hc625ma/simchair_models/Mods/Peripherals/AB412 collective head/VR MAX radio+ panel mod/PNG/nav_side_panel_connections.png

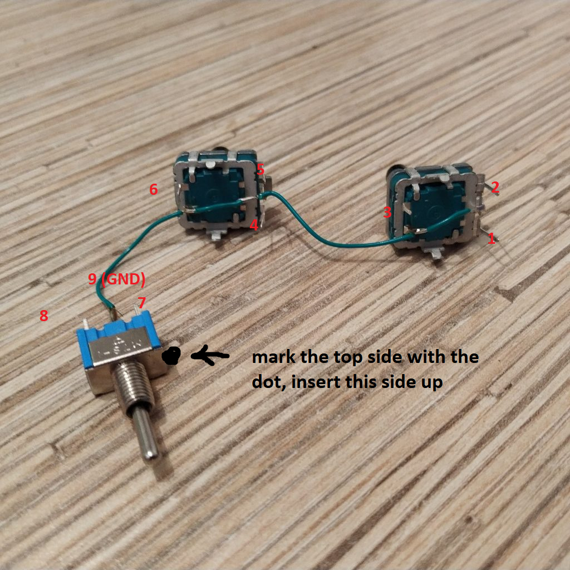
Mods/Peripherals/AB412 collective head/VR MAX radio+ panel mod/PNG/nav_side_panel_connections.png
