hc625ma/simchair_models/Mods/Peripherals/AB412 collective head/VR MAX radio+ panel mod/PNG/vrmax1.png

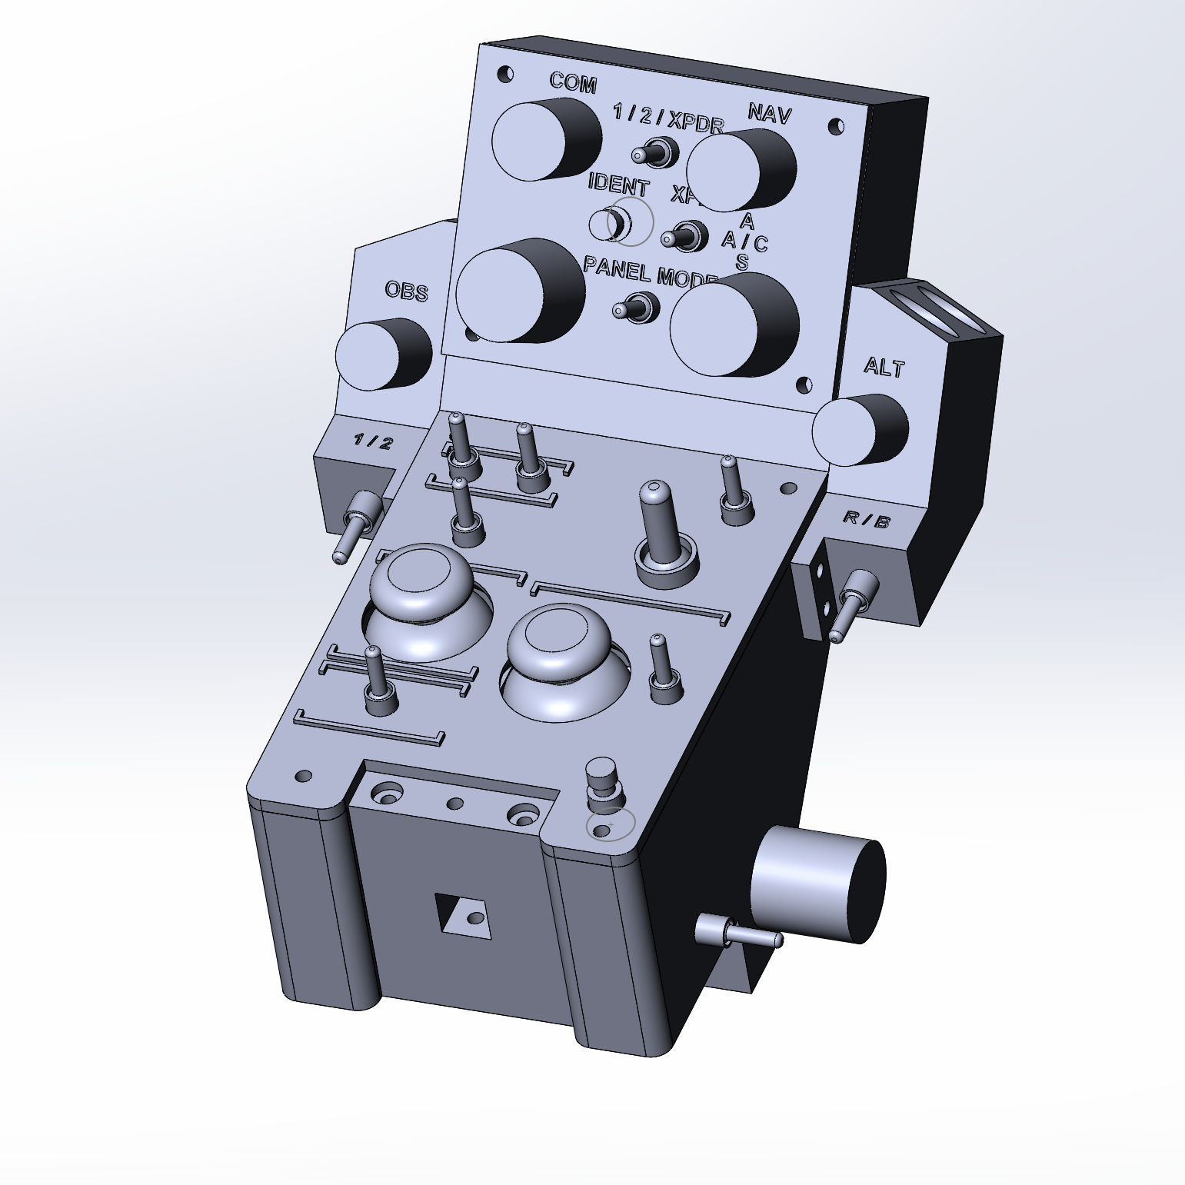
Mods/Peripherals/AB412 collective head/VR MAX radio+ panel mod/PNG/vrmax1.png
