hc625ma/simchair_models/Mods/Peripherals/Collective levers/All levers/Housing with a revision hatch mod/Rubber band version/PNG/housing_with_revision_hatch_rubber_bands_version_01.png

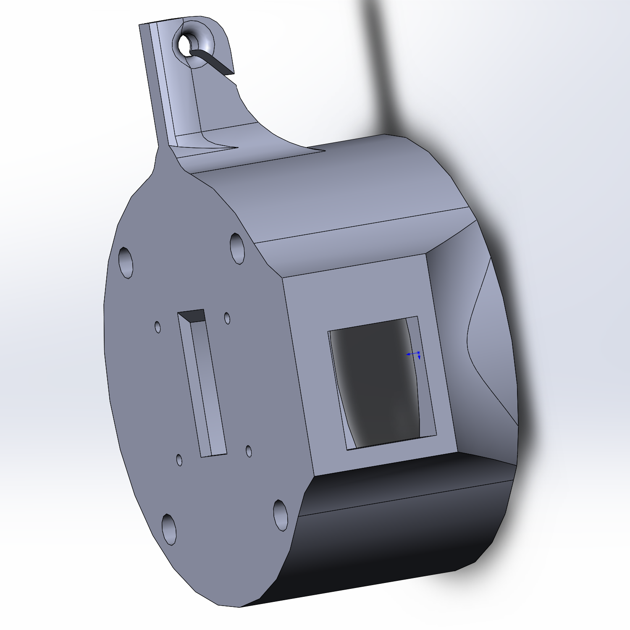
Mods/Peripherals/Collective levers/All levers/Housing with a revision hatch mod/Rubber band version/PNG/housing_with_revision_hatch_rubber_bands_version_01.png
