hc625ma/simchair_models/Mods/Peripherals/Collective levers/All levers/Pneumatic actuator mod/PNG/pneumatic_mod01.png

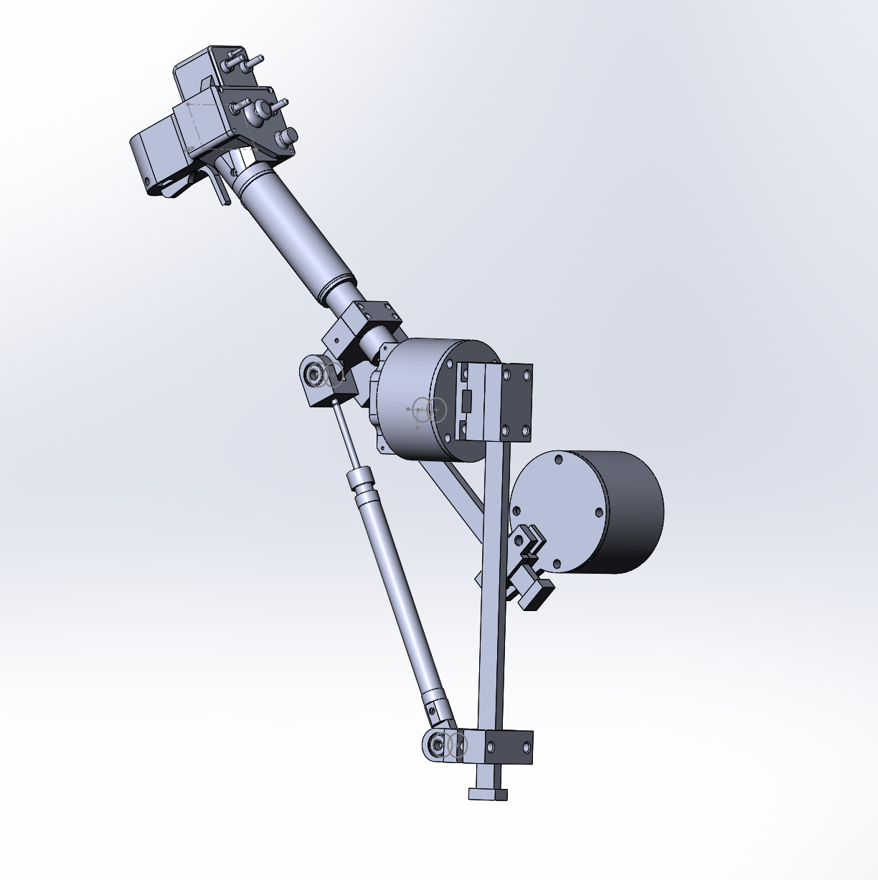
Mods/Peripherals/Collective levers/All levers/Pneumatic actuator mod/PNG/pneumatic_mod01.png
