hc625ma/simchair_models/Mods/Peripherals/Collective levers/Single engine collective/Physical throttle latch mod/PNG/physical_throttle_latch_mod_02.png

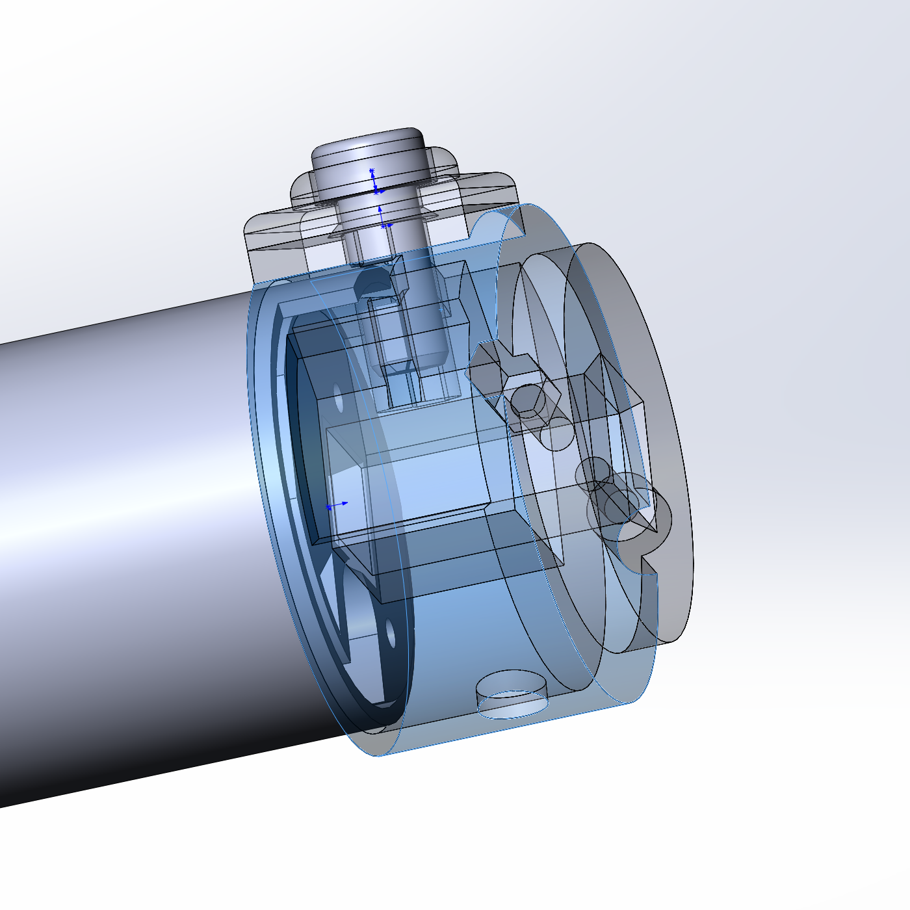
Mods/Peripherals/Collective levers/Single engine collective/Physical throttle latch mod/PNG/physical_throttle_latch_mod_02.png
