hc625ma/simchair_models/Components/Controllers/Simchair MKIII I2C controller/PNG/controller.png

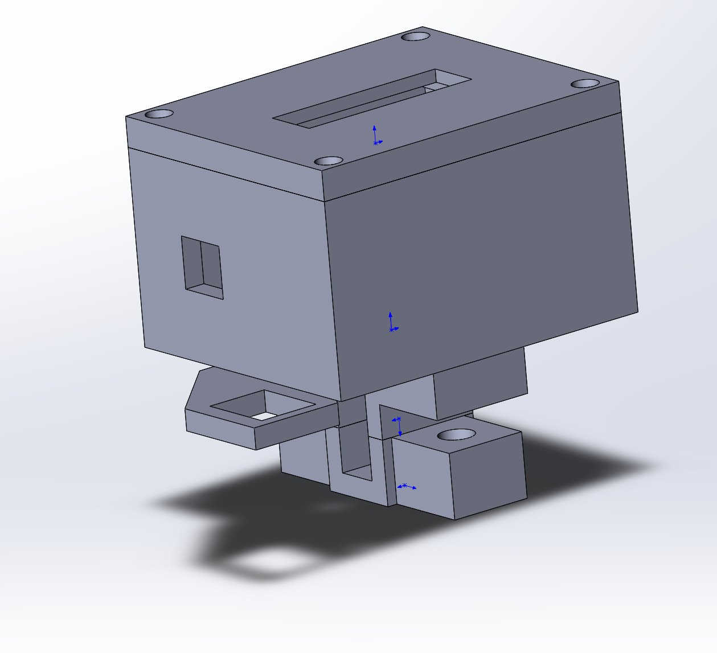
Components/Controllers/Simchair MKIII I2C controller/PNG/controller.png
