hc625ma/simchair_models/Components/Peripherals/Flight stick gimbal 608zz light/PNG/gimbal.png

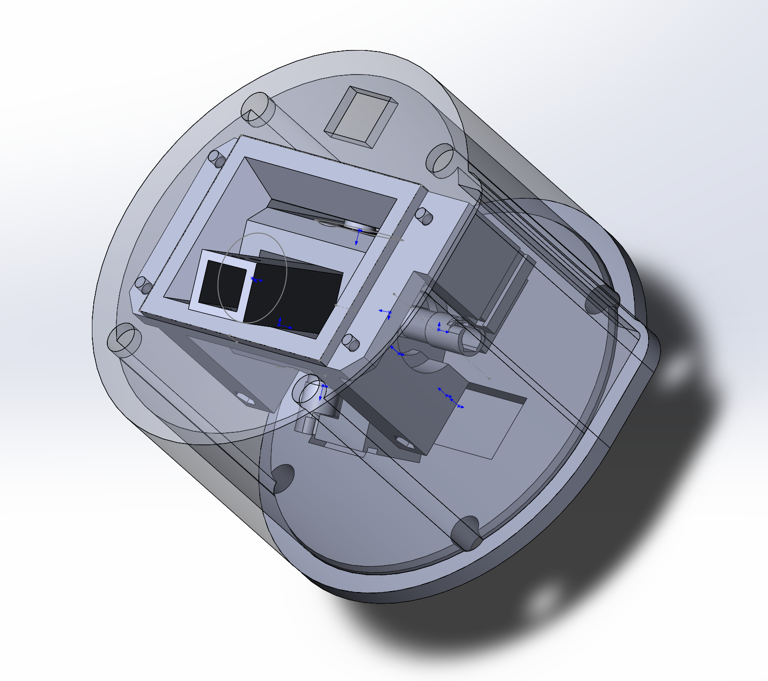
Components/Peripherals/Flight stick gimbal 608zz light/PNG/gimbal.png
