hc625ma/simchair_models/Components/Peripherals/Flight stick gimbal 608zz light/PNG/gimbal_mount_v2.png

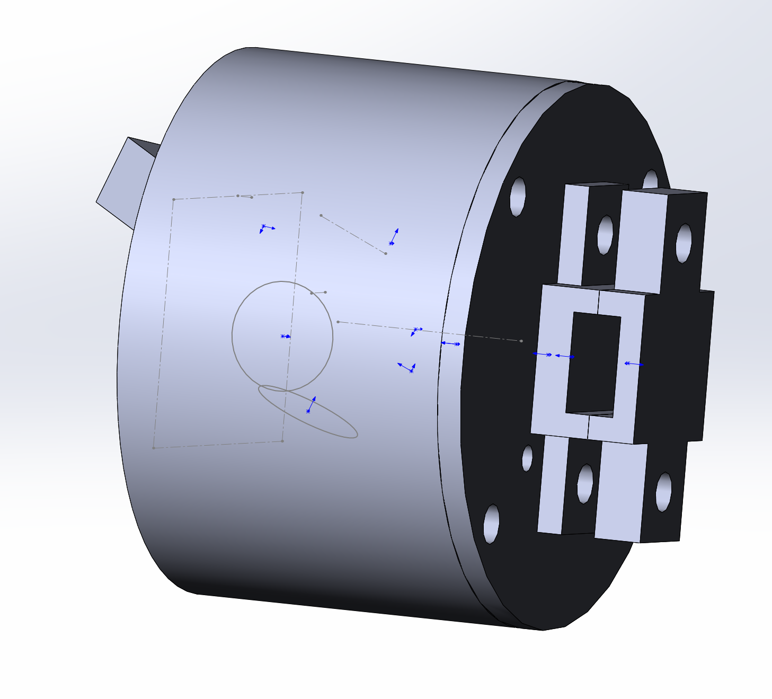
Components/Peripherals/Flight stick gimbal 608zz light/PNG/gimbal_mount_v2.png
