hc625ma/simchair_models/Components/Peripherals/Flight stick gimbal 608zz light/PNG/P_20180517_164954.jpg

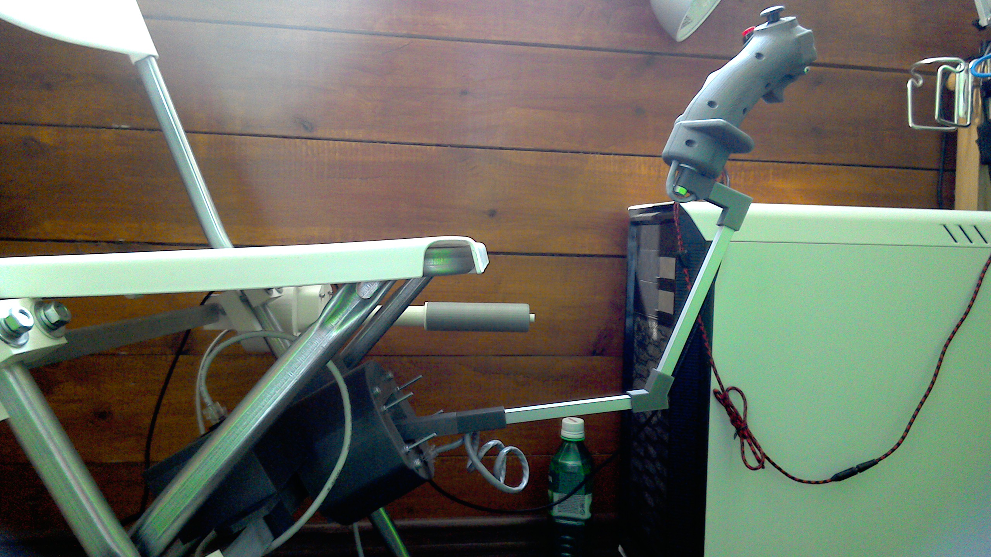
Components/Peripherals/Flight stick gimbal 608zz light/PNG/P_20180517_164954.jpg
