hc625ma/simchair_models/Components/Peripherals/Flight stick gimbal 608zz reinforced/PNG/exploded_view_2.png

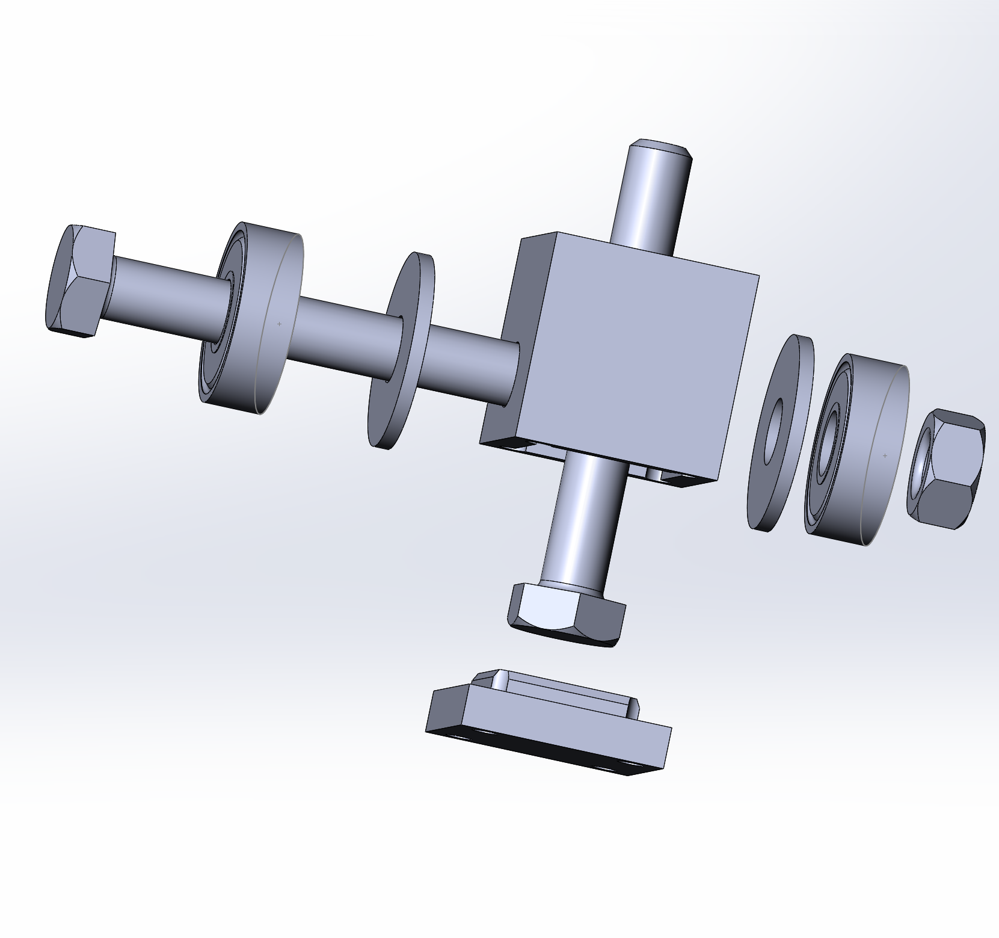
Components/Peripherals/Flight stick gimbal 608zz reinforced/PNG/exploded_view_2.png
