hc625ma/simchair_models/Components/Peripherals/Flight stick gimbal 608zz reinforced/PNG/gimbal01.jpg

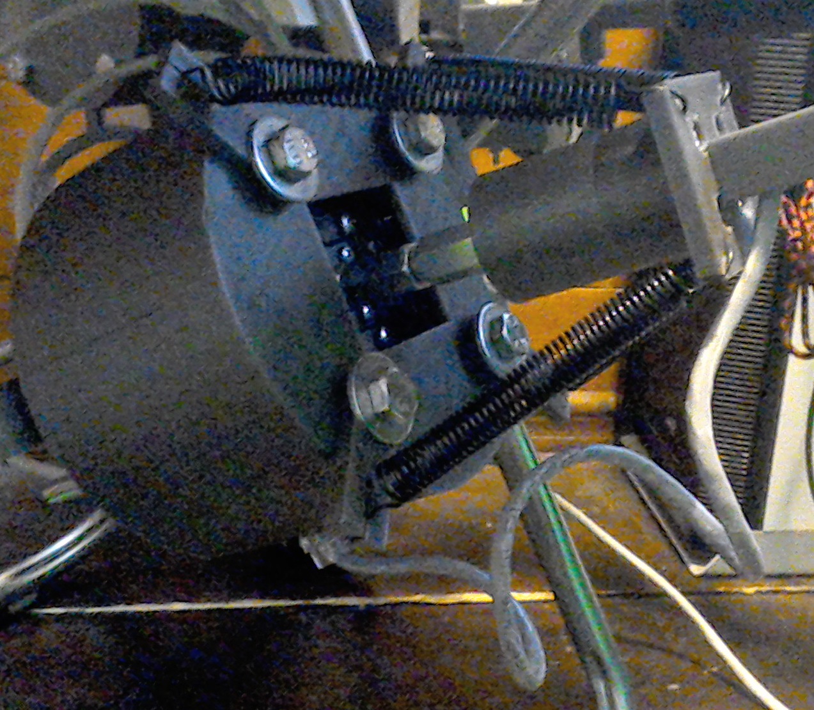
Components/Peripherals/Flight stick gimbal 608zz reinforced/PNG/gimbal01.jpg
