hc625ma/simchair_models/Components/Peripherals/Flight stick gimbal 608zz reinforced/PNG/gimbal08.png

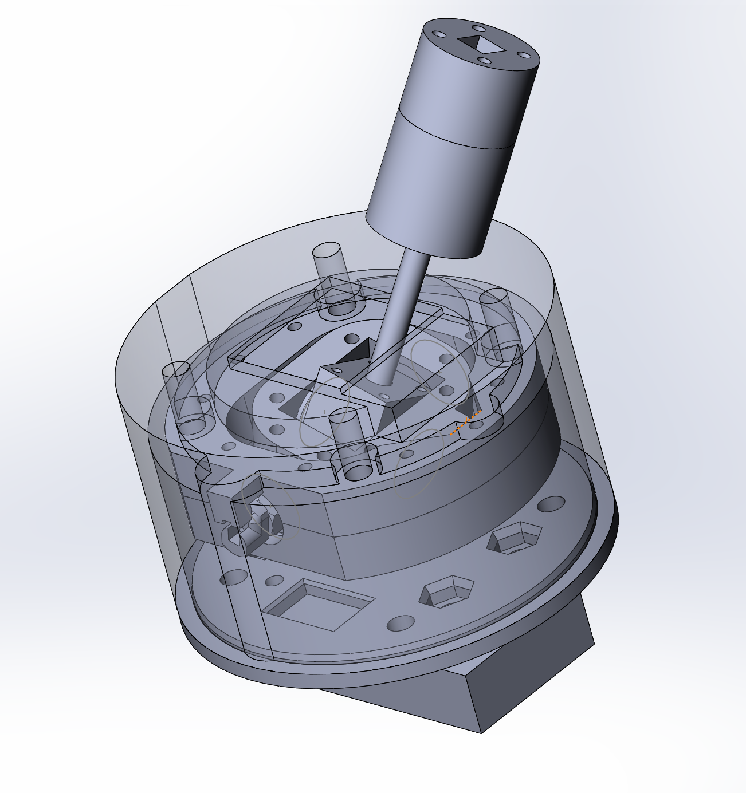
Components/Peripherals/Flight stick gimbal 608zz reinforced/PNG/gimbal08.png
