hc625ma/simchair_models/Components/Peripherals/Helicopter pedals/PNG/magnet and ss495a mounts.JPG

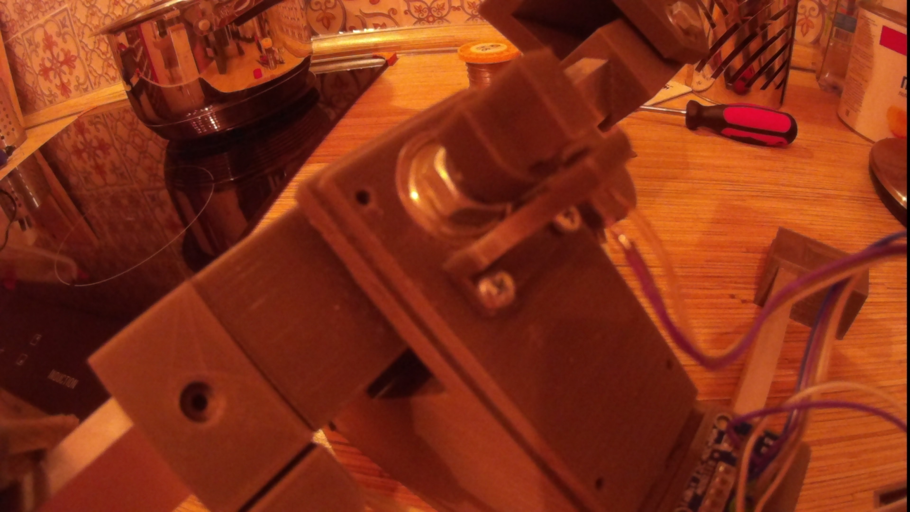
Components/Peripherals/Helicopter pedals/PNG/magnet and ss495a mounts.JPG
