hc625ma/simchair_models/Components/Peripherals/dev/Flight stick gimbal GE25 ES-2RS/SLDPRT/gimbal GE25 ES-2RS.SLDASM

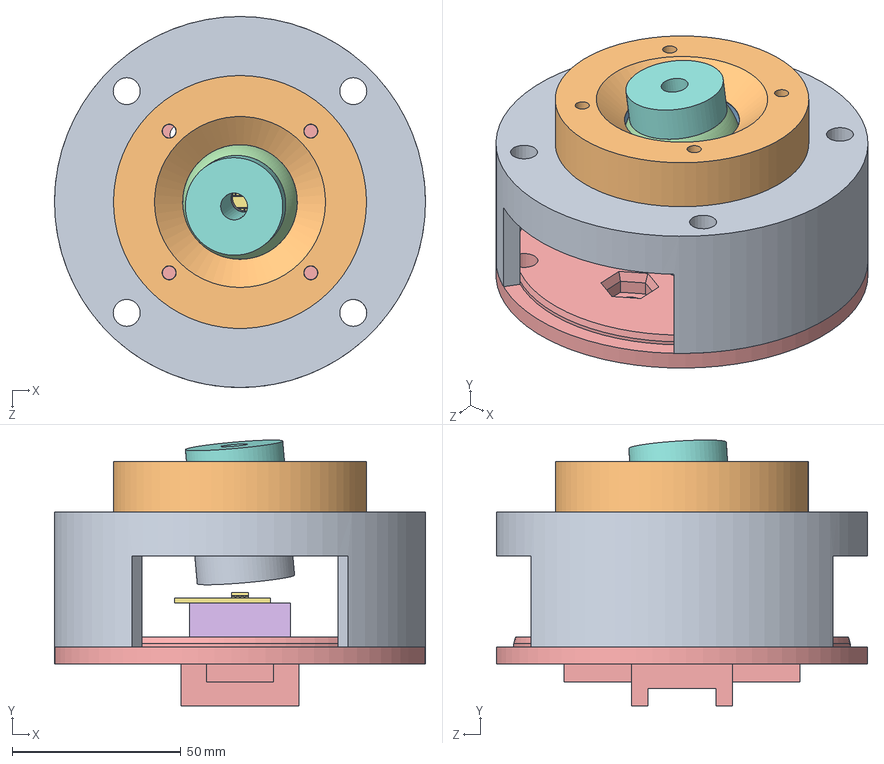
[picture p40: CAD file, 2018-10-22]
Components/Peripherals/dev/Flight stick gimbal GE25 ES-2RS/SLDPRT/gimbal GE25 ES-2RS.SLDASM
110.0 x 78.9 x 110.0 mm
gimbal_housing_testbed_gimbal01a
gimbal_housing_p2_gimbal02
outer_ring
inner_ring
gimbal_housing_bottom_p1_gimbal03
gimbal_cjmcu_frame_gimbal05
CJMCU-93
gimbal_stick_connector_p1_gimbal06
gimbal_stick_connector_p2_gimbal06
