hc625ma/simchair_models/Components/Peripherals/dev/Helicopter throttle quadrant/SLDPRT/throttle_quadrant_module_v3.SLDASM

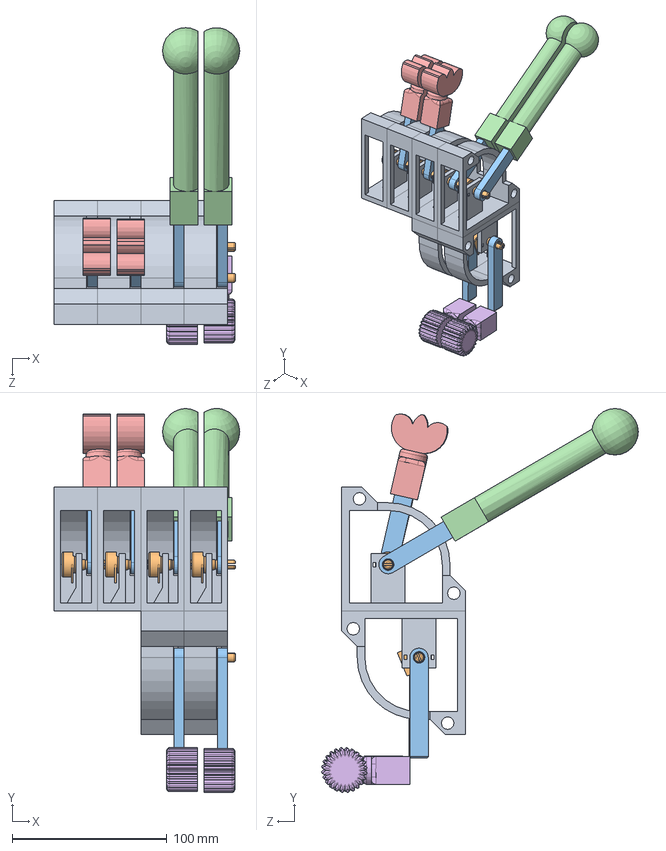
[picture p41: CAD file, 2019-05-10]
Components/Peripherals/dev/Helicopter throttle quadrant/SLDPRT/throttle_quadrant_module_v3.SLDASM
120.0 x 248.2 x 204.7 mm
throttle_quadrant_axis_module_throttle_quadrant01a x 6
16K1-B10K x 6
throttle_quadrant_axis_module_slider_throttle_quadrant02a x 6
mi8_throttle x 2
prop_knob x 2
mix_knob x 2
