hc625ma/simchair_models/Components/Peripherals/Helicopter pedals/SLDPRT/pedals_main_frame_pedals01.SLDPRT

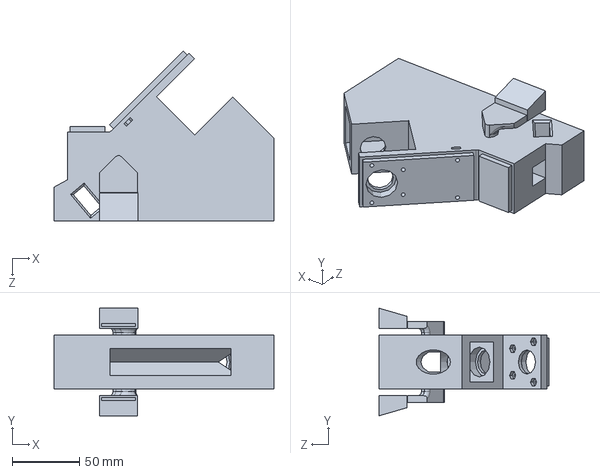
[picture p42: CAD file, 2018-12-12]
Components/Peripherals/Helicopter pedals/SLDPRT/pedals_main_frame_pedals01.SLDPRT
163.6 x 80.0 x 126.1 mm
