hc625ma/simchair_models/Components/Peripherals/Helicopter pedals/SLDPRT/pedals_main_frame_pedals01_backup.SLDPRT

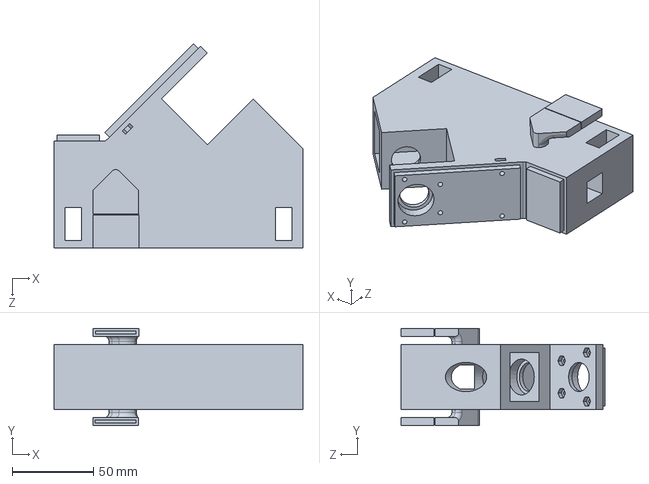
[picture p43: CAD file, 2018-08-10]
Components/Peripherals/Helicopter pedals/SLDPRT/pedals_main_frame_pedals01_backup.SLDPRT
153.6 x 60.0 x 126.1 mm
