hc625ma/simchair_models/Components/Peripherals/dev/Helicopter throttle quadrant/SLDPRT/throttle_quadrant_module.SLDASM

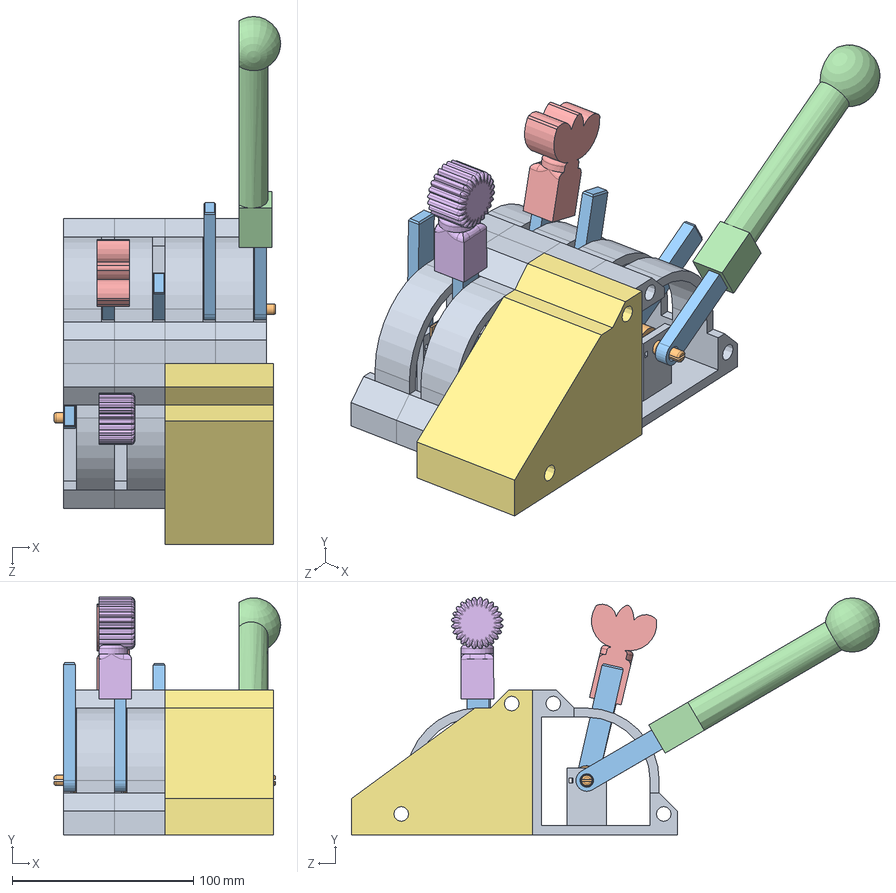
[picture p44: CAD file, 2019-05-10]
Components/Peripherals/dev/Helicopter throttle quadrant/SLDPRT/throttle_quadrant_module.SLDASM
125.2 x 131.2 x 291.7 mm
throttle_quadrant_axis_module_throttle_quadrant01a x 6
16K1-B10K x 6
throttle_quadrant_axis_module_slider_throttle_quadrant02a x 6
mi8_throttle
prop_knob
mix_knob
switch_panel2
