hc625ma/simchair_models/Components/Peripherals/dev/Helicopter throttle quadrant/SLDPRT/quadrant_axis.SLDASM

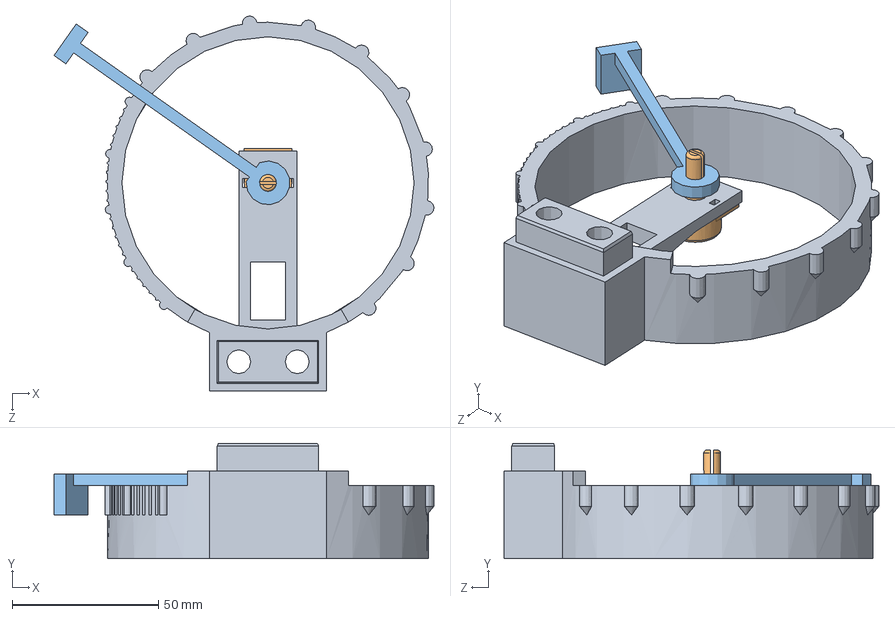
[picture p45: CAD file, 2018-10-25]
Components/Peripherals/dev/Helicopter throttle quadrant/SLDPRT/quadrant_axis.SLDASM
130.1 x 39.5 x 128.4 mm
throttle_quadrant_axis_module_throttle_quadrant01
16K1-B10K
throttle_quadrant_axis_module_slider_throttle_quadrant02
