hc625ma/simchair_models/Components/Peripherals/dev/Helicopter throttle quadrant/SLDPRT/throttle_quadrant_6_axis.SLDASM

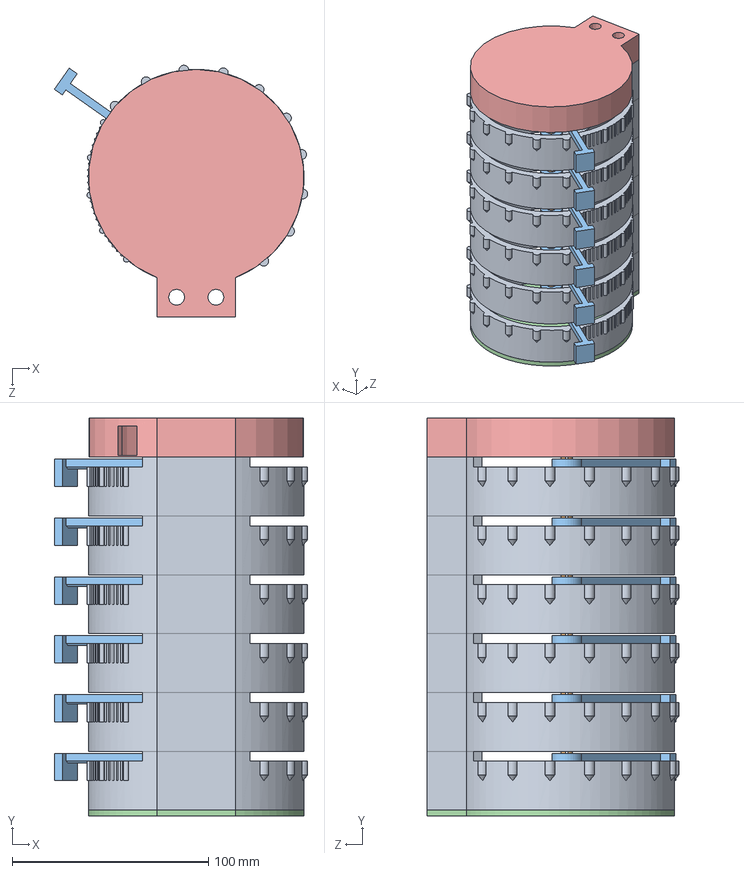
[picture p46: CAD file, 2018-10-25]
Components/Peripherals/dev/Helicopter throttle quadrant/SLDPRT/throttle_quadrant_6_axis.SLDASM
129.2 x 203.0 x 128.4 mm
throttle_quadrant_axis_module_throttle_quadrant01 x 6
16K1-B10K x 6
throttle_quadrant_axis_module_slider_throttle_quadrant02 x 6
throttle_quadrant_left_lid_throttle_quadrant03
throttle_quadrant_right_lid_throttle_quadrant04
