hc625ma/simchair_models/Components/Controllers/Simchair MKIII I2C controller/SLDPRT/controller_enclosure_p1_controller01.SLDPRT

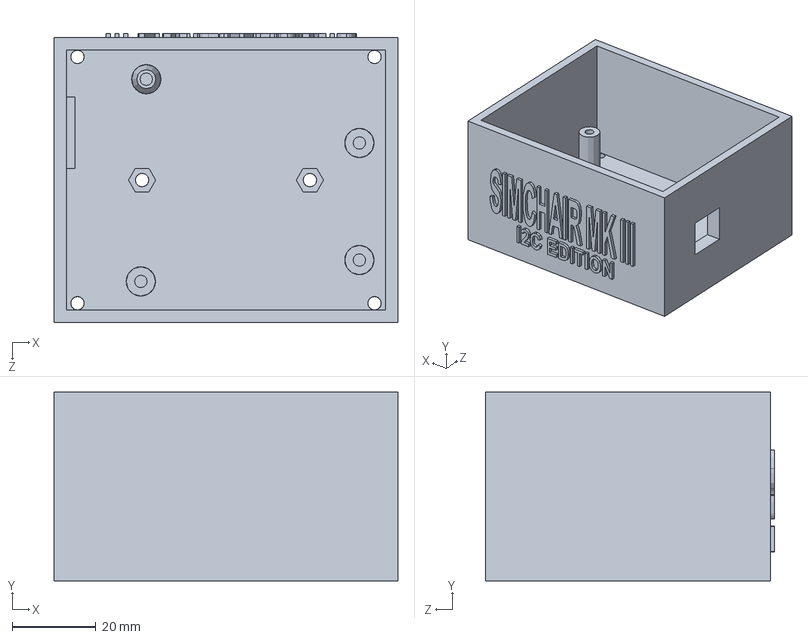
[picture p47: CAD file, 2018-08-29]
Components/Controllers/Simchair MKIII I2C controller/SLDPRT/controller_enclosure_p1_controller01.SLDPRT
82.0 x 45.0 x 69.0 mm
