hc625ma/simchair_models/Components/Frames/40mm construction profile frame/Collective mount/40mm_profile_bracket_p1.SLDPRT

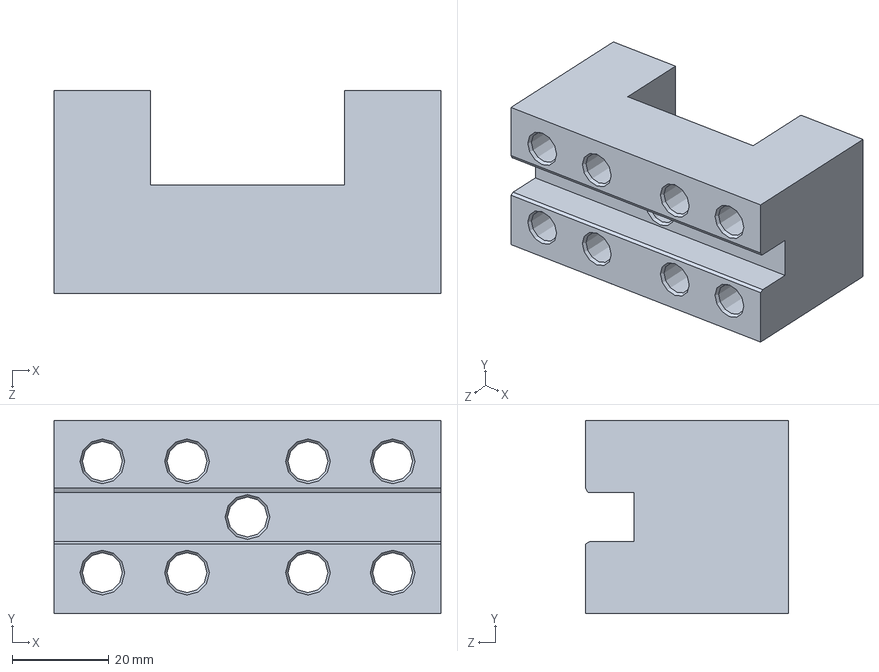
[picture p48: CAD file, 2019-05-31]
Components/Frames/40mm construction profile frame/Collective mount/40mm_profile_bracket_p1.SLDPRT
80.0 x 40.0 x 42.0 mm
