hc625ma/simchair_models/Components/Frames/Generic Chair with vertical round legs/SLDPRT/generic_chair_frame_collective_mount_back_generic_chair03.SLDPRT

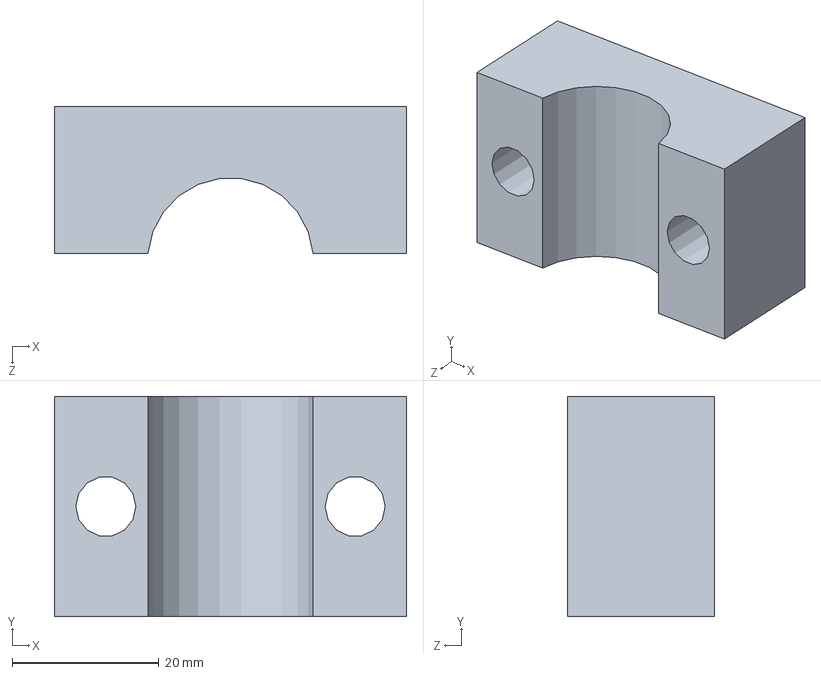
[picture p49: CAD file, 2018-10-19]
Components/Frames/Generic Chair with vertical round legs/SLDPRT/generic_chair_frame_collective_mount_back_generic_chair03.SLDPRT
48.0 x 30.0 x 20.0 mm
