hc625ma/simchair_models/Components/Frames/IKEA GUNDE frame/Chair mounts/SLDPRT/ikea_gunde_frame_throttle_quadrant_frame_mount_p1_ikea_gunde_frame07.SLDPRT

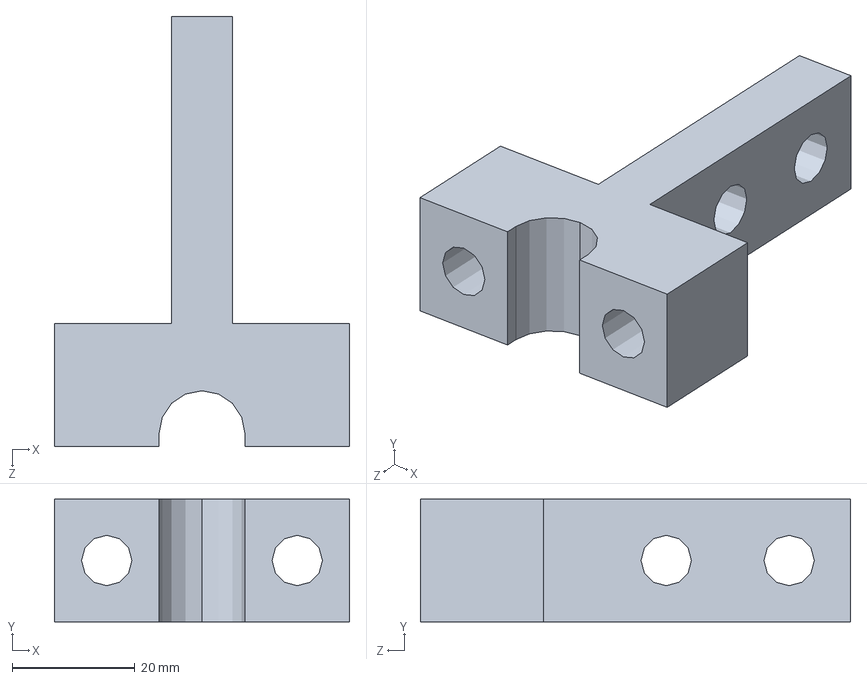
[picture p50: CAD file, 2018-10-25]
Components/Frames/IKEA GUNDE frame/Chair mounts/SLDPRT/ikea_gunde_frame_throttle_quadrant_frame_mount_p1_ikea_gunde_frame07.SLDPRT
48.0 x 20.0 x 70.0 mm
