hc625ma/simchair_models/Components/Frames/IKEA GUNDE frame/Chair mounts/STL/ikea_gunde_chair_back_mount_malinda_plate.stl

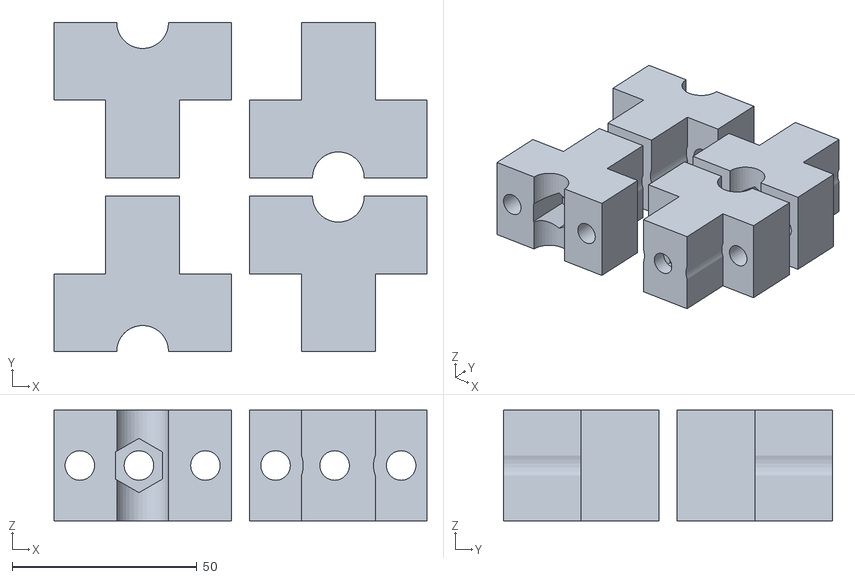
[picture p51: CAD file, 2018-08-11]
Components/Frames/IKEA GUNDE frame/Chair mounts/STL/ikea_gunde_chair_back_mount_malinda_plate.stl
101.0 x 89.0 x 30.0
