hc625ma/simchair_models/Components/Frames/IKEA GUNDE frame/Cyclic stick frame parts/Non-spring-loaded stick/SLDPRT/gunde_cyclic_frame_stick_grip_connector_pvc_3_4_inch_incr_clearance_vertical_gunde_cyclic_frame04c.SLDPRT

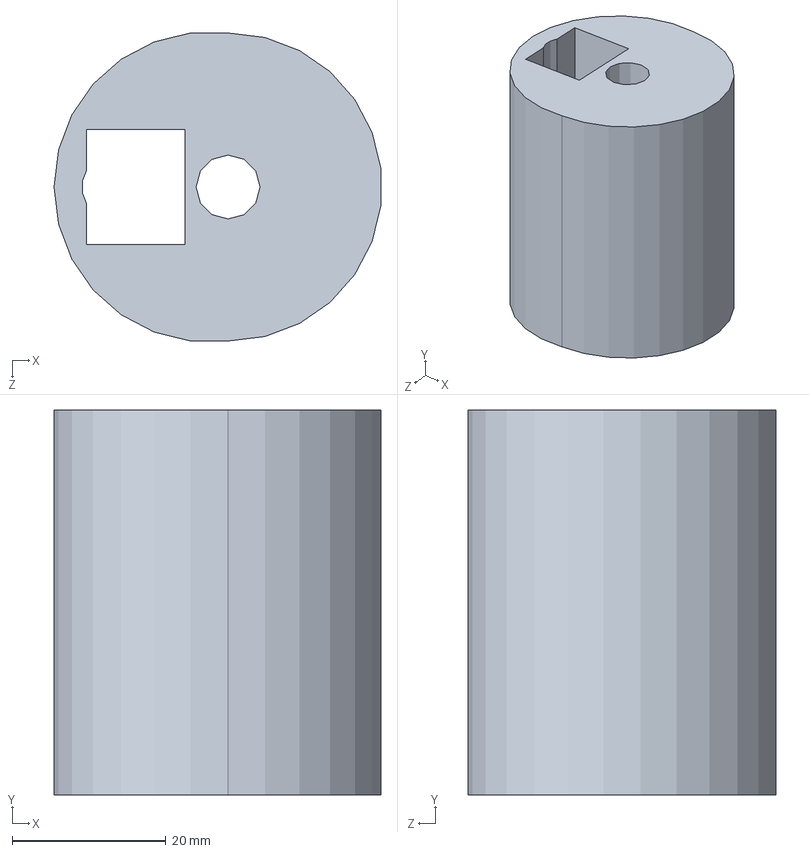
[picture p52: CAD file, 2019-02-21]
Components/Frames/IKEA GUNDE frame/Cyclic stick frame parts/Non-spring-loaded stick/SLDPRT/gunde_cyclic_frame_stick_grip_connector_pvc_3_4_inch_incr_clearance_vertical_gunde_cyclic_frame04c.SLDPRT
42.5 x 50.0 x 40.0 mm
