hc625ma/simchair_models/Components/Frames/IKEA GUNDE frame/Cyclic stick frame parts/Spring-loaded stick/SLDPRT/spring_loaded_cyclic_frame_stick_connector_150_deg_spring_loaded_cyclic_frame01.SLDPRT

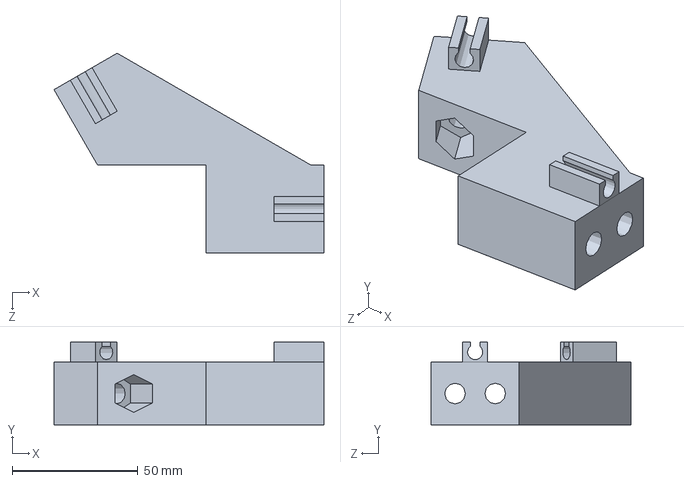
[picture p53: CAD file, 2018-12-24]
Components/Frames/IKEA GUNDE frame/Cyclic stick frame parts/Spring-loaded stick/SLDPRT/spring_loaded_cyclic_frame_stick_connector_150_deg_spring_loaded_cyclic_frame01.SLDPRT
107.5 x 33.0 x 79.5 mm
