hc625ma/simchair_models/Components/Peripherals/AB412 collective head/SLDPRT/ab412_head_enclosure_p1_ab412_head01.SLDPRT

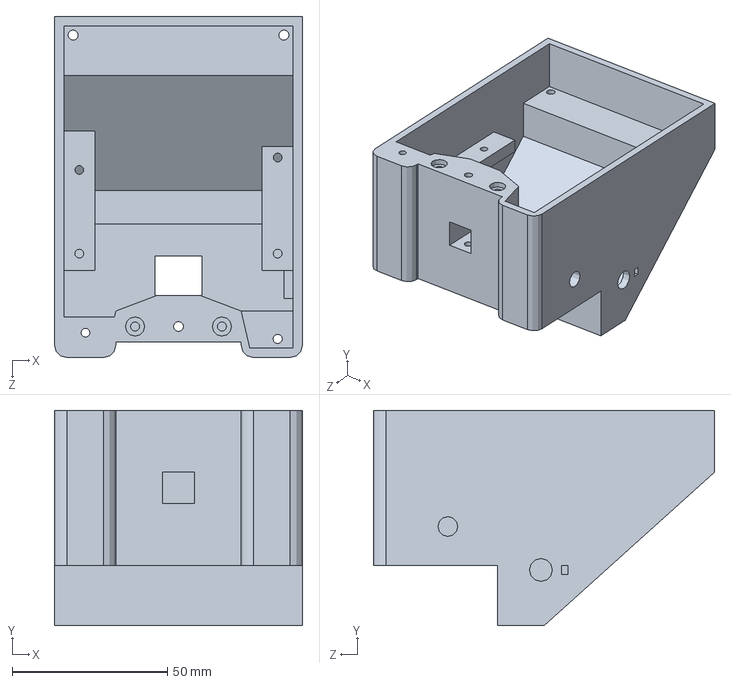
[picture p54: CAD file, 2018-09-01]
Components/Peripherals/AB412 collective head/SLDPRT/ab412_head_enclosure_p1_ab412_head01.SLDPRT
80.0 x 69.5 x 110.0 mm
