hc625ma/simchair_models/Components/Peripherals/AB412 collective head/STL/ab412_head_pot_knob_ab412_head04.STL

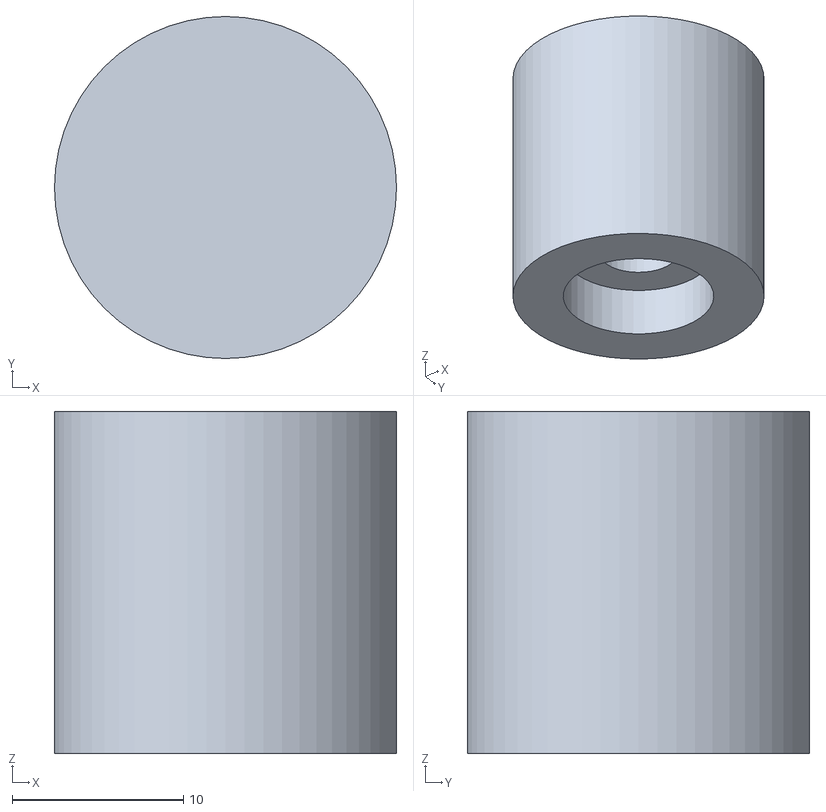
[picture p55: CAD file, 2018-09-01]
Components/Peripherals/AB412 collective head/STL/ab412_head_pot_knob_ab412_head04.STL
20.0 x 20.0 x 20.0
