hc625ma/simchair_models/Components/Peripherals/B8 flight stick/STL/b8stick_left_half_b8stick02.STL

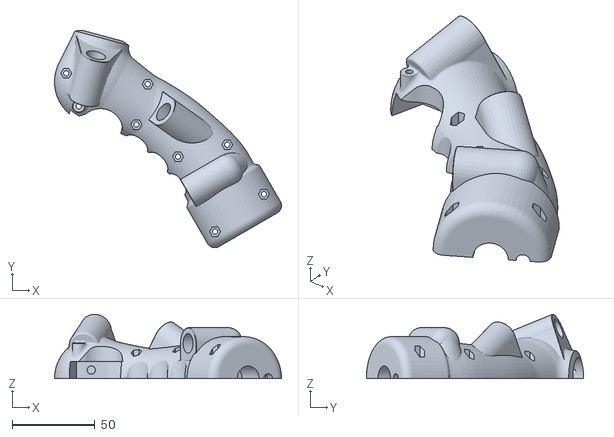
[picture p56: CAD file, 2018-09-20]
Components/Peripherals/B8 flight stick/STL/b8stick_left_half_b8stick02.STL
137.1 x 131.3 x 38.8
