hc625ma/simchair_models/Components/Peripherals/dev/B206 collective head/SLDPRT/b206_head_enclosure_p1_b206_head01.SLDPRT

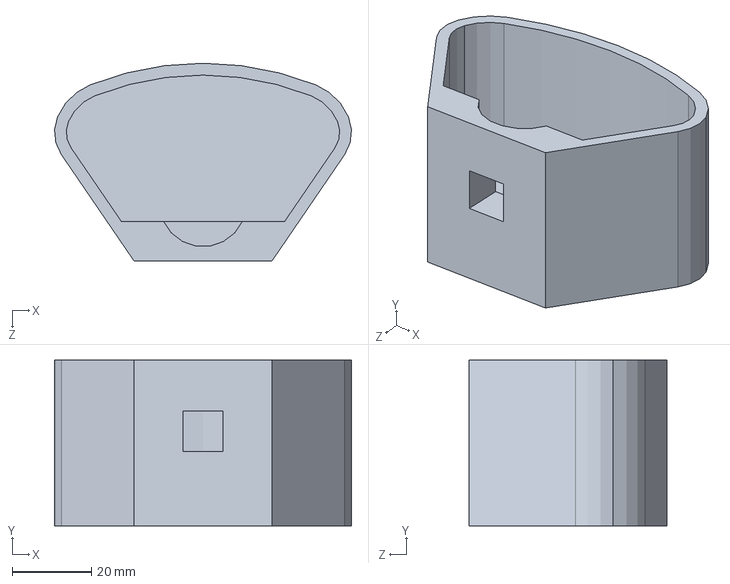
[picture p57: CAD file, 2019-03-17]
Components/Peripherals/dev/B206 collective head/SLDPRT/b206_head_enclosure_p1_b206_head01.SLDPRT
75.2 x 42.0 x 50.0 mm
