hc625ma/simchair_models/Components/Peripherals/dev/Flight stick gimbal 608zz CJMCU-93/Assembly1/gimbal_housing.SLDPRT

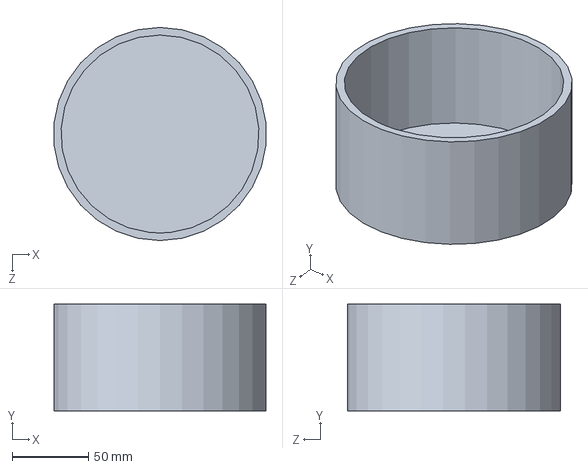
[picture p58: CAD file, 2018-10-22]
Components/Peripherals/dev/Flight stick gimbal 608zz CJMCU-93/Assembly1/gimbal_housing.SLDPRT
139.2 x 70.0 x 140.0 mm
