hc625ma/simchair_models/Components/Peripherals/dev/Flight stick gimbal 608zz reinforced v2/SLDPRT/gimbal_outer_ring_top_gimbal04.SLDPRT

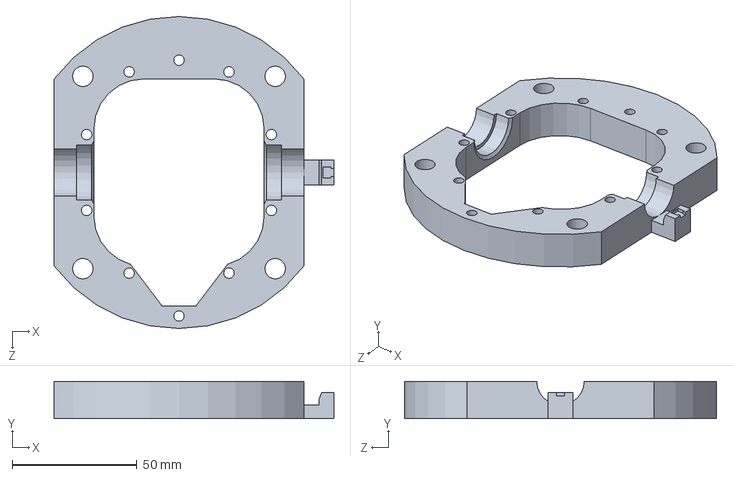
[picture p59: CAD file, 2019-05-10]
Components/Peripherals/dev/Flight stick gimbal 608zz reinforced v2/SLDPRT/gimbal_outer_ring_top_gimbal04.SLDPRT
112.0 x 15.0 x 125.0 mm
