hc625ma/simchair_models/Components/Peripherals/dev/Flight stick gimbal GE25 ES-2RS/SLDPRT/gimbal_cjmcu_frame_gimbal05.SLDPRT

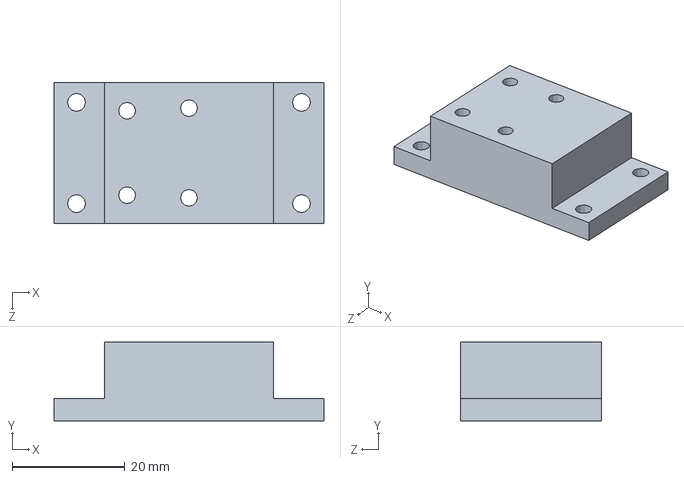
[picture p60: CAD file, 2018-10-22]
Components/Peripherals/dev/Flight stick gimbal GE25 ES-2RS/SLDPRT/gimbal_cjmcu_frame_gimbal05.SLDPRT
48.0 x 14.0 x 25.0 mm
