hc625ma/simchair_models/Components/Peripherals/dev/Helicopter throttle quadrant/SLDPRT/switch_panel2.SLDPRT

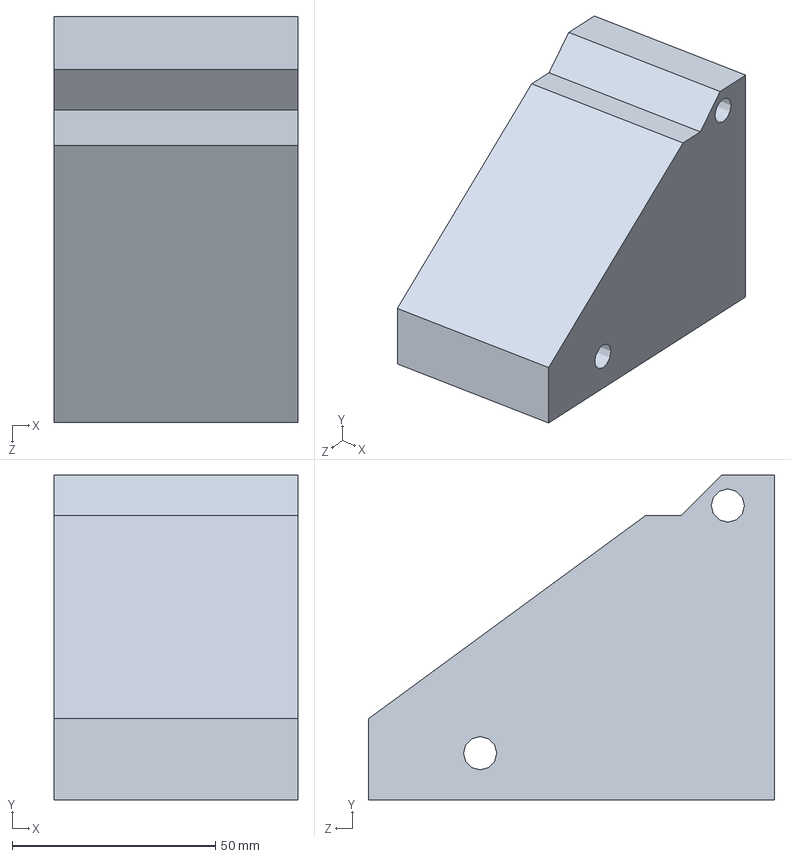
[picture p61: CAD file, 2019-05-10]
Components/Peripherals/dev/Helicopter throttle quadrant/SLDPRT/switch_panel2.SLDPRT
60.0 x 80.0 x 100.0 mm
