hc625ma/simchair_models/Components/Peripherals/dev/Simple collective/STL/throttle_200deg.STL

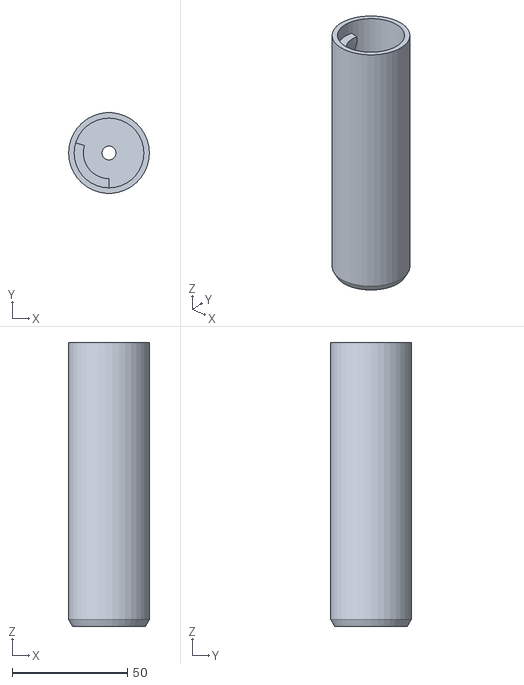
[picture p62: CAD file, 2019-02-21]
Components/Peripherals/dev/Simple collective/STL/throttle_200deg.STL
35.0 x 34.9 x 123.0
