hc625ma/simchair_models/Components/Peripherals/Flight stick gimbal 608zz reinforced/STL/gimbal_housing_lid_p1_gimbal02.STL

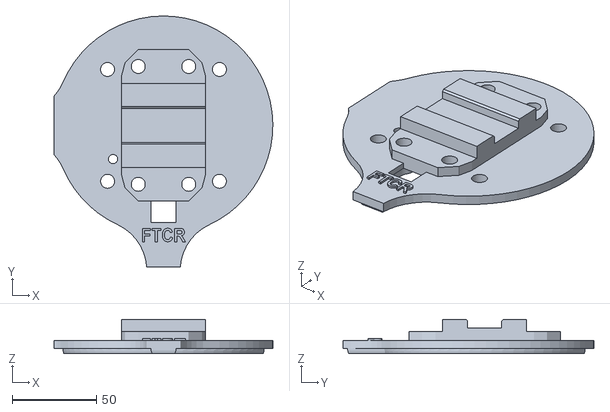
[picture p63: CAD file, 2019-03-17]
Components/Peripherals/Flight stick gimbal 608zz reinforced/STL/gimbal_housing_lid_p1_gimbal02.STL
130.0 x 149.2 x 20.5
