hc625ma/simchair_models/Components/Peripherals/Huey collective head/STL/huey_head_enclosure_p1_huey_head01.STL

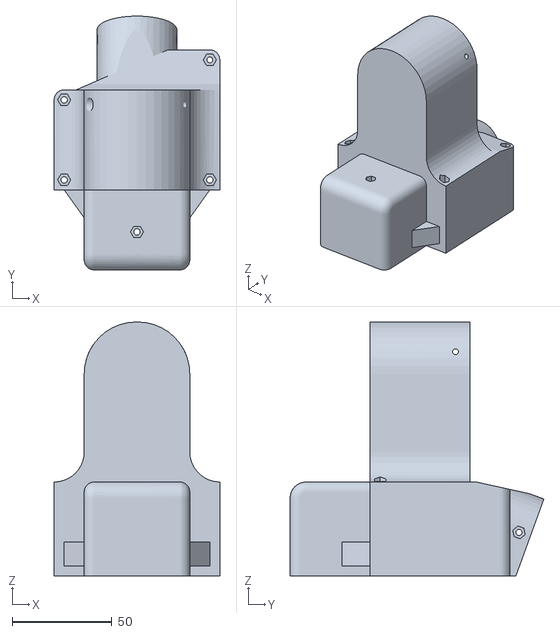
[picture p64: CAD file, 2018-08-29]
Components/Peripherals/Huey collective head/STL/huey_head_enclosure_p1_huey_head01.STL
82.8 x 126.9 x 127.0
