hc625ma/simchair_models/Components/Peripherals/Single collective/SLDPRT/single_collective_throttle_frame_p2_single_collective10.SLDPRT

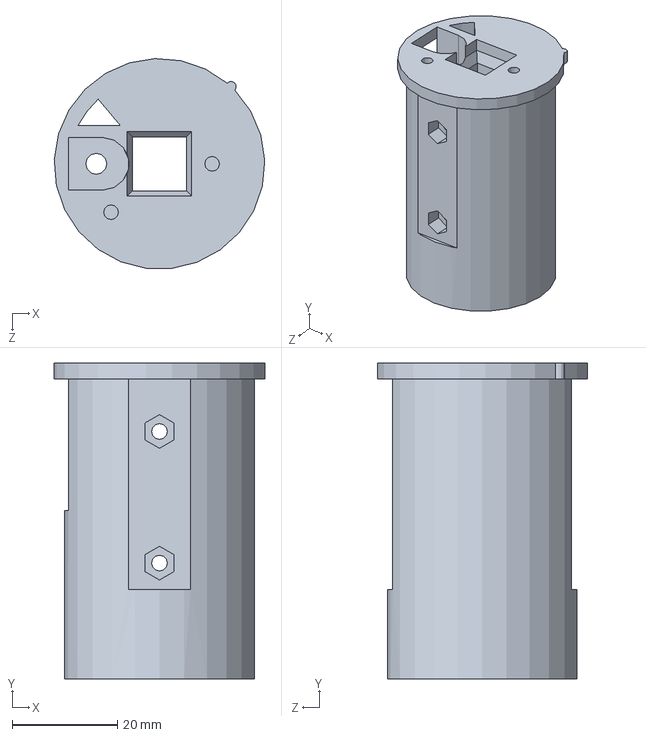
[picture p65: CAD file, 2019-05-10]
Components/Peripherals/Single collective/SLDPRT/single_collective_throttle_frame_p2_single_collective10.SLDPRT
40.0 x 60.0 x 39.8 mm
