hc625ma/simchair_models/Components/Peripherals/Single collective/STL/single_collective_lever_connector_single_collective05a.STL

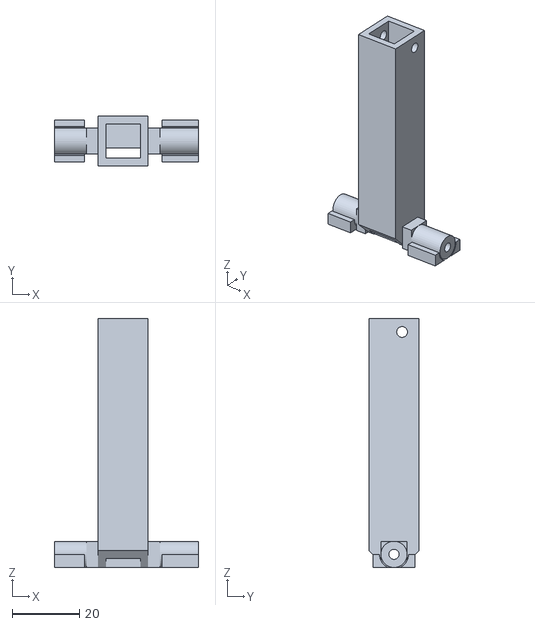
[picture p66: CAD file, 2019-05-10]
Components/Peripherals/Single collective/STL/single_collective_lever_connector_single_collective05a.STL
42.8 x 14.8 x 74.0
