hc625ma/simchair_models/Components/Peripherals/Twin collective/STL/twin_collective_enclosure_bottom_p2_twin_collective03.STL

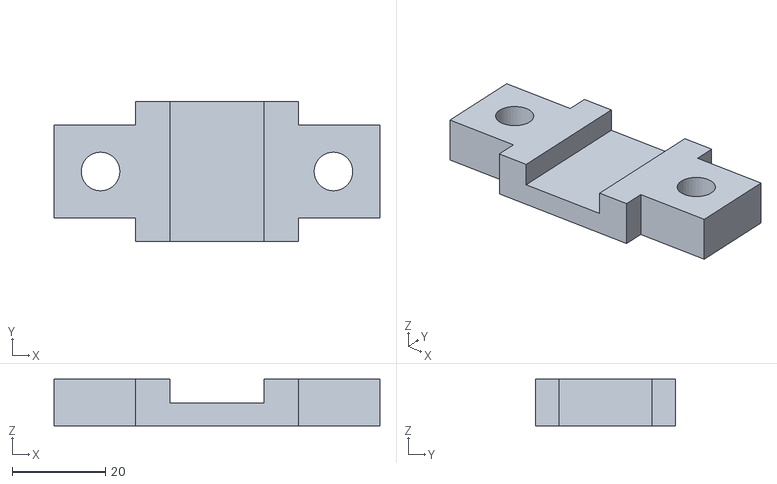
[picture p67: CAD file, 2018-08-11]
Components/Peripherals/Twin collective/STL/twin_collective_enclosure_bottom_p2_twin_collective03.STL
70.0 x 30.0 x 10.0
