hc625ma/simchair_models/Hardware Models/Buttons/PBS-11/pbs11.SLDPRT

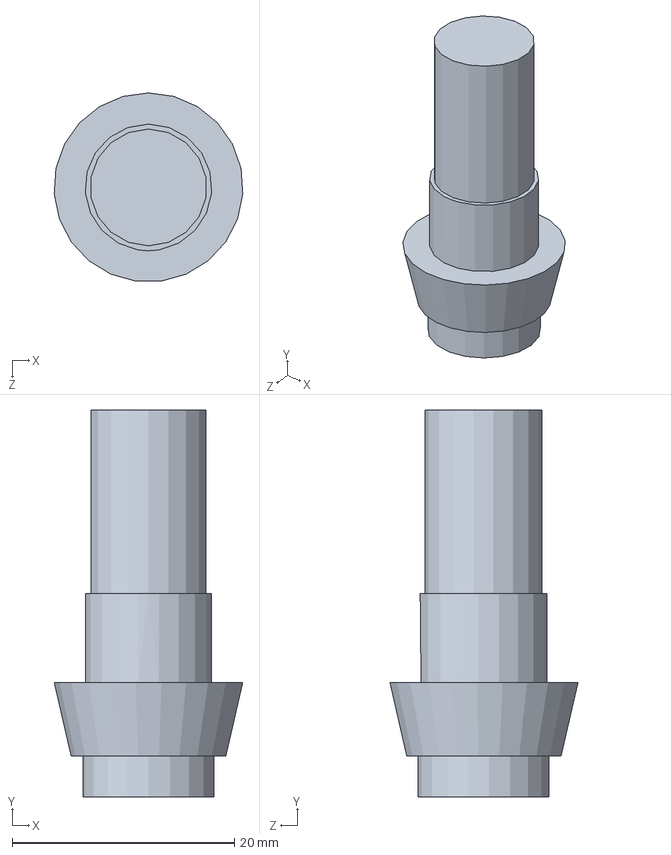
[picture p68: CAD file, 2019-03-23]
Hardware Models/Buttons/PBS-11/pbs11.SLDPRT
17.0 x 34.8 x 16.9 mm
