hc625ma/simchair_models/Hardware Models/KY-083.SLDPRT

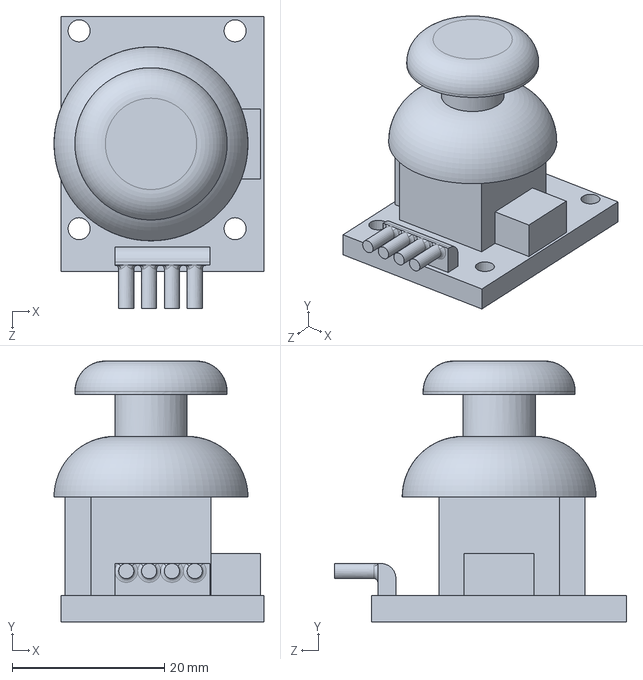
[picture p69: CAD file, 2019-03-23]
Hardware Models/KY-083.SLDPRT
27.6 x 34.3 x 38.4 mm
