hc625ma/simchair_models/Hardware Models/KY-083/KY-083_no_hat.SLDPRT

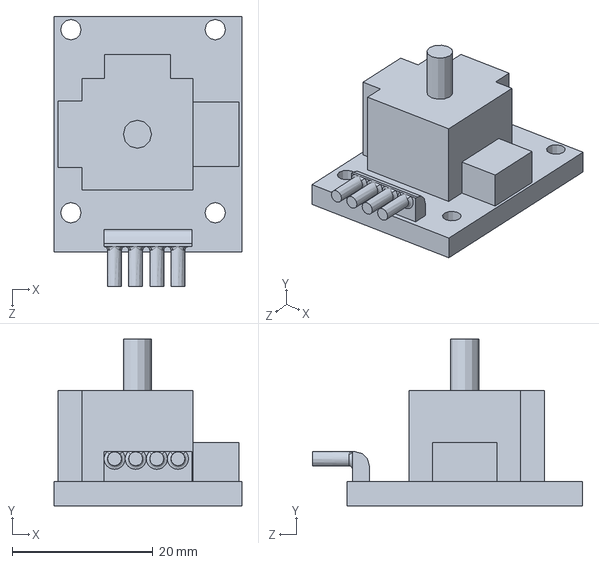
[picture p70: CAD file, 2019-03-23]
Hardware Models/KY-083/KY-083_no_hat.SLDPRT
26.7 x 23.7 x 38.4 mm
