hc625ma/simchair_models/Hardware Models/Magnets/6x6x4mm_square.SLDPRT

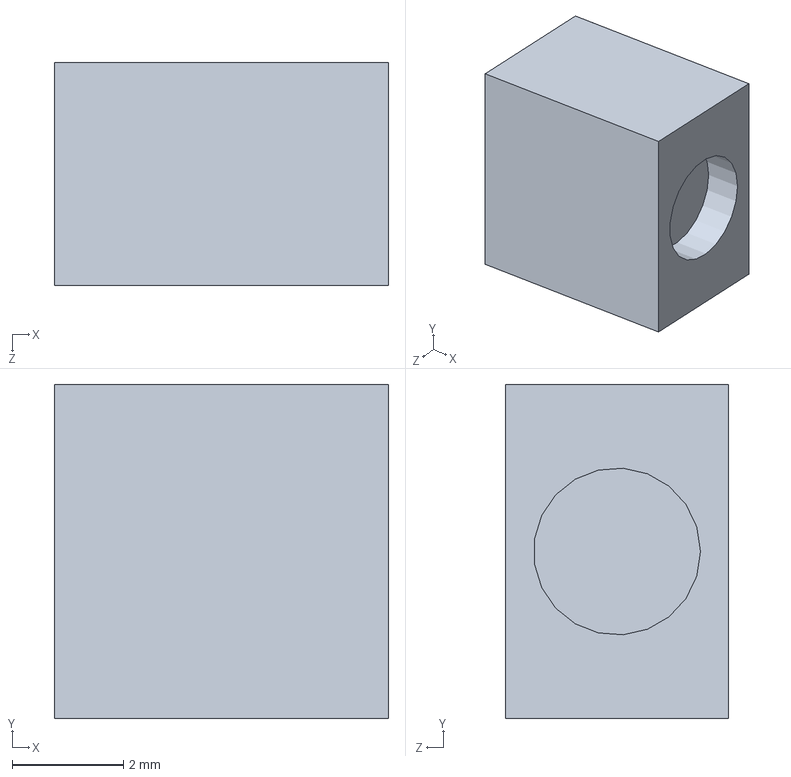
[picture p71: CAD file, 2019-05-31]
Hardware Models/Magnets/6x6x4mm_square.SLDPRT
6.00 x 6.00 x 4.00 mm
