hc625ma/simchair_models/Hardware Models/Rotary pots/16K1-B10K.SLDPRT

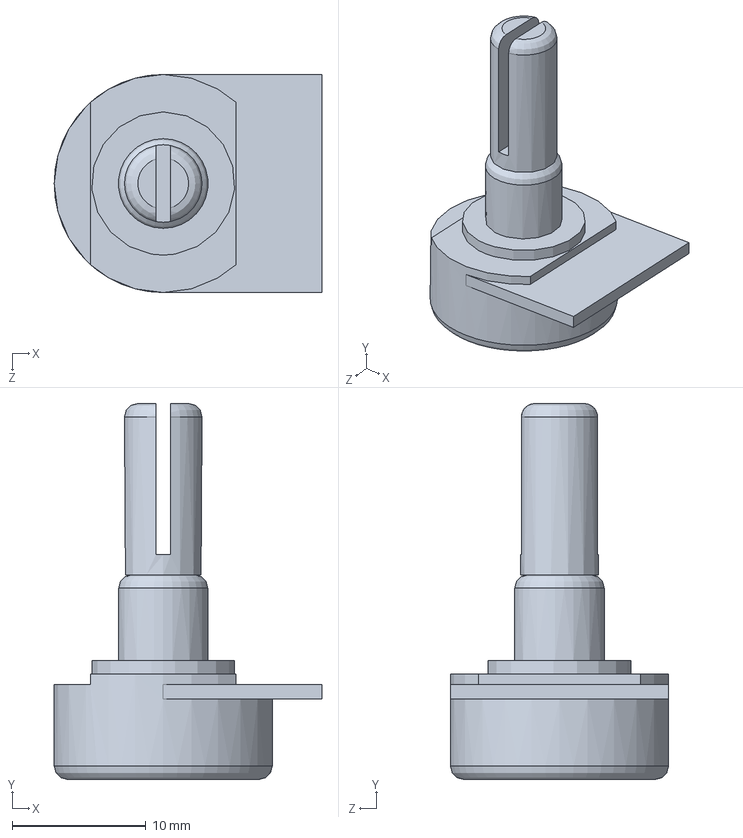
[picture p72: CAD file, 2018-10-25]
Hardware Models/Rotary pots/16K1-B10K.SLDPRT
20.0 x 28.1 x 16.3 mm
