hc625ma/simchair_models/Mods/Controllers/Simchair MKIII I2C controller/SLDPRT/controller_enclosure_p2a_6_sockets_controller02a.SLDPRT

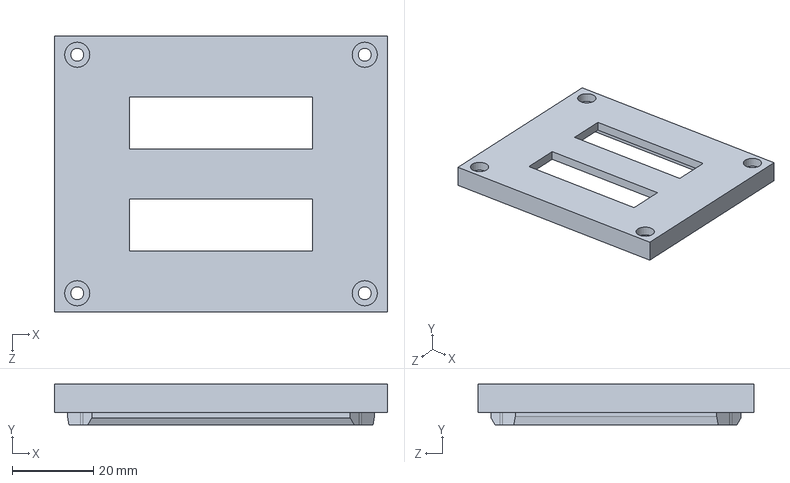
[picture p73: CAD file, 2018-08-11]
Mods/Controllers/Simchair MKIII I2C controller/SLDPRT/controller_enclosure_p2a_6_sockets_controller02a.SLDPRT
82.0 x 10.0 x 68.0 mm
