hc625ma/simchair_models/Mods/Frames/IKEA GUNDE frame/Chair mounts, increased clearance/SLDPRT/ikea_gunde_frame_0.4mm_ikea_malinda_chair_back_mount_ikea_gunde_frame_06a.SLDPRT

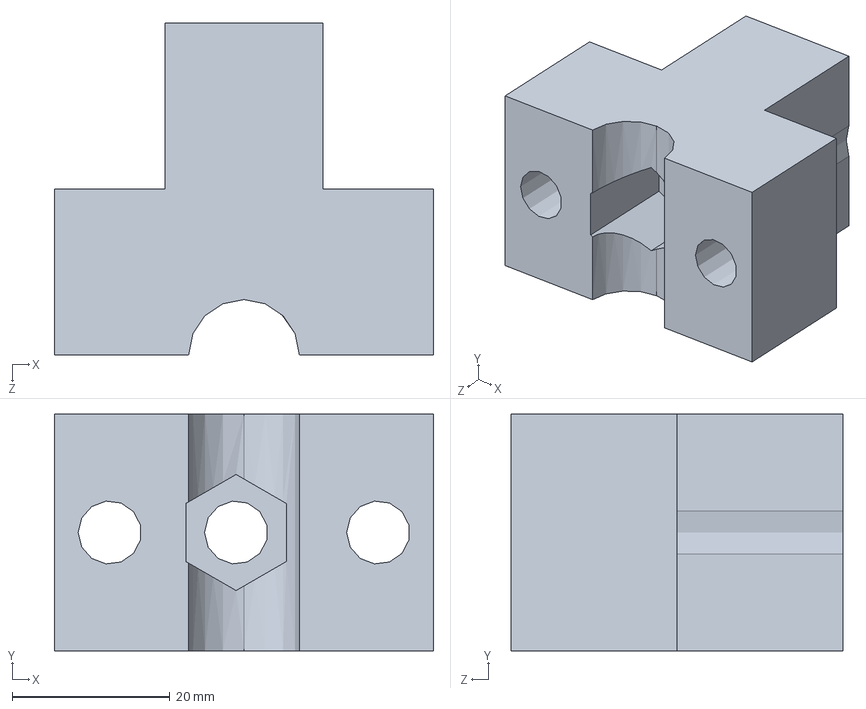
[picture p74: CAD file, 2019-02-06]
Mods/Frames/IKEA GUNDE frame/Chair mounts, increased clearance/SLDPRT/ikea_gunde_frame_0.4mm_ikea_malinda_chair_back_mount_ikea_gunde_frame_06a.SLDPRT
48.0 x 30.0 x 42.0 mm
