hc625ma/simchair_models/Mods/Frames/IKEA GUNDE frame/Chair mounts, increased clearance/STL/ikea_gunde_0,4mm_frame_cyclic_frame_mount_ikea_gunde_frame01a.STL

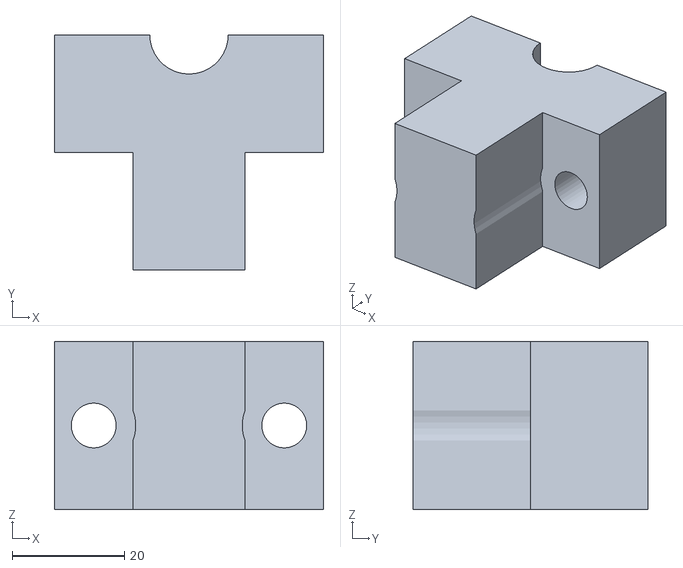
[picture p75: CAD file, 2019-02-06]
Mods/Frames/IKEA GUNDE frame/Chair mounts, increased clearance/STL/ikea_gunde_0,4mm_frame_cyclic_frame_mount_ikea_gunde_frame01a.STL
48.0 x 42.0 x 30.0
