hc625ma/simchair_models/Mods/Frames/IKEA GUNDE frame/Collective mount, 30 deg lever inclination/SLDPRT/ikea_gunde_frame_collective_frame_mount_straight_right_ikea_gunde_frame03a.SLDPRT

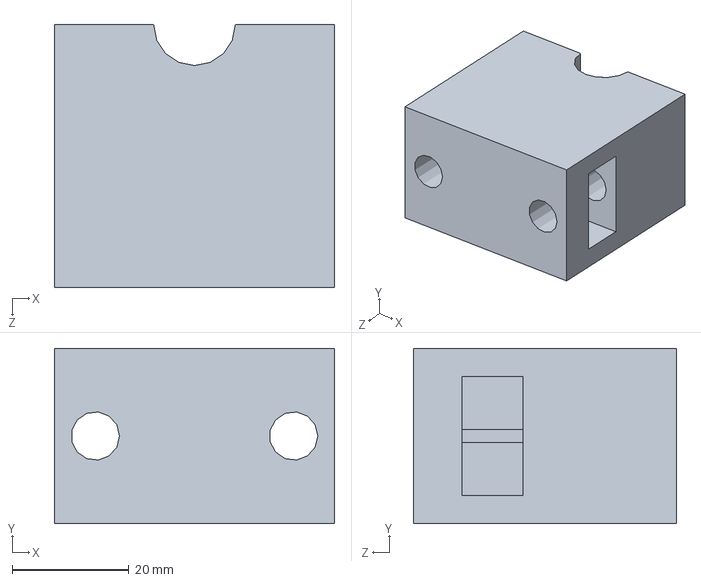
[picture p76: CAD file, 2019-05-31]
Mods/Frames/IKEA GUNDE frame/Collective mount, 30 deg lever inclination/SLDPRT/ikea_gunde_frame_collective_frame_mount_straight_right_ikea_gunde_frame03a.SLDPRT
48.0 x 30.0 x 45.0 mm
