hc625ma/simchair_models/Mods/Peripherals/AB412 collective head/Other/SLDPRT/ab412_head_enclosure_front_cover_radio_panel_ready_ab412_head05.SLDPRT

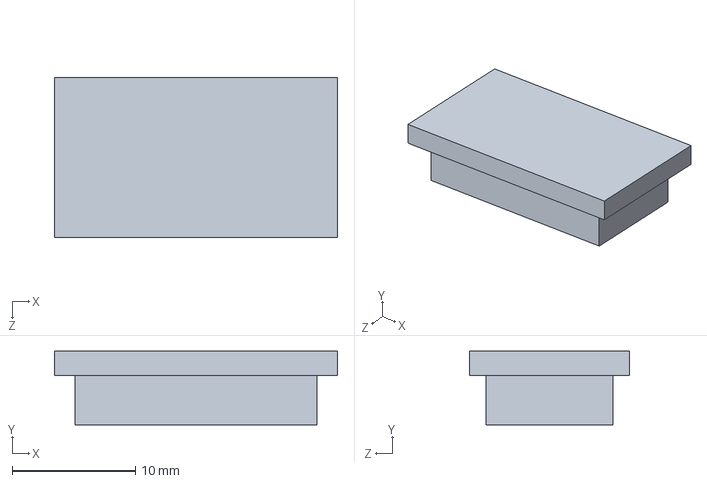
[picture p77: CAD file, 2019-04-12]
Mods/Peripherals/AB412 collective head/Other/SLDPRT/ab412_head_enclosure_front_cover_radio_panel_ready_ab412_head05.SLDPRT
23.0 x 6.00 x 13.0 mm
