hc625ma/simchair_models/Mods/Peripherals/AB412 collective head/Other/STL/ab412_head_pot_knob_ab412_head04a.STL

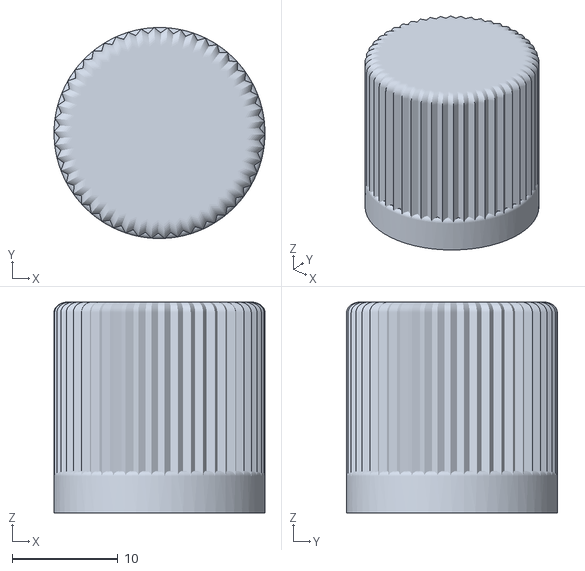
[picture p78: CAD file, 2019-03-30]
Mods/Peripherals/AB412 collective head/Other/STL/ab412_head_pot_knob_ab412_head04a.STL
20.0 x 20.0 x 20.0
