hc625ma/simchair_models/Mods/Peripherals/AB412 collective head/VR MAX radio+ panel mod/SLDPRT/ab412_head_radio_panel_housing_p4_ab412_head_radio_panel07.SLDPRT

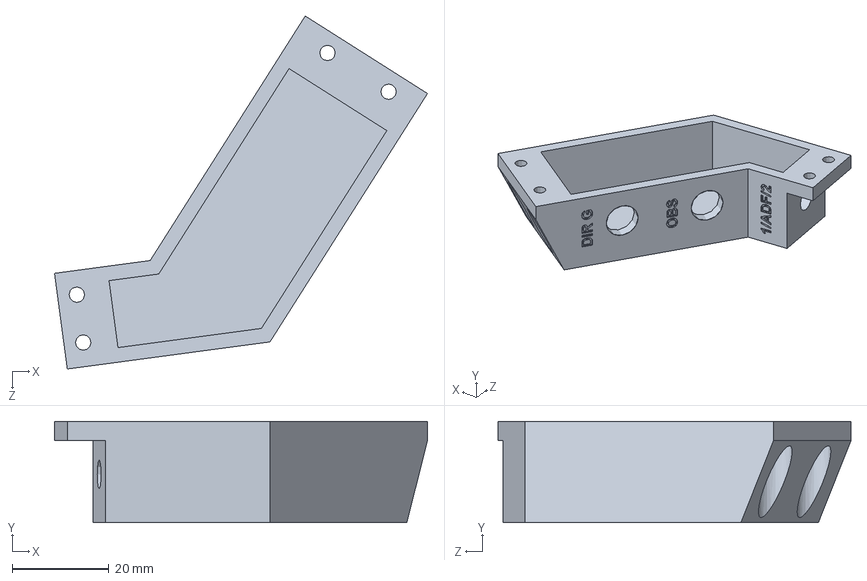
[picture p79: CAD file, 2019-03-30]
Mods/Peripherals/AB412 collective head/VR MAX radio+ panel mod/SLDPRT/ab412_head_radio_panel_housing_p4_ab412_head_radio_panel07.SLDPRT
77.3 x 21.0 x 73.1 mm
