hc625ma/simchair_models/Mods/Peripherals/B8 flight stick/b8stick_left_half_imperial_nuts_4-40_b8stick02a.STL

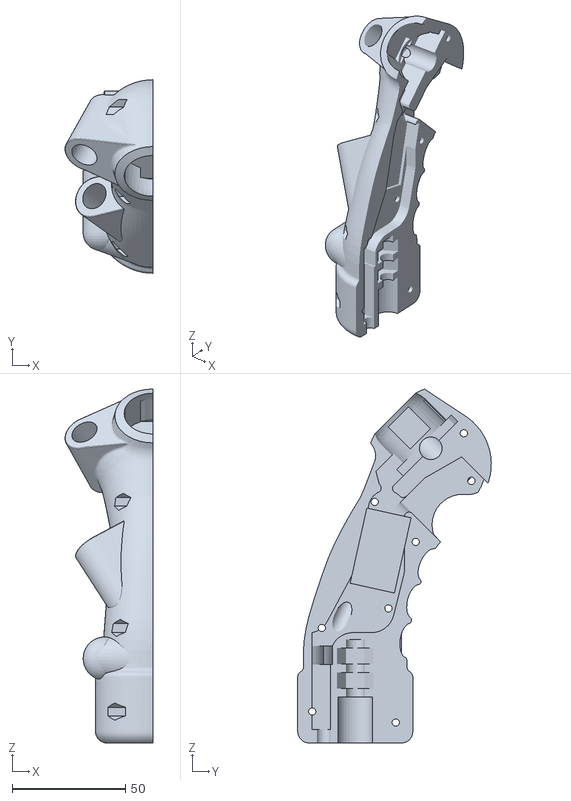
[picture p80: CAD file, 2019-03-17]
Mods/Peripherals/B8 flight stick/b8stick_left_half_imperial_nuts_4-40_b8stick02a.STL
38.8 x 85.4 x 156.2
