hc625ma/simchair_models/Mods/Peripherals/Collective levers/All levers/5x5 magnet holder mod/SLDPRT/single_collective_magnet_holder_5x5mm_socket_offset_single_collective7b.SLDPRT

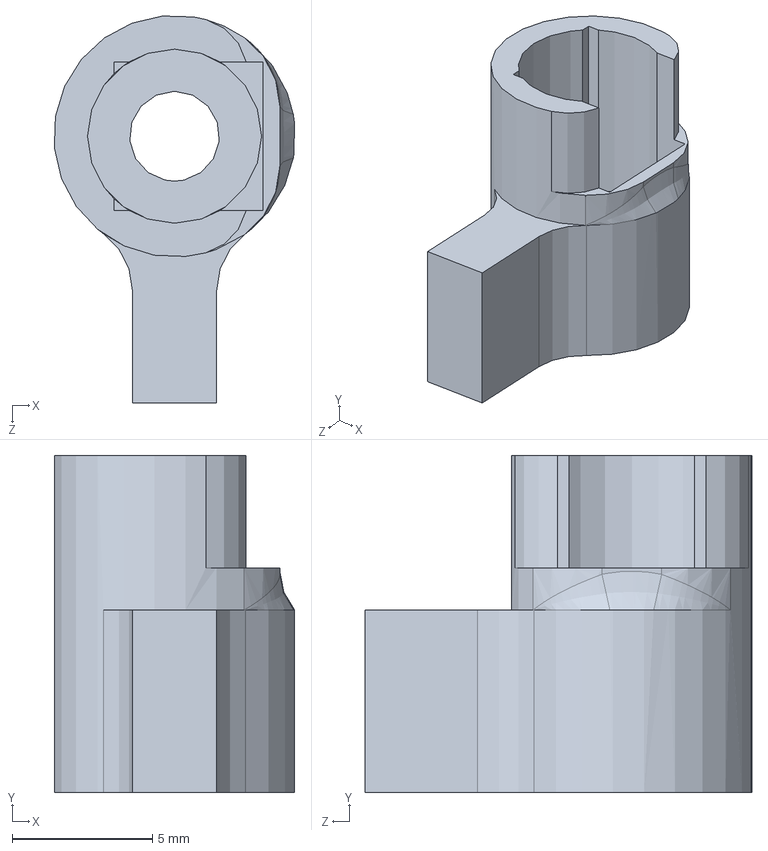
[picture p81: CAD file, 2018-08-11]
Mods/Peripherals/Collective levers/All levers/5x5 magnet holder mod/SLDPRT/single_collective_magnet_holder_5x5mm_socket_offset_single_collective7b.SLDPRT
8.56 x 12.0 x 13.8 mm
