hc625ma/simchair_models/Mods/Peripherals/Collective levers/All levers/Housing with a revision hatch mod/Pneumatic mod version/STL/pneumatic_mod_gimbal_housing_with_revision_hatch_pneumatic_mod14a.STL

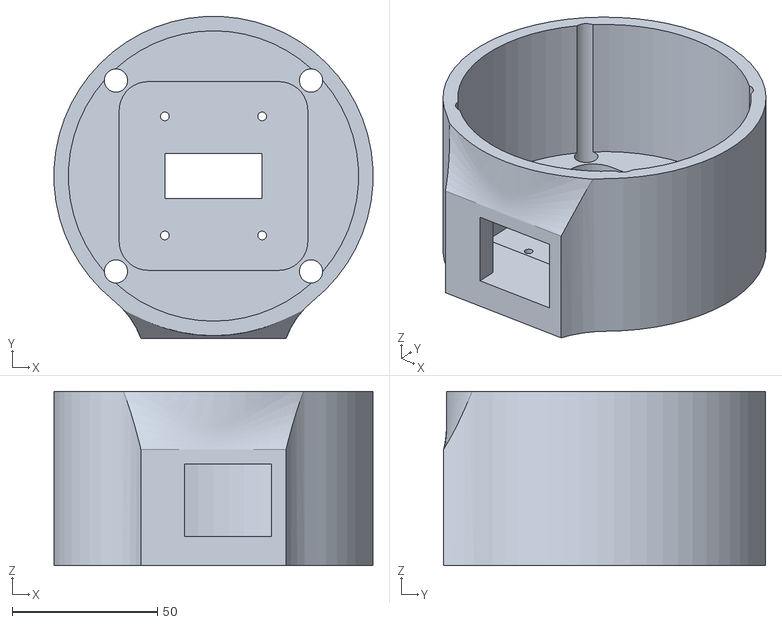
[picture p82: CAD file, 2019-02-21]
Mods/Peripherals/Collective levers/All levers/Housing with a revision hatch mod/Pneumatic mod version/STL/pneumatic_mod_gimbal_housing_with_revision_hatch_pneumatic_mod14a.STL
109.9 x 110.9 x 60.0
