hc625ma/simchair_models/Mods/Peripherals/Collective levers/All levers/Housing with a revision hatch mod/Rubber band version/SLDPRT/single_collective_enclosure_with_revision_hatch_single_collective01a.SLDPRT

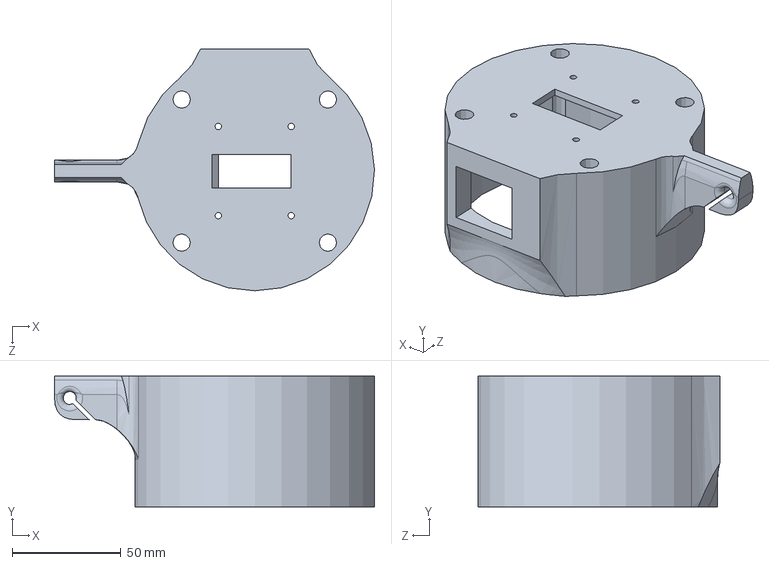
[picture p83: CAD file, 2019-02-24]
Mods/Peripherals/Collective levers/All levers/Housing with a revision hatch mod/Rubber band version/SLDPRT/single_collective_enclosure_with_revision_hatch_single_collective01a.SLDPRT
147.0 x 60.0 x 111.0 mm
