hc625ma/simchair_models/Mods/Peripherals/Collective levers/All levers/Housing with a revision hatch mod/Rubber band version/STL/single_collective_enclosure_with_revision_hatch_part_2_single_collective01b.STL

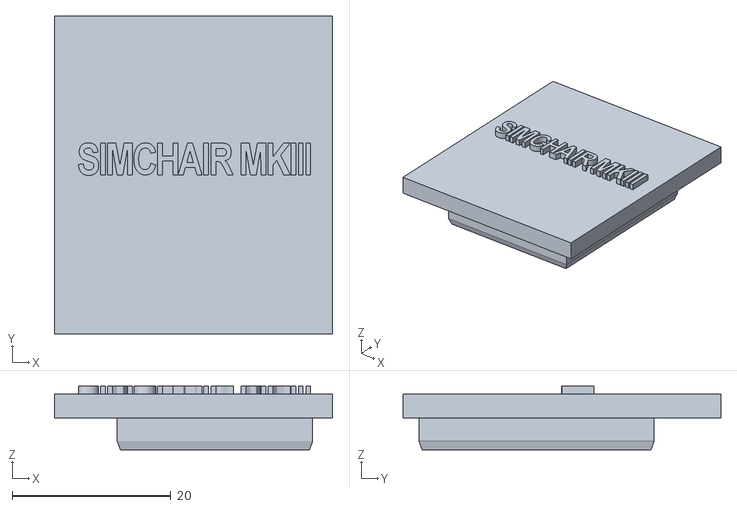
[picture p84: CAD file, 2019-02-21]
Mods/Peripherals/Collective levers/All levers/Housing with a revision hatch mod/Rubber band version/STL/single_collective_enclosure_with_revision_hatch_part_2_single_collective01b.STL
35.0 x 40.0 x 8.00
