hc625ma/simchair_models/Mods/Peripherals/Collective levers/All levers/Pneumatic actuator mod/SLDPRT/pneumatic_mod_enclosure_bottom_p1_8p8c_sockets_pneumatic_mod01a.SLDPRT

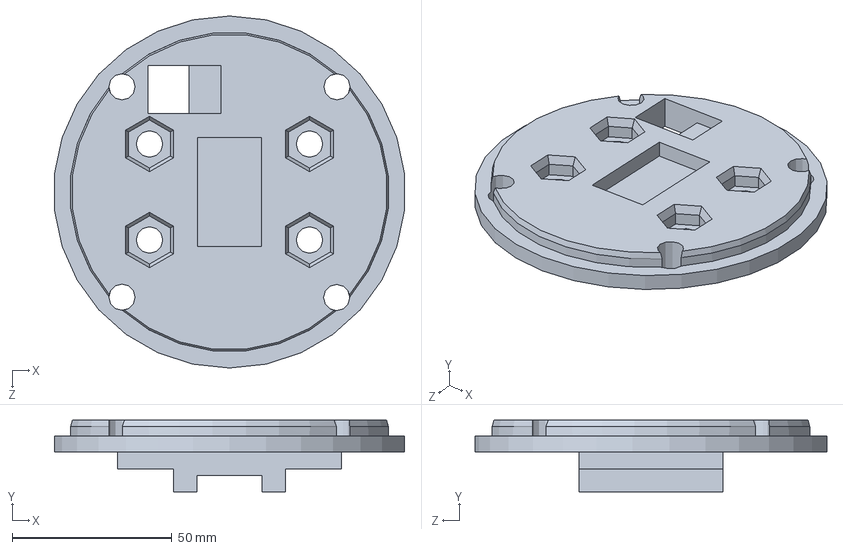
[picture p85: CAD file, 2019-06-21]
Mods/Peripherals/Collective levers/All levers/Pneumatic actuator mod/SLDPRT/pneumatic_mod_enclosure_bottom_p1_8p8c_sockets_pneumatic_mod01a.SLDPRT
109.4 x 22.5 x 110.0 mm
