hc625ma/simchair_models/Mods/Peripherals/Collective levers/Single engine collective/Mi-8 style throttle grip for physical throttle latch mod/SLDPRT/single_collective_throttle_grip_single_collective11b.SLDPRT

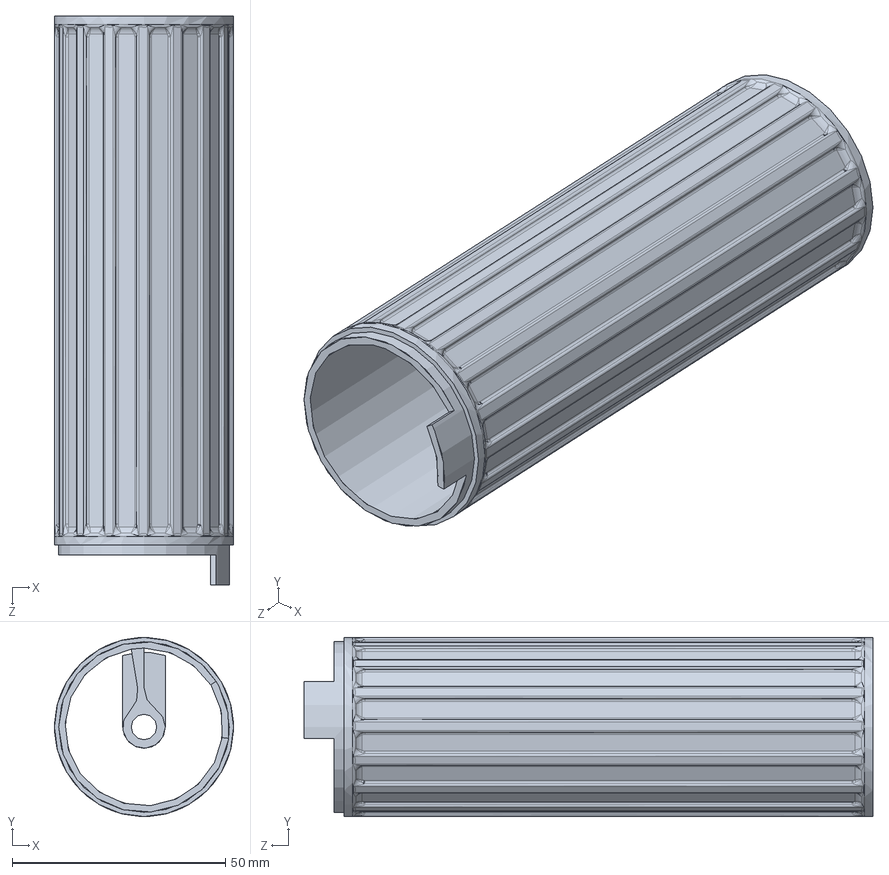
[picture p86: CAD file, 2019-05-10]
Mods/Peripherals/Collective levers/Single engine collective/Mi-8 style throttle grip for physical throttle latch mod/SLDPRT/single_collective_throttle_grip_single_collective11b.SLDPRT
42.0 x 42.0 x 133.4 mm
