hc625ma/simchair_models/Mods/Peripherals/Collective levers/Single engine collective/Physical throttle latch mod/SLDPRT/single_collective_throttle_frame_p2_single_collective10a.SLDPRT

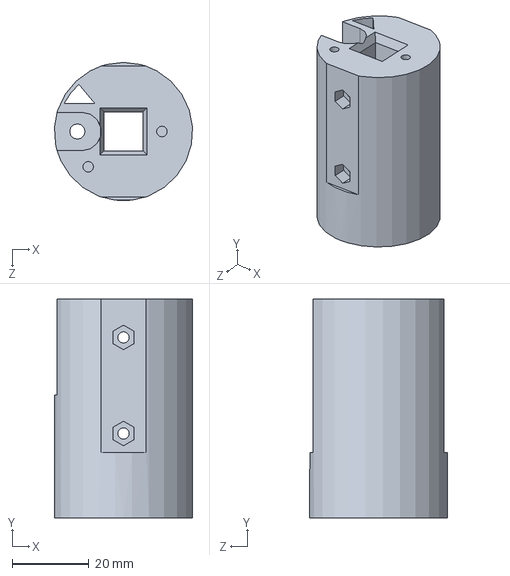
[picture p87: CAD file, 2019-05-10]
Mods/Peripherals/Collective levers/Single engine collective/Physical throttle latch mod/SLDPRT/single_collective_throttle_frame_p2_single_collective10a.SLDPRT
35.9 x 57.0 x 36.0 mm
