hc625ma/simchair_models/Mods/Peripherals/Collective levers/Single engine collective/Physical throttle latch mod/STL/single_collective_idle_stop_button_p3_single_collective16.STL

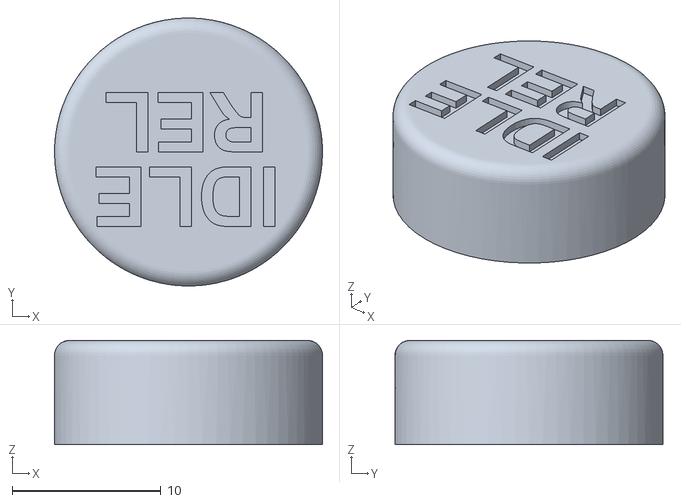
[picture p88: CAD file, 2019-02-26]
Mods/Peripherals/Collective levers/Single engine collective/Physical throttle latch mod/STL/single_collective_idle_stop_button_p3_single_collective16.STL
18.0 x 18.0 x 7.00
