hc625ma/simchair_models/Mods/Peripherals/Helicopter pedals/SLDPRT/pedals_magnet_holder_5x5x5mm_pedals12a.SLDPRT

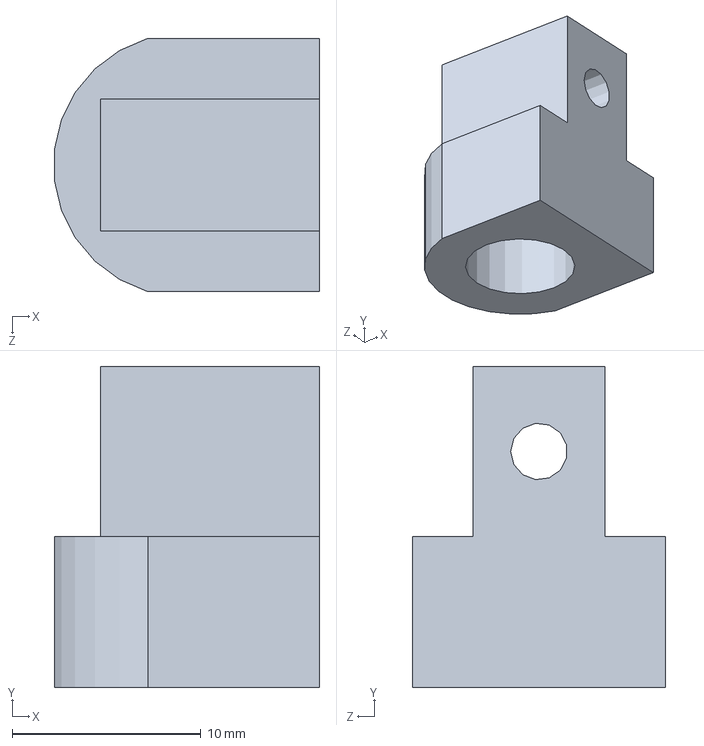
[picture p90: CAD file, 2018-12-16]
Mods/Peripherals/Helicopter pedals/SLDPRT/pedals_magnet_holder_5x5x5mm_pedals12a.SLDPRT
14.1 x 17.0 x 13.4 mm
