hc625ma/simchair_models/Components/Frames/40mm construction profile frame/Collective mount/40mm_profile_bracket_p3.SLDPRT

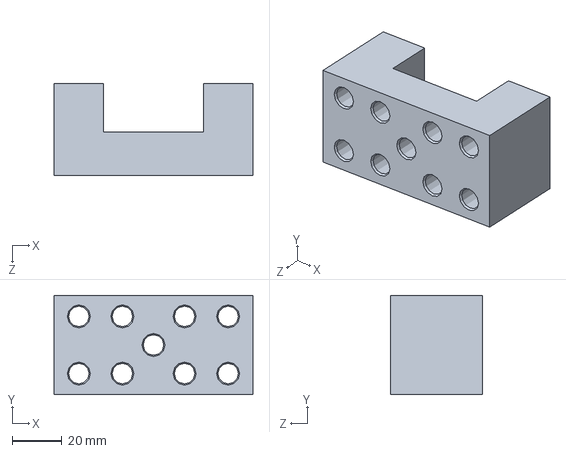
[picture p91: CAD file, 2019-05-31]
Components/Frames/40mm construction profile frame/Collective mount/40mm_profile_bracket_p3.SLDPRT
80.0 x 40.0 x 37.0 mm
