hc625ma/simchair_models/Components/Frames/Generic Chair with vertical round legs/SLDPRT/generic_chair_frame_collective_mount_horizontal_left_generic_chair02.SLDPRT

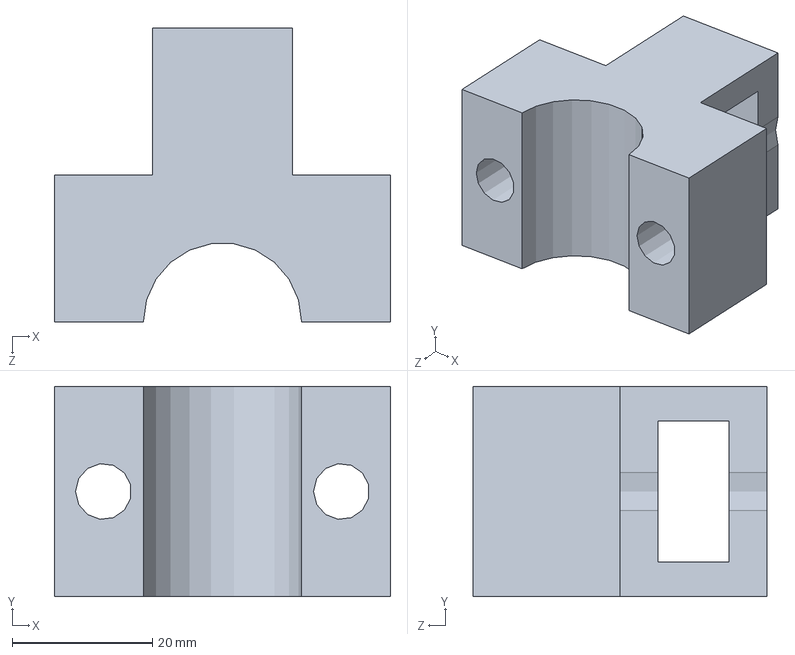
[picture p92: CAD file, 2018-10-19]
Components/Frames/Generic Chair with vertical round legs/SLDPRT/generic_chair_frame_collective_mount_horizontal_left_generic_chair02.SLDPRT
48.0 x 30.0 x 42.0 mm
