hc625ma/simchair_models/Components/Frames/IKEA GUNDE frame/Chair mounts/SLDPRT/ikea_gunde_frame_throttle_quadrant_frame_mount_p2_ikea_gunde_frame08.SLDPRT

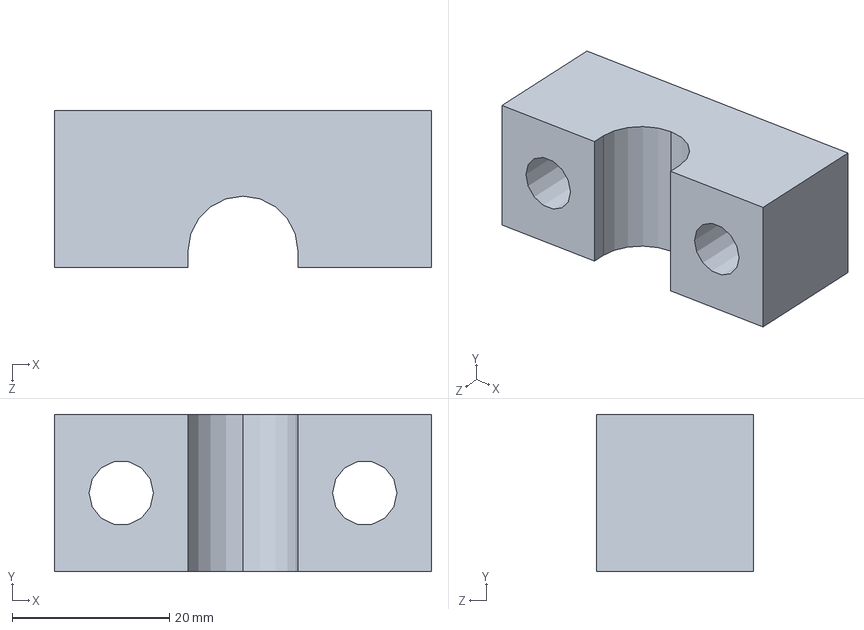
[picture p93: CAD file, 2018-10-25]
Components/Frames/IKEA GUNDE frame/Chair mounts/SLDPRT/ikea_gunde_frame_throttle_quadrant_frame_mount_p2_ikea_gunde_frame08.SLDPRT
48.0 x 20.0 x 20.0 mm
