hc625ma/simchair_models/Components/Frames/IKEA GUNDE frame/Chair mounts/STL/ikea_gunde_frame_plate.stl

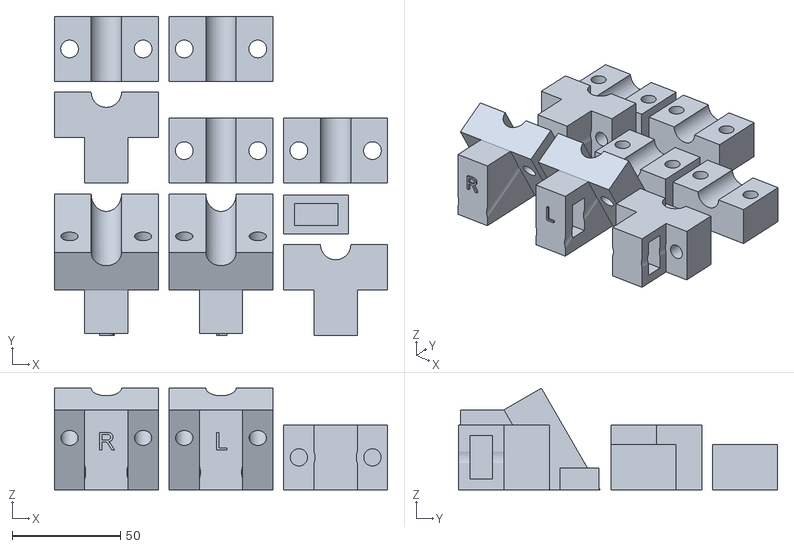
[picture p94: CAD file, 2018-08-11]
Components/Frames/IKEA GUNDE frame/Chair mounts/STL/ikea_gunde_frame_plate.stl
154.0 x 147.4 x 47.0
