hc625ma/simchair_models/Components/Frames/IKEA GUNDE frame/Cyclic stick frame parts/Non-spring-loaded stick/SLDPRT/gunde_cyclic_frame_gimbal_connector_pvc_3_4_inch_gunde_cyclic_frame01b.SLDPRT

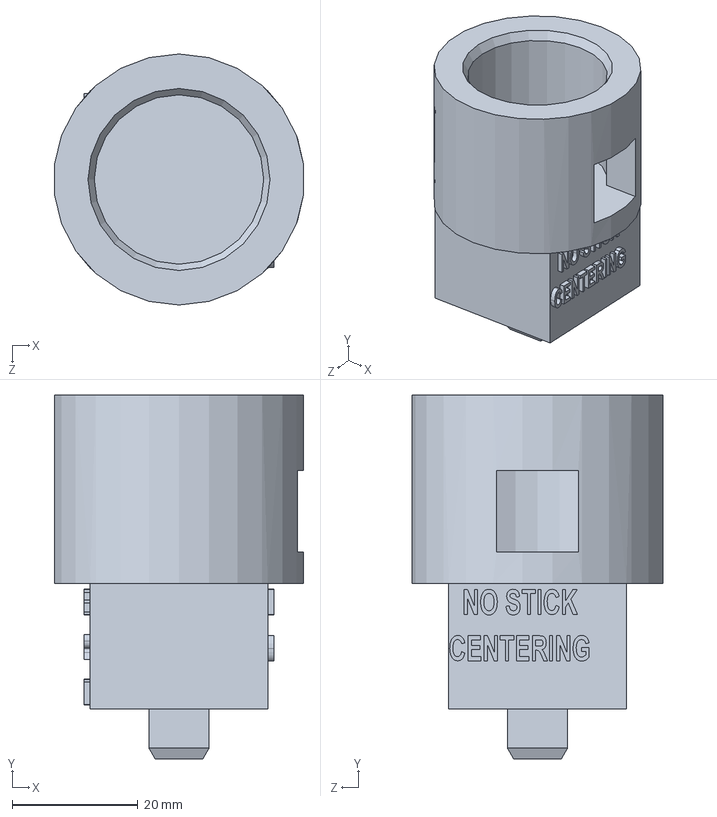
[picture p95: CAD file, 2019-02-21]
Components/Frames/IKEA GUNDE frame/Cyclic stick frame parts/Non-spring-loaded stick/SLDPRT/gunde_cyclic_frame_gimbal_connector_pvc_3_4_inch_gunde_cyclic_frame01b.SLDPRT
39.7 x 58.0 x 40.0 mm
