hc625ma/simchair_models/Components/Frames/IKEA GUNDE frame/Cyclic stick frame parts/Spring-loaded stick/SLDPRT/spring_loaded_cyclic_frame_stick_grip_connector_spring_loaded_cyclic_frame03.SLDPRT

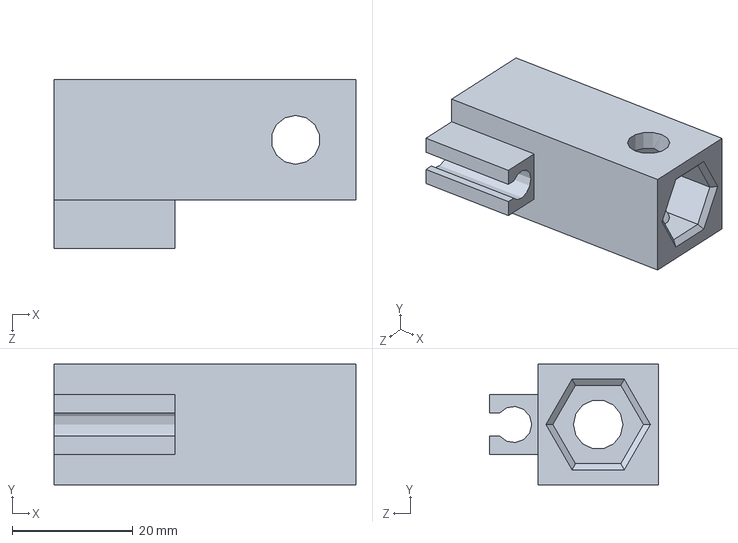
[picture p96: CAD file, 2018-12-24]
Components/Frames/IKEA GUNDE frame/Cyclic stick frame parts/Spring-loaded stick/SLDPRT/spring_loaded_cyclic_frame_stick_grip_connector_spring_loaded_cyclic_frame03.SLDPRT
50.0 x 20.0 x 28.0 mm
