hc625ma/simchair_models/Components/Peripherals/AB412 collective head/STL/ab412_head_enclosure_p2_ab412_head02.STL

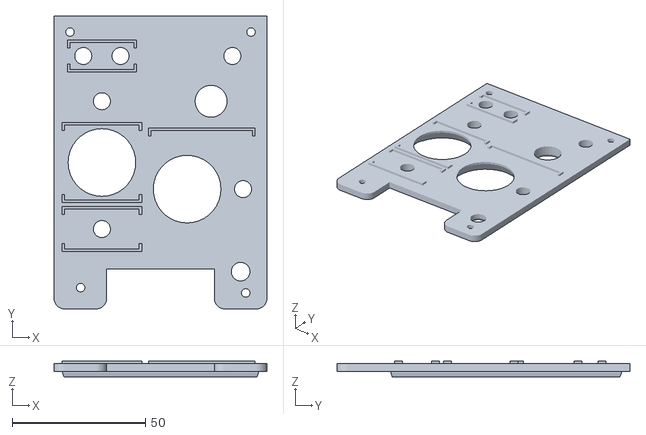
[picture p97: CAD file, 2018-08-11]
Components/Peripherals/AB412 collective head/STL/ab412_head_enclosure_p2_ab412_head02.STL
80.0 x 110.0 x 6.00
