hc625ma/simchair_models/Components/Peripherals/B8 flight stick/STL/b8stick_right_half_b8stick01.STL

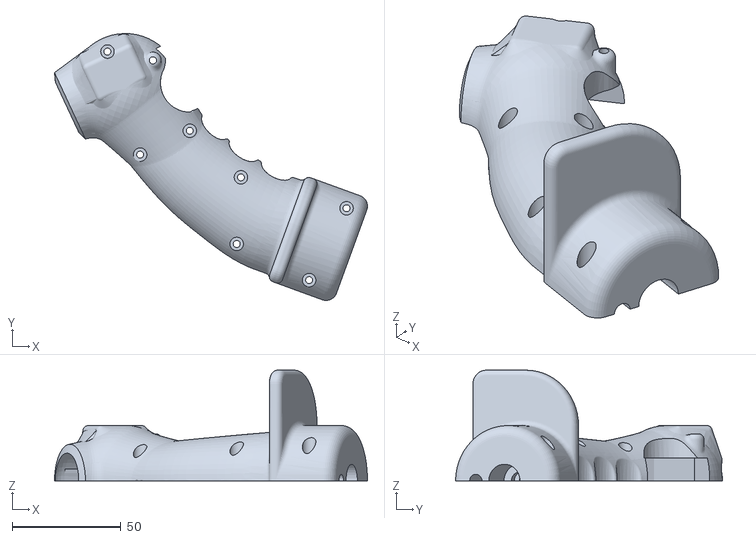
[picture p98: CAD file, 2018-08-11]
Components/Peripherals/B8 flight stick/STL/b8stick_right_half_b8stick01.STL
143.6 x 122.5 x 50.8
