hc625ma/simchair_models/Components/Peripherals/dev/Flight stick gimbal 608zz CJMCU-93/Assembly1/gimbal_cjmcu_frame_gimbal05c_10mm.SLDPRT

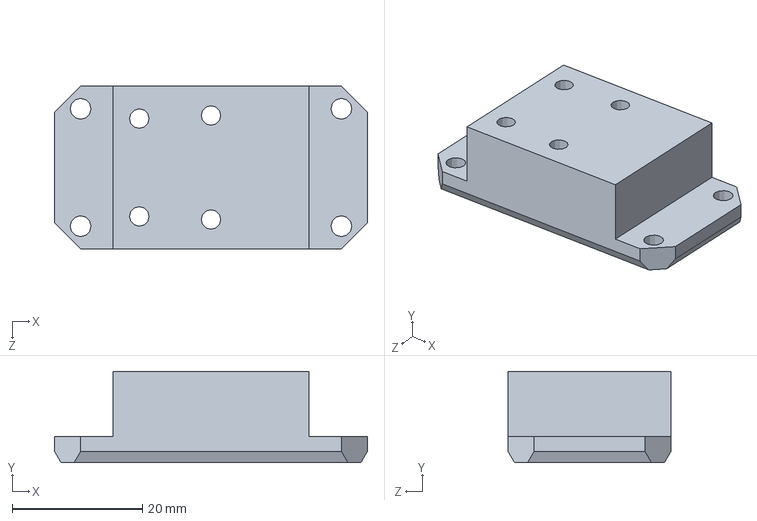
[picture p99: CAD file, 2018-10-22]
Components/Peripherals/dev/Flight stick gimbal 608zz CJMCU-93/Assembly1/gimbal_cjmcu_frame_gimbal05c_10mm.SLDPRT
48.0 x 14.0 x 25.0 mm
