hc625ma/simchair_models/Components/Peripherals/dev/Flight stick gimbal 608zz CJMCU-93/New folder1/gimbal_outer_bracket_half.SLDPRT

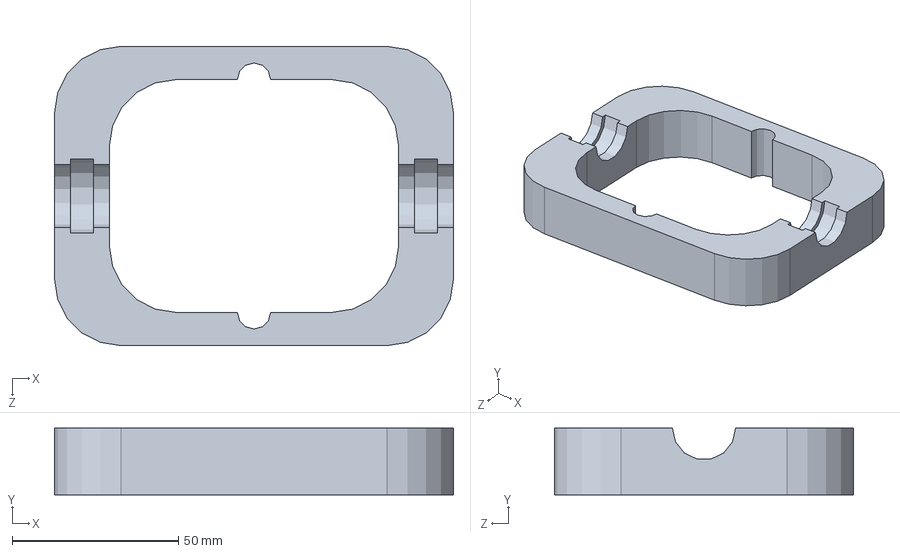
[picture p100: CAD file, 2018-10-22]
Components/Peripherals/dev/Flight stick gimbal 608zz CJMCU-93/New folder1/gimbal_outer_bracket_half.SLDPRT
120.0 x 20.0 x 90.0 mm
