hc625ma/simchair_models/Components/Peripherals/dev/Flight stick gimbal 608zz reinforced v2/SLDPRT/gimbal_inner_ring_top_gimbal06.SLDPRT

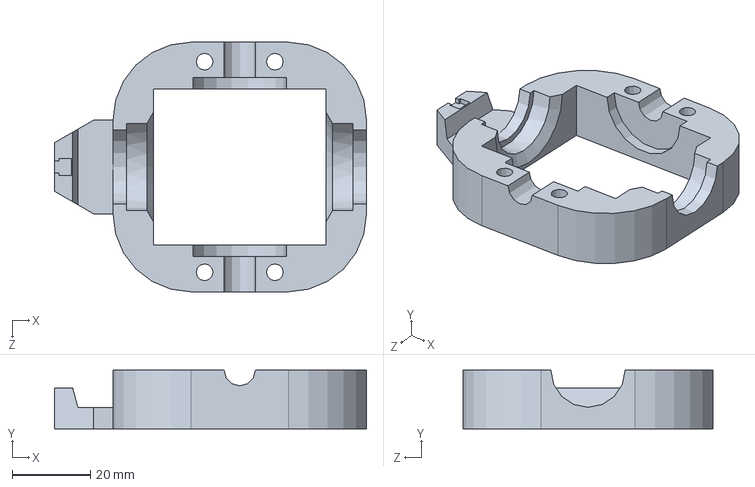
[picture p101: CAD file, 2019-05-10]
Components/Peripherals/dev/Flight stick gimbal 608zz reinforced v2/SLDPRT/gimbal_inner_ring_top_gimbal06.SLDPRT
80.0 x 15.0 x 64.0 mm
