hc625ma/simchair_models/Components/Peripherals/dev/Flight stick gimbal GE25 ES-2RS/SLDPRT/gimbal_housing_gimbal01.SLDPRT

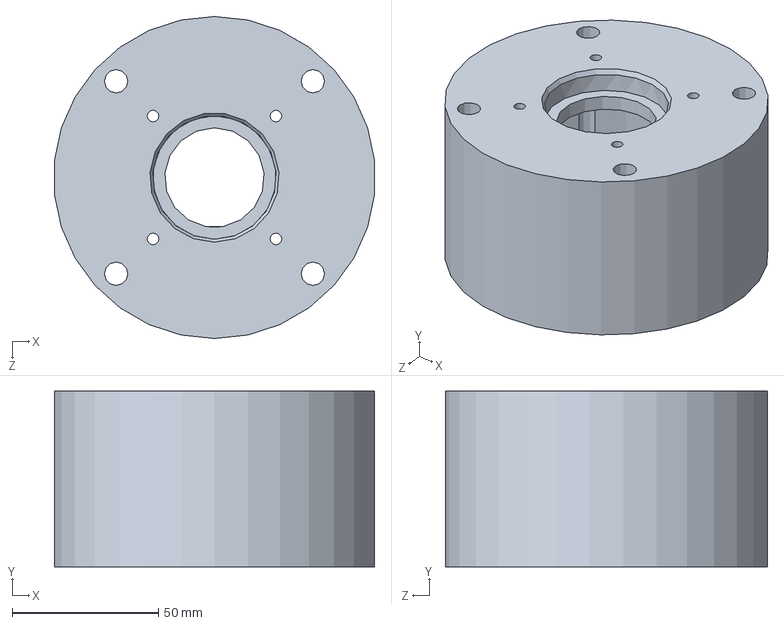
[picture p102: CAD file, 2018-10-22]
Components/Peripherals/dev/Flight stick gimbal GE25 ES-2RS/SLDPRT/gimbal_housing_gimbal01.SLDPRT
109.4 x 60.0 x 110.0 mm
