hc625ma/simchair_models/Components/Peripherals/dev/Helicopter throttle quadrant/SLDPRT/throttle_quadrant_axis_module_slider_throttle_quadrant02b.SLDPRT

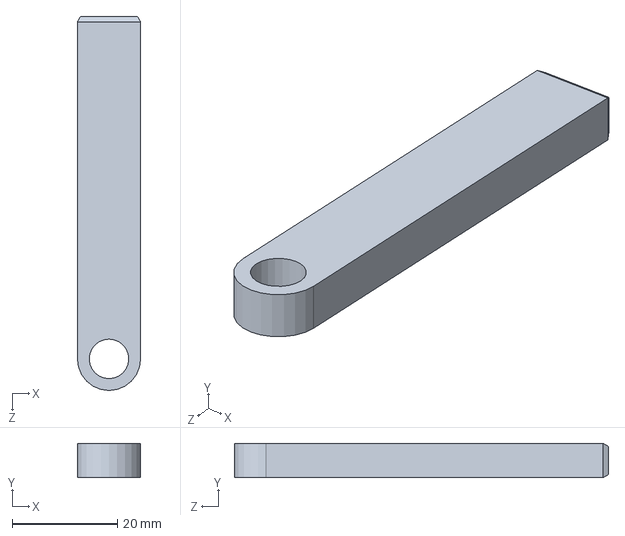
[picture p103: CAD file, 2019-05-10]
Components/Peripherals/dev/Helicopter throttle quadrant/SLDPRT/throttle_quadrant_axis_module_slider_throttle_quadrant02b.SLDPRT
12.0 x 6.50 x 71.0 mm
