hc625ma/simchair_models/Components/Peripherals/dev/Simple collective/SLDPRT/collective_frame_4,5x42mm.SLDPRT

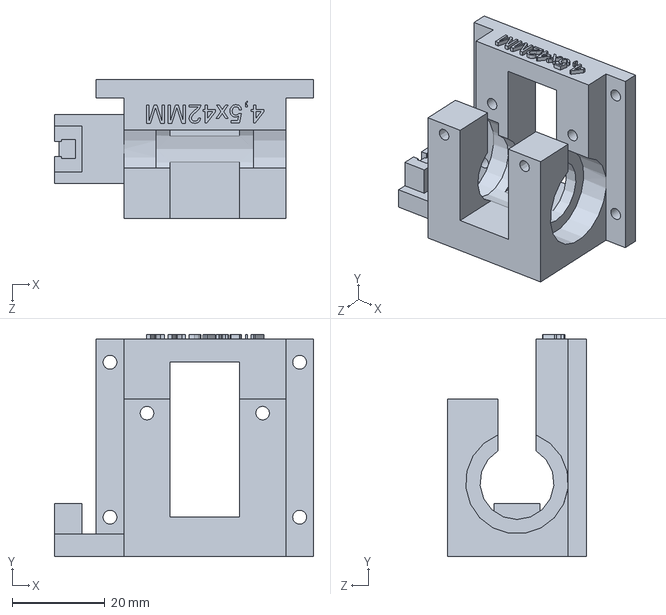
[picture p104: CAD file, 2019-02-21]
Components/Peripherals/dev/Simple collective/SLDPRT/collective_frame_4,5x42mm.SLDPRT
56.0 x 48.0 x 30.0 mm
