hc625ma/simchair_models/Components/Peripherals/dev/Simple collective/STL/chair_mount_150_degrees_collective_frame_pla.stl

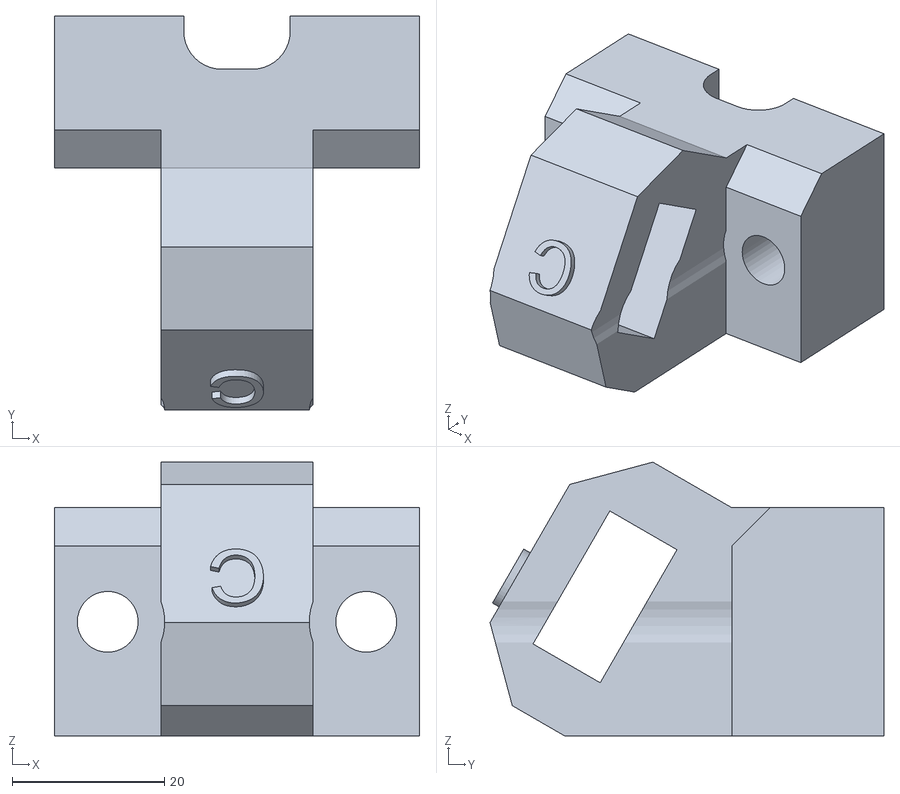
[picture p105: CAD file, 2019-02-21]
Components/Peripherals/dev/Simple collective/STL/chair_mount_150_degrees_collective_frame_pla.stl
48.0 x 51.8 x 36.0
