hc625ma/simchair_models/Components/Peripherals/Flight stick gimbal 608zz light/SLDPRT/gimbal_enclosure_gimbal01.SLDPRT

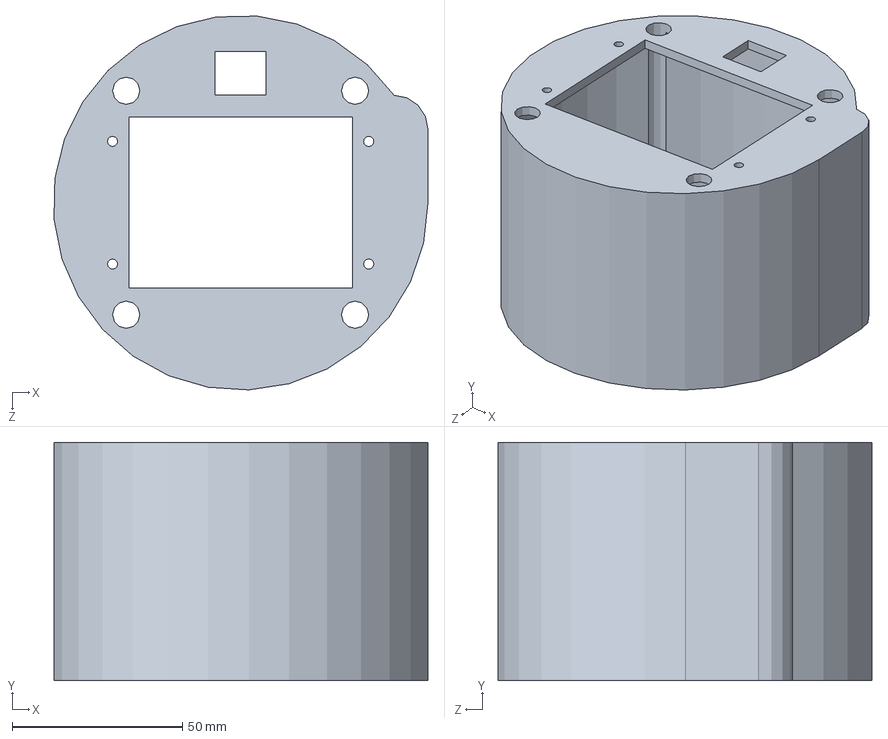
[picture p106: CAD file, 2018-10-19]
Components/Peripherals/Flight stick gimbal 608zz light/SLDPRT/gimbal_enclosure_gimbal01.SLDPRT
109.8 x 70.0 x 109.7 mm
