hc625ma/simchair_models/Components/Peripherals/Flight stick gimbal 608zz reinforced/STL/gimbal_housing_gimbal01.STL

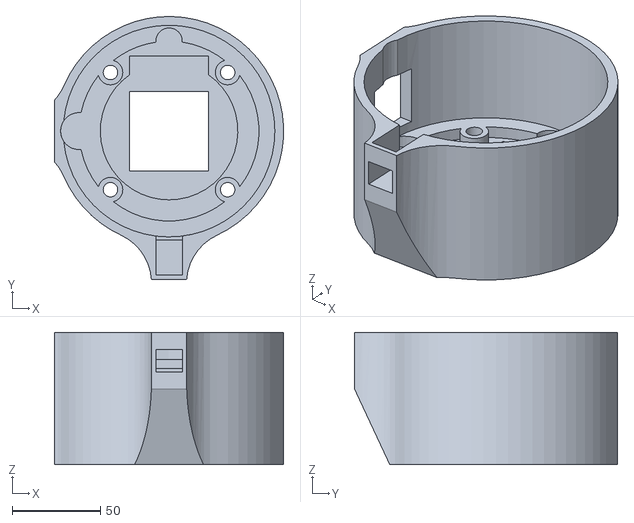
[picture p107: CAD file, 2019-03-17]
Components/Peripherals/Flight stick gimbal 608zz reinforced/STL/gimbal_housing_gimbal01.STL
129.9 x 149.1 x 75.0
