hc625ma/simchair_models/Components/Peripherals/Helicopter pedals/SLDPRT/pedals_pedal_mount_left_pedals04.SLDPRT

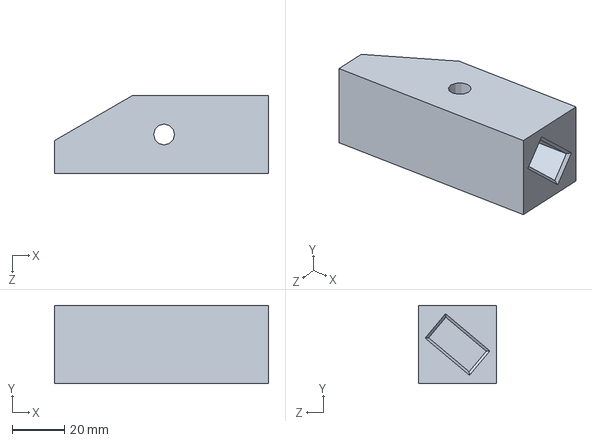
[picture p108: CAD file, 2019-04-12]
Components/Peripherals/Helicopter pedals/SLDPRT/pedals_pedal_mount_left_pedals04.SLDPRT
82.0 x 30.0 x 30.0 mm
