hc625ma/simchair_models/Components/Peripherals/Huey collective head/STL/huey_head_enclosure_p2_huey_head02.STL

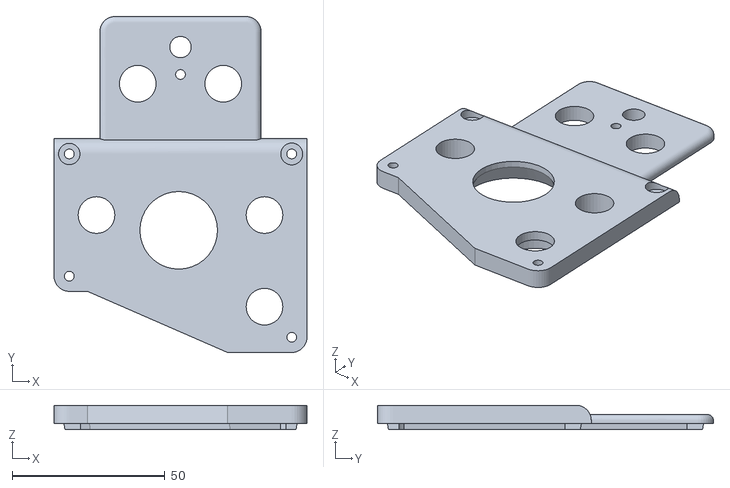
[picture p109: CAD file, 2018-08-11]
Components/Peripherals/Huey collective head/STL/huey_head_enclosure_p2_huey_head02.STL
82.8 x 110.0 x 8.00
