hc625ma/simchair_models/Components/Peripherals/Single engine GA controls/SLDPRT/single_eng_ga_controls_prop_single_eng_ga_controls04.SLDPRT

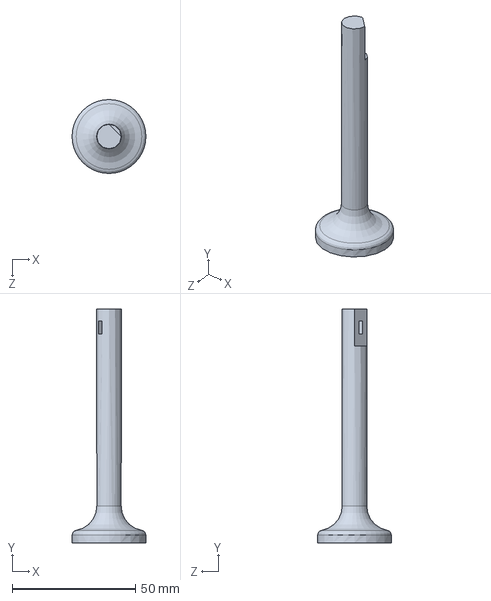
[picture p110: CAD file, 2018-08-11]
Components/Peripherals/Single engine GA controls/SLDPRT/single_eng_ga_controls_prop_single_eng_ga_controls04.SLDPRT
30.0 x 95.0 x 30.0 mm
