hc625ma/simchair_models/Components/Peripherals/Twin collective/SLDPRT/twin_collective_head_i2c_connector_housing_twin_collective15.SLDPRT

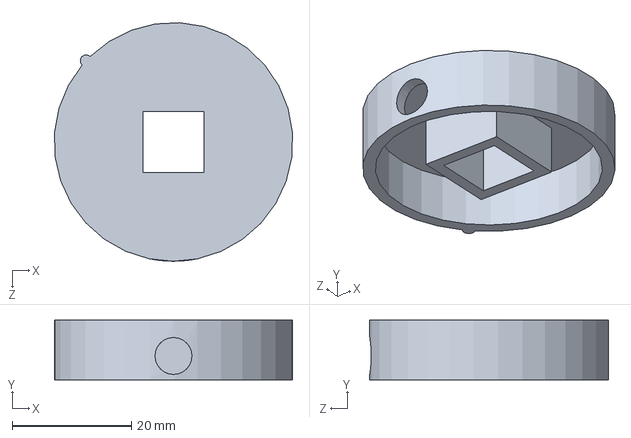
[picture p111: CAD file, 2018-08-24]
Components/Peripherals/Twin collective/SLDPRT/twin_collective_head_i2c_connector_housing_twin_collective15.SLDPRT
39.9 x 10.0 x 40.0 mm
