hc625ma/simchair_models/Components/Peripherals/Twin collective/STL/twin_collective_enclosure_bottom_p1_twin_collective02.STL

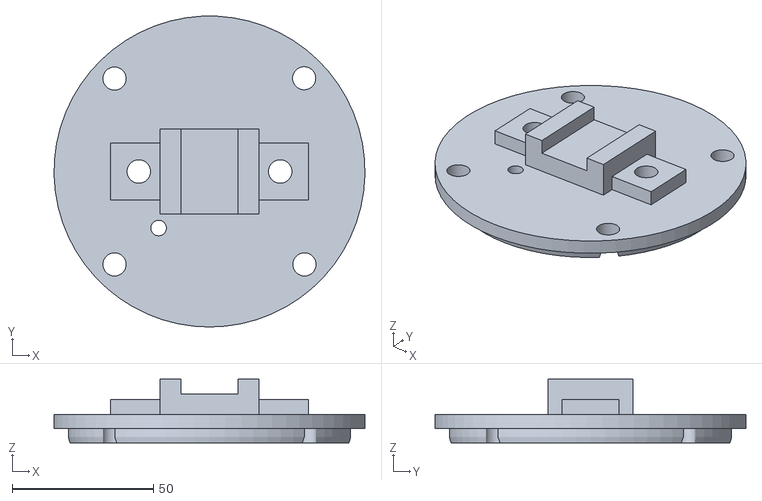
[picture p112: CAD file, 2018-08-11]
Components/Peripherals/Twin collective/STL/twin_collective_enclosure_bottom_p1_twin_collective02.STL
110.0 x 110.0 x 22.5
