hc625ma/simchair_models/Hardware Models/GE25 ES-2RS/inner_ring.SLDPRT

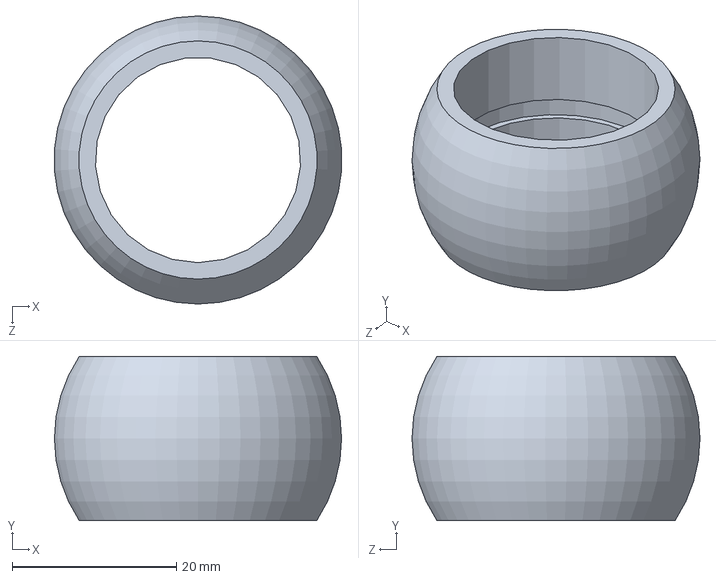
[picture p113: CAD file, 2018-10-19]
Hardware Models/GE25 ES-2RS/inner_ring.SLDPRT
35.0 x 20.0 x 35.1 mm
