hc625ma/simchair_models/Hardware Models/Magnets/6x4.8mm cylindrical magnet.SLDPRT

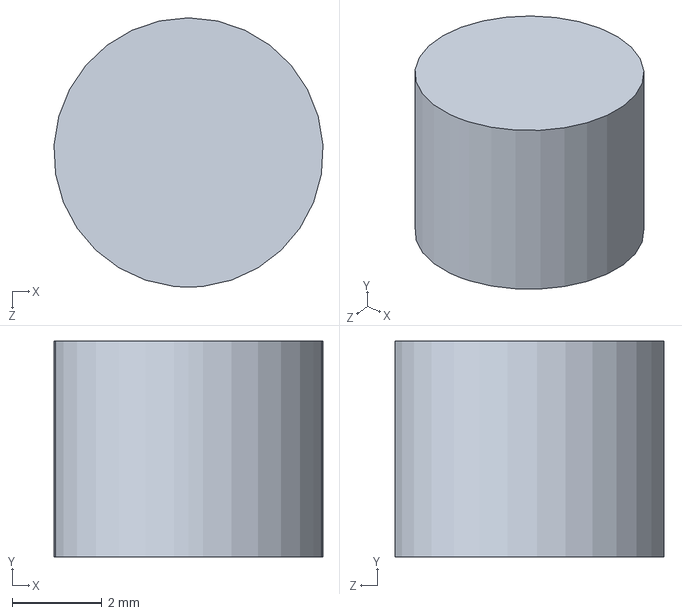
[picture p114: CAD file, 2018-10-19]
Hardware Models/Magnets/6x4.8mm cylindrical magnet.SLDPRT
5.99 x 4.80 x 6.00 mm
