hc625ma/simchair_models/Mods/Frames/IKEA GUNDE frame/Chair mounts, increased clearance/SLDPRT/ikea_gunde_frame_0.4mm_collective_frame_mount_right_150_deg_ikea_gunde_frame03a.SLDPRT

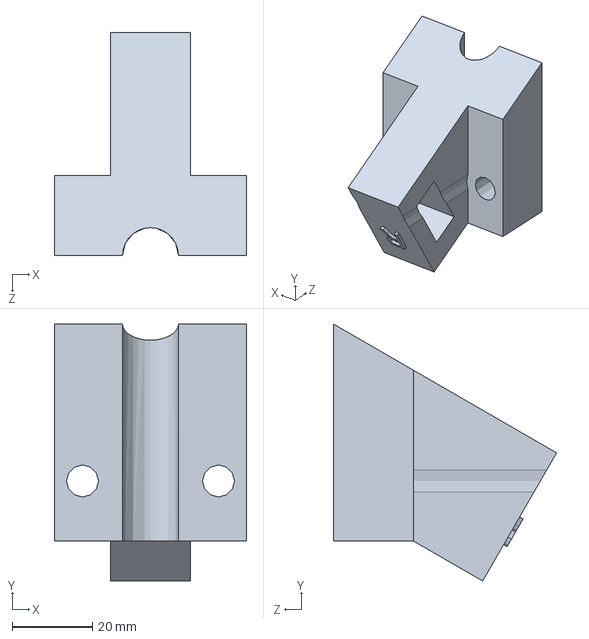
[picture p115: CAD file, 2019-02-06]
Mods/Frames/IKEA GUNDE frame/Chair mounts, increased clearance/SLDPRT/ikea_gunde_frame_0.4mm_collective_frame_mount_right_150_deg_ikea_gunde_frame03a.SLDPRT
48.0 x 64.2 x 55.8 mm
