hc625ma/simchair_models/Mods/Peripherals/AB412 collective head/Other/SLDPRT/ab412_head_enclosure_front_cover_p2_radio_panel_ready_ab412_head06.SLDPRT

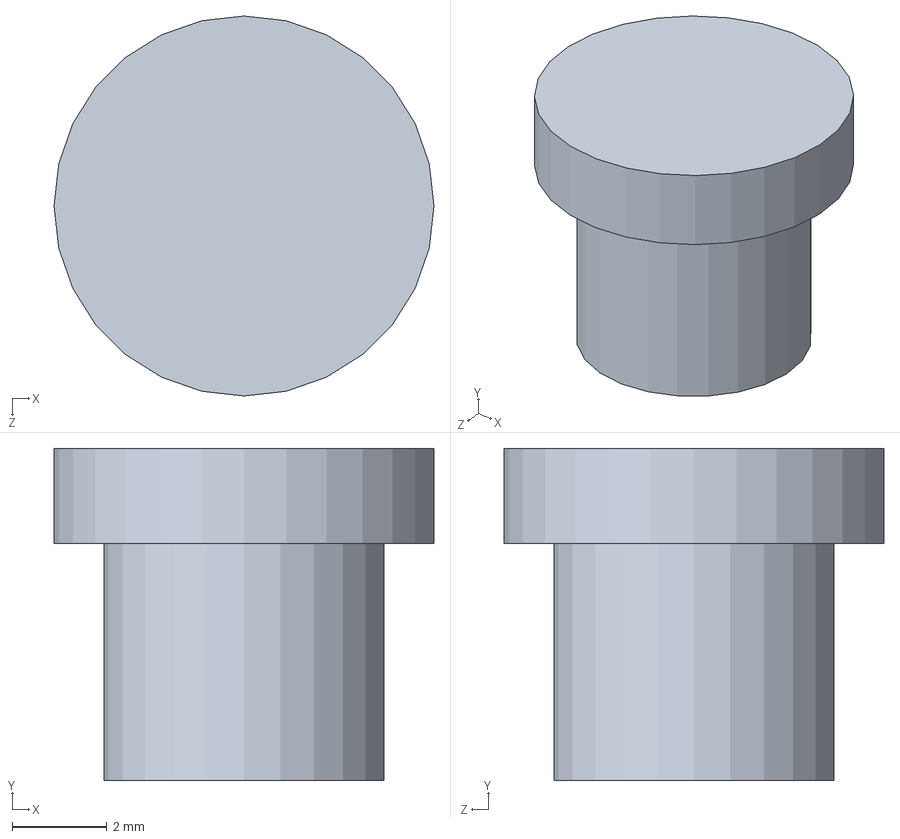
[picture p116: CAD file, 2019-04-12]
Mods/Peripherals/AB412 collective head/Other/SLDPRT/ab412_head_enclosure_front_cover_p2_radio_panel_ready_ab412_head06.SLDPRT
8.00 x 7.00 x 8.00 mm
