hc625ma/simchair_models/Mods/Peripherals/AB412 collective head/VR MAX radio+ panel mod/STL/ab412_head_radio_panel_housing_p2_ab412_head_radio_panel02.STL

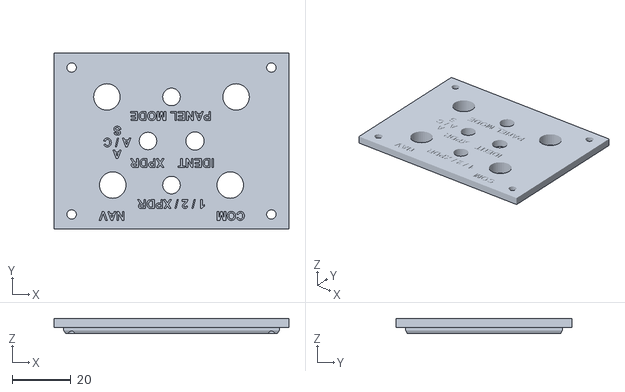
[picture p117: CAD file, 2019-03-19]
Mods/Peripherals/AB412 collective head/VR MAX radio+ panel mod/STL/ab412_head_radio_panel_housing_p2_ab412_head_radio_panel02.STL
80.0 x 60.0 x 5.00
