hc625ma/simchair_models/Mods/Peripherals/Collective levers/All levers/Pneumatic actuator mod/SLDPRT/Assembly/pneumatic_mod_counterweight_housing_p2_pneumatic_mod12.SLDPRT

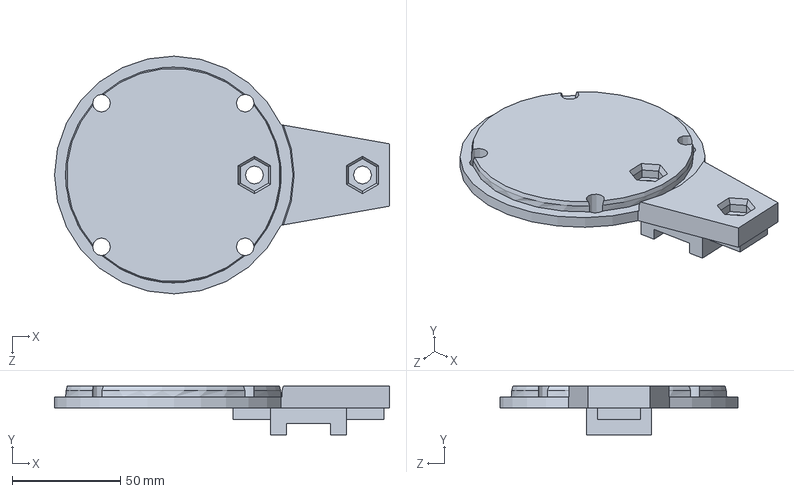
[picture p118: CAD file, 2018-10-23]
Mods/Peripherals/Collective levers/All levers/Pneumatic actuator mod/SLDPRT/Assembly/pneumatic_mod_counterweight_housing_p2_pneumatic_mod12.SLDPRT
155.0 x 22.5 x 110.0 mm
