hc625ma/simchair_models/Mods/Peripherals/Collective levers/All levers/Pneumatic actuator mod/SLDPRT/pneumatic_mod_MAL-16-150_lever_detent_ring_pneumatic_mod07.SLDPRT

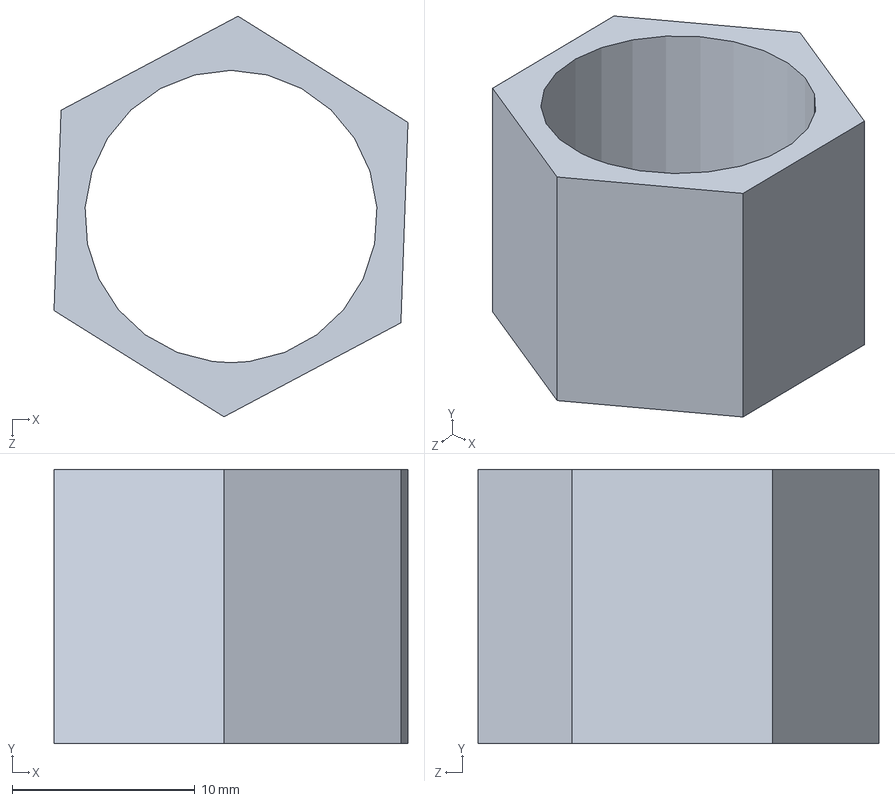
[picture p119: CAD file, 2019-04-12]
Mods/Peripherals/Collective levers/All levers/Pneumatic actuator mod/SLDPRT/pneumatic_mod_MAL-16-150_lever_detent_ring_pneumatic_mod07.SLDPRT
19.4 x 15.0 x 21.9 mm
