hc625ma/simchair_models/Mods/Peripherals/Collective levers/Single engine collective/Physical throttle latch mod/SLDPRT/single_collective_idle_stop_button_p1_single_collective14.SLDPRT

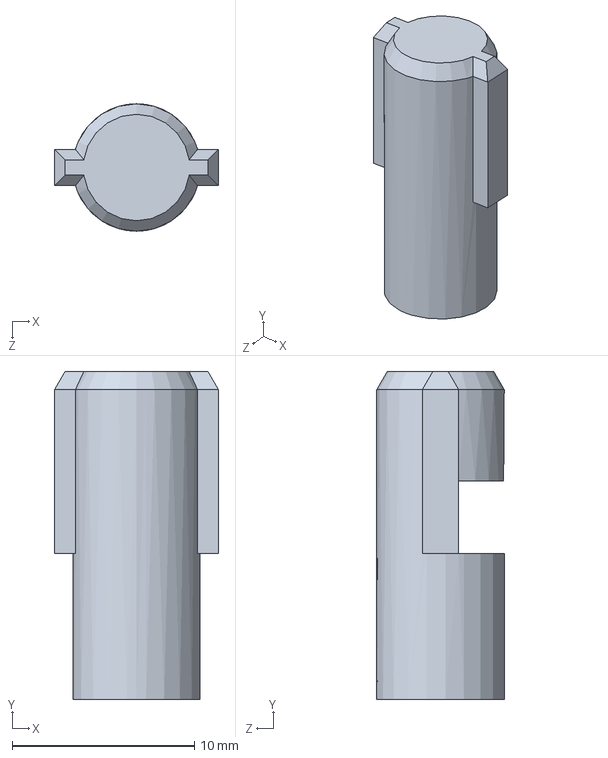
[picture p120: CAD file, 2019-04-12]
Mods/Peripherals/Collective levers/Single engine collective/Physical throttle latch mod/SLDPRT/single_collective_idle_stop_button_p1_single_collective14.SLDPRT
9.00 x 18.0 x 7.00 mm
