hc625ma/simchair_models/Mods/Peripherals/Flight stick gimbal 608zz reinforced/SLDPRT/gimbal_5x5x3mm_x2pcs_magnet_holder_incr_clearance_gimbal12c.SLDPRT

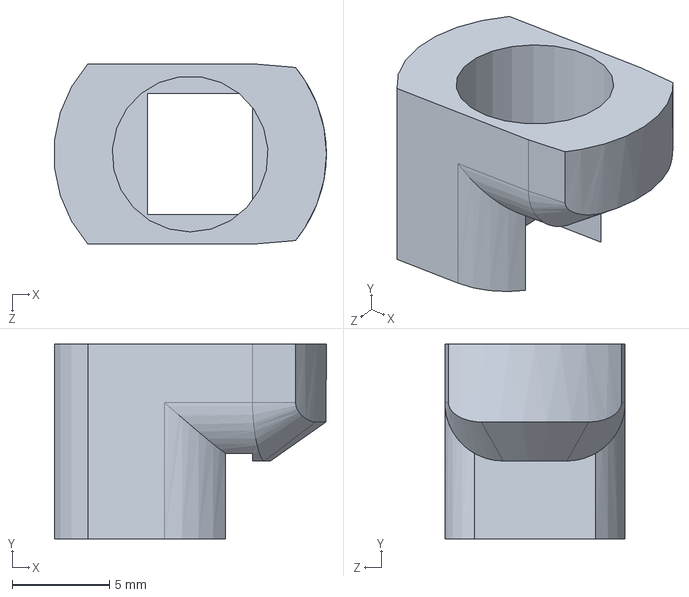
[picture p121: CAD file, 2019-03-17]
Mods/Peripherals/Flight stick gimbal 608zz reinforced/SLDPRT/gimbal_5x5x3mm_x2pcs_magnet_holder_incr_clearance_gimbal12c.SLDPRT
14.0 x 10.0 x 9.26 mm
