hc625ma/simchair_models/Components/Controllers/Simchair MKIII I2C controller/SLDPRT/controller_frame_mount_p1_controller03.SLDPRT

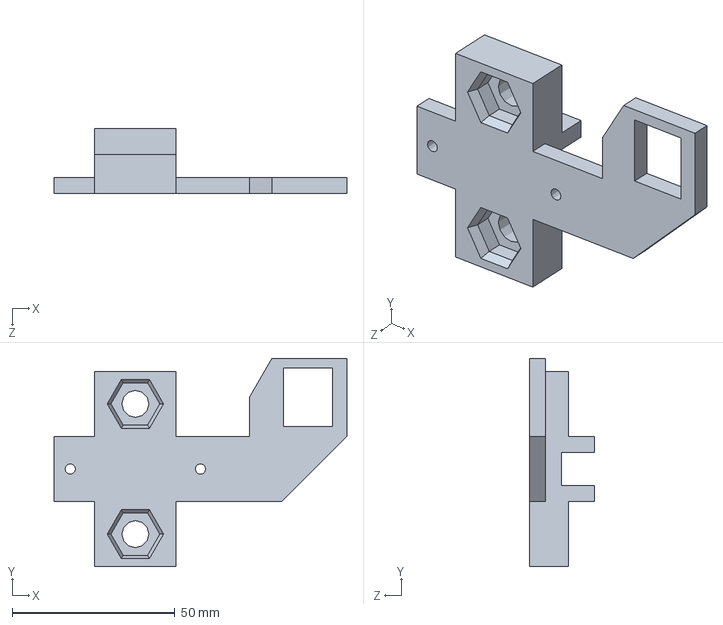
[picture p122: CAD file, 2018-08-11]
Components/Controllers/Simchair MKIII I2C controller/SLDPRT/controller_frame_mount_p1_controller03.SLDPRT
90.0 x 64.0 x 20.0 mm
