hc625ma/simchair_models/Components/Frames/IKEA GUNDE frame/Cyclic stick frame parts/Non-spring-loaded stick/SLDPRT/gunde_cyclic_frame_stick_grip_connector_pvc_1_inch_incr_clearance_gunde_cyclic_frame04b.SLDPRT

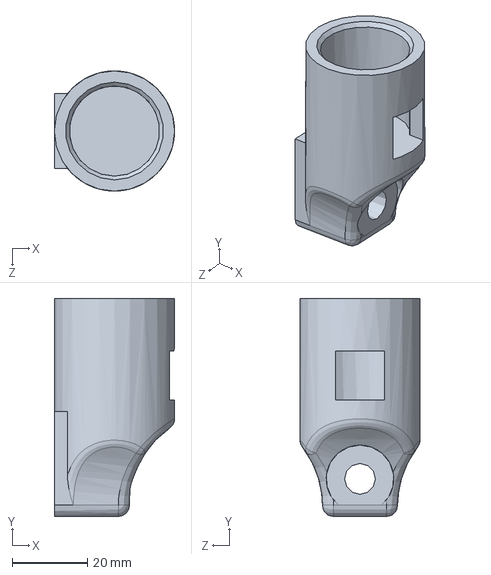
[picture p123: CAD file, 2019-02-06]
Components/Frames/IKEA GUNDE frame/Cyclic stick frame parts/Non-spring-loaded stick/SLDPRT/gunde_cyclic_frame_stick_grip_connector_pvc_1_inch_incr_clearance_gunde_cyclic_frame04b.SLDPRT
32.0 x 58.0 x 32.0 mm
