hc625ma/simchair_models/Components/Frames/IKEA GUNDE frame/Cyclic stick frame parts/Spring-loaded stick/SLDPRT/spring_loaded_cyclic_frame_stick_connector_90_deg_spring_loaded_cyclic_frame02.SLDPRT

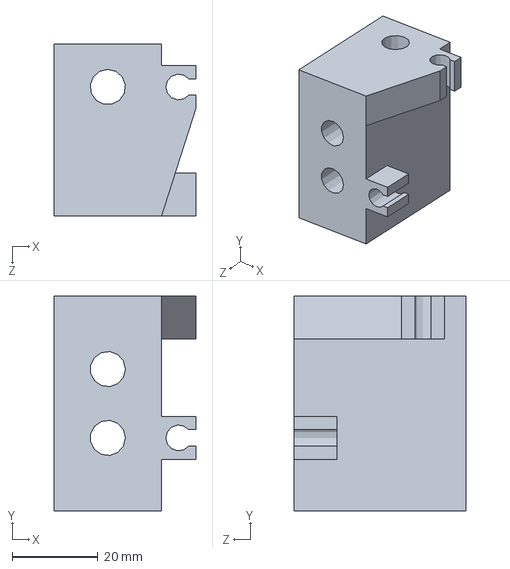
[picture p124: CAD file, 2018-12-24]
Components/Frames/IKEA GUNDE frame/Cyclic stick frame parts/Spring-loaded stick/SLDPRT/spring_loaded_cyclic_frame_stick_connector_90_deg_spring_loaded_cyclic_frame02.SLDPRT
33.0 x 50.0 x 40.0 mm
