hc625ma/simchair_models/Components/Peripherals/AB412 collective head/STL/ab412_head_pot_frame_ab412_head03.STL

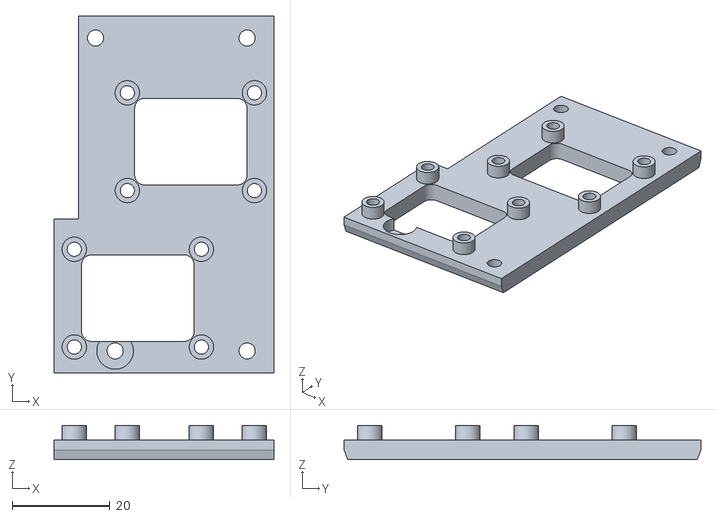
[picture p125: CAD file, 2018-08-11]
Components/Peripherals/AB412 collective head/STL/ab412_head_pot_frame_ab412_head03.STL
45.0 x 73.0 x 7.00
