hc625ma/simchair_models/Components/Peripherals/B8 flight stick/SLDPRT/b8stick_right_half_no_holes_b8stick01.SLDPRT

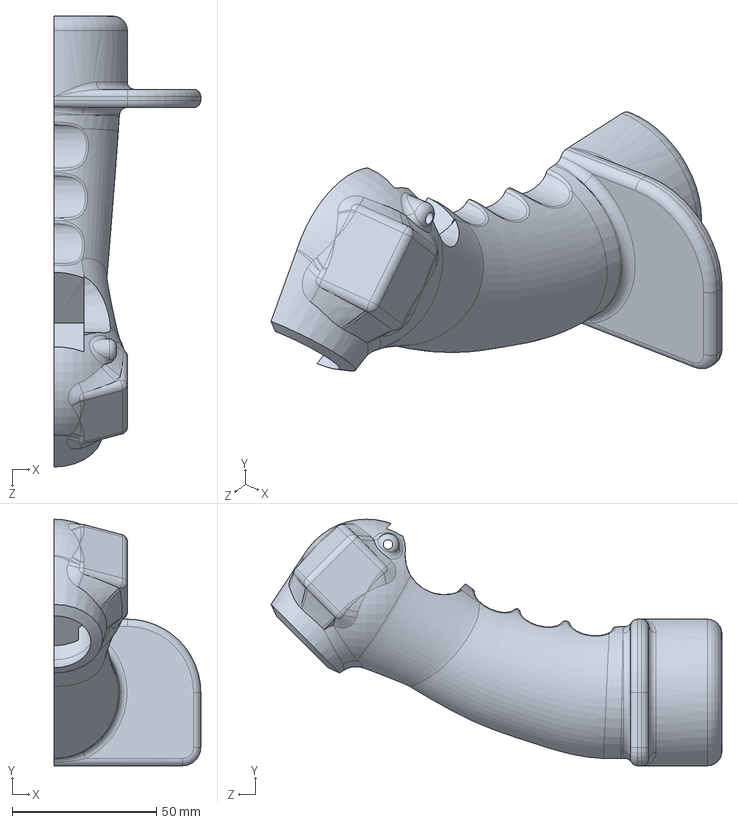
[picture p126: CAD file, 2018-08-11]
Components/Peripherals/B8 flight stick/SLDPRT/b8stick_right_half_no_holes_b8stick01.SLDPRT
50.8 x 85.4 x 156.2 mm
