hc625ma/simchair_models/Components/Peripherals/dev/B206 collective head/SLDPRT/b206_head_enclosure_p2_b206_head02.SLDPRT

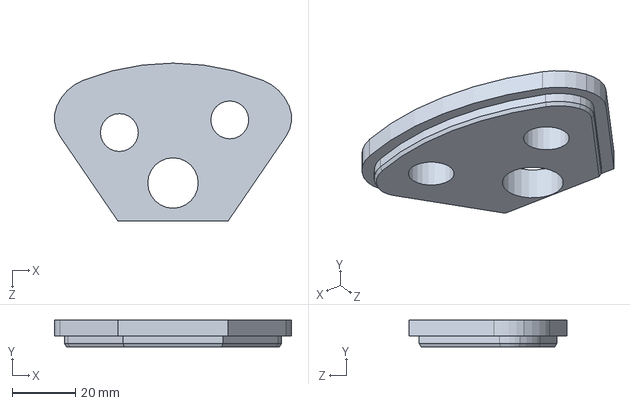
[picture p127: CAD file, 2019-03-17]
Components/Peripherals/dev/B206 collective head/SLDPRT/b206_head_enclosure_p2_b206_head02.SLDPRT
75.1 x 8.40 x 50.0 mm
