hc625ma/simchair_models/Components/Peripherals/dev/Flight stick gimbal 608zz reinforced v2/SLDPRT/gimbal_stick_connector_p1_gimbal08.SLDPRT

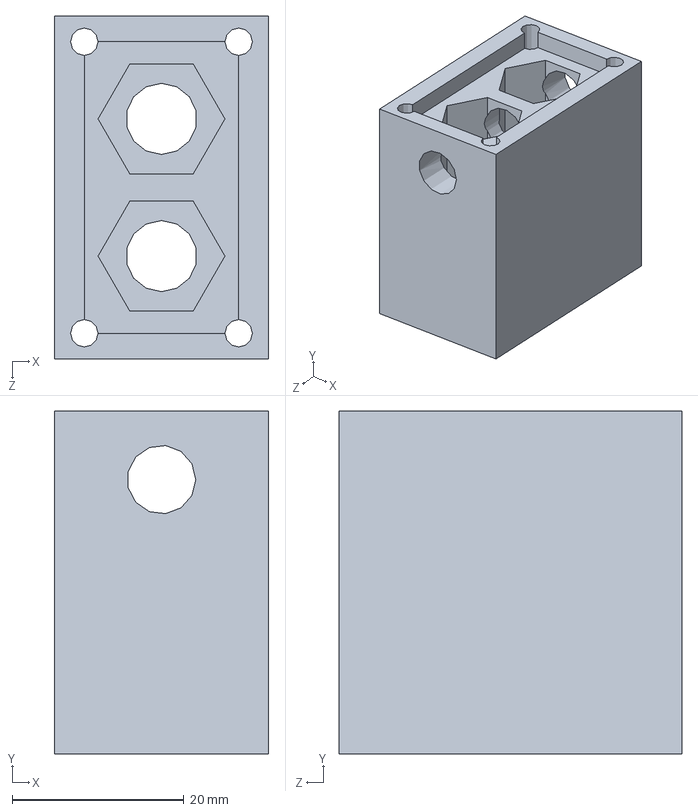
[picture p128: CAD file, 2019-05-10]
Components/Peripherals/dev/Flight stick gimbal 608zz reinforced v2/SLDPRT/gimbal_stick_connector_p1_gimbal08.SLDPRT
25.0 x 40.0 x 40.0 mm
