hc625ma/simchair_models/Components/Peripherals/dev/Flight stick gimbal GE25 ES-2RS/SLDPRT/gimbal_housing_testbed_gimbal01a.SLDPRT

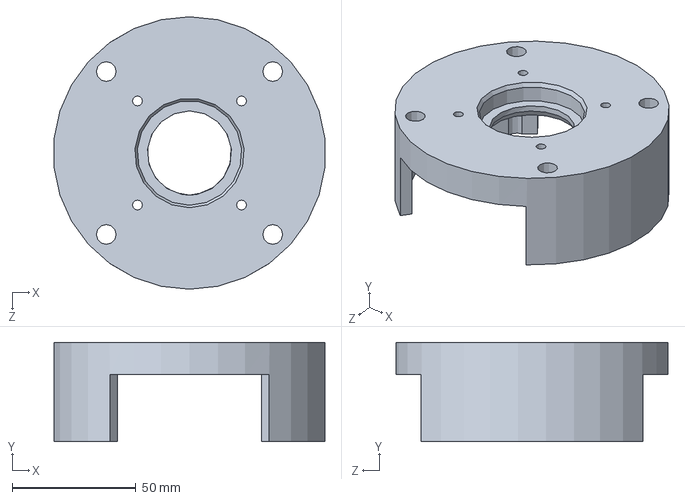
[picture p129: CAD file, 2018-10-22]
Components/Peripherals/dev/Flight stick gimbal GE25 ES-2RS/SLDPRT/gimbal_housing_testbed_gimbal01a.SLDPRT
109.4 x 40.0 x 110.0 mm
