hc625ma/simchair_models/Components/Peripherals/dev/Helicopter throttle quadrant/SLDPRT/mi8_throttle.SLDPRT

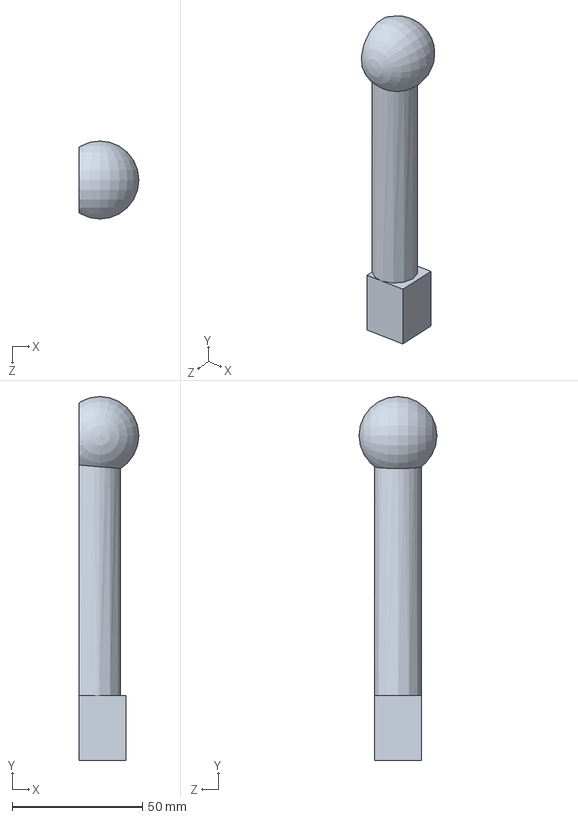
[picture p130: CAD file, 2019-05-10]
Components/Peripherals/dev/Helicopter throttle quadrant/SLDPRT/mi8_throttle.SLDPRT
23.0 x 140.0 x 30.0 mm
