hc625ma/simchair_models/Components/Peripherals/dev/Simple collective/SLDPRT/collective_connector.SLDPRT

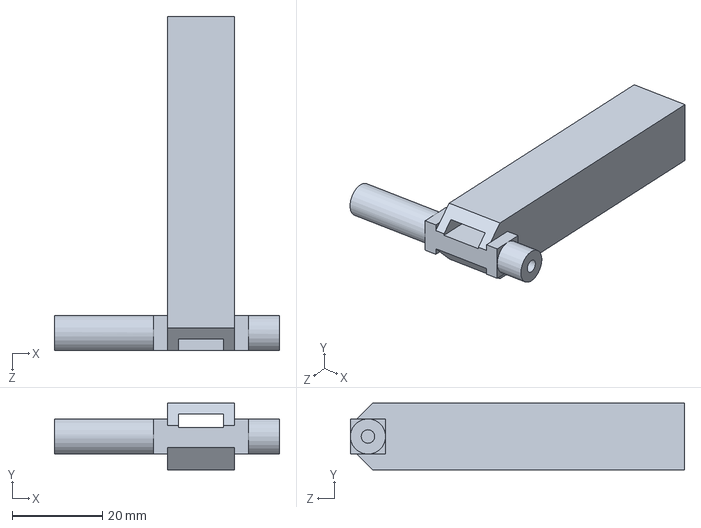
[picture p131: CAD file, 2019-02-21]
Components/Peripherals/dev/Simple collective/SLDPRT/collective_connector.SLDPRT
49.8 x 14.8 x 74.0 mm
