hc625ma/simchair_models/Components/Peripherals/dev/Simple collective/STL/enclosure_bottom.stl

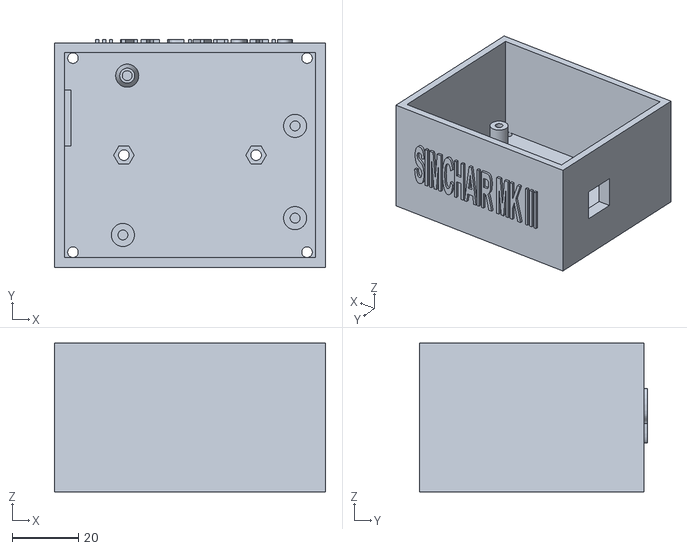
[picture p132: CAD file, 2019-02-21]
Components/Peripherals/dev/Simple collective/STL/enclosure_bottom.stl
82.0 x 69.0 x 45.0
