hc625ma/simchair_models/Components/Peripherals/Flight stick gimbal 608zz light/SLDPRT/gimbal_enclosure_bottom_p1_gimbal02.SLDPRT

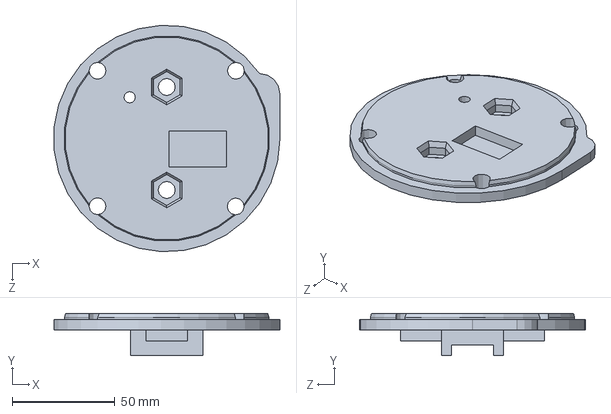
[picture p133: CAD file, 2018-08-09]
Components/Peripherals/Flight stick gimbal 608zz light/SLDPRT/gimbal_enclosure_bottom_p1_gimbal02.SLDPRT
109.7 x 20.5 x 109.9 mm
