hc625ma/simchair_models/Components/Peripherals/Flight stick gimbal 608zz reinforced/STL/gimbal_Y_sensor_hatch_cover_gimbal20.STL

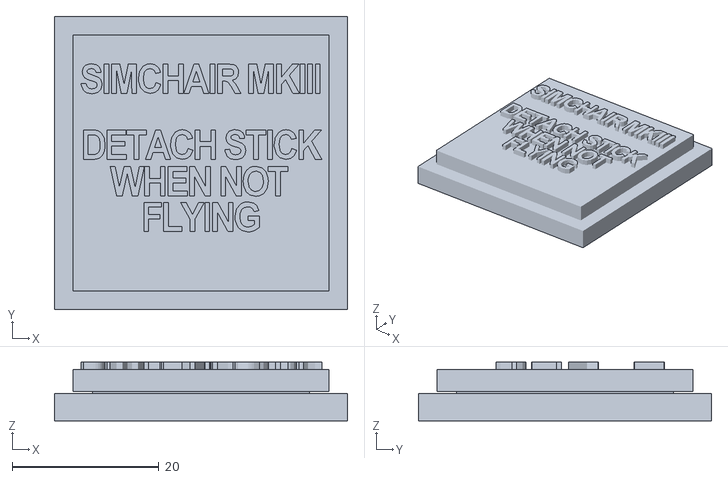
[picture p134: CAD file, 2019-02-06]
Components/Peripherals/Flight stick gimbal 608zz reinforced/STL/gimbal_Y_sensor_hatch_cover_gimbal20.STL
40.0 x 40.0 x 8.00
