hc625ma/simchair_models/Components/Peripherals/Helicopter pedals/SLDPRT/pedals_front_cover_pedals10.SLDPRT

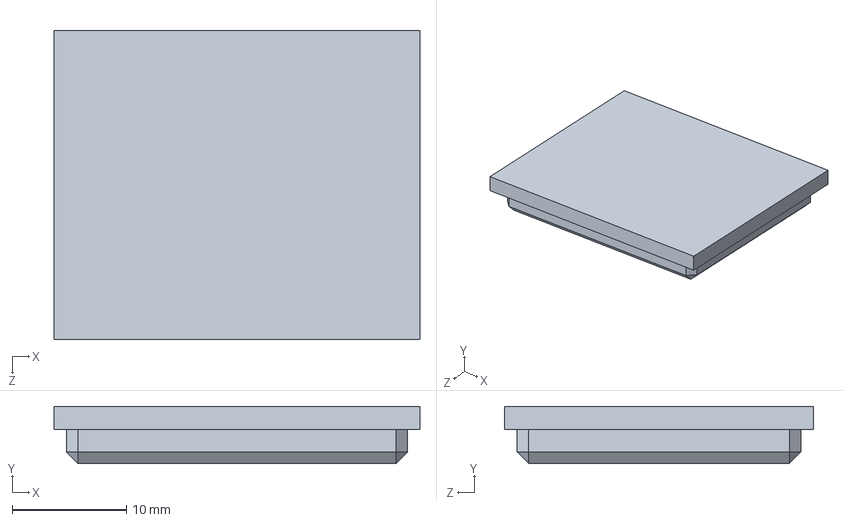
[picture p135: CAD file, 2018-12-15]
Components/Peripherals/Helicopter pedals/SLDPRT/pedals_front_cover_pedals10.SLDPRT
32.0 x 5.00 x 27.0 mm
