hc625ma/simchair_models/Components/Peripherals/Huey collective head/STL/huey_head_pot_frame_huey_head03.STL

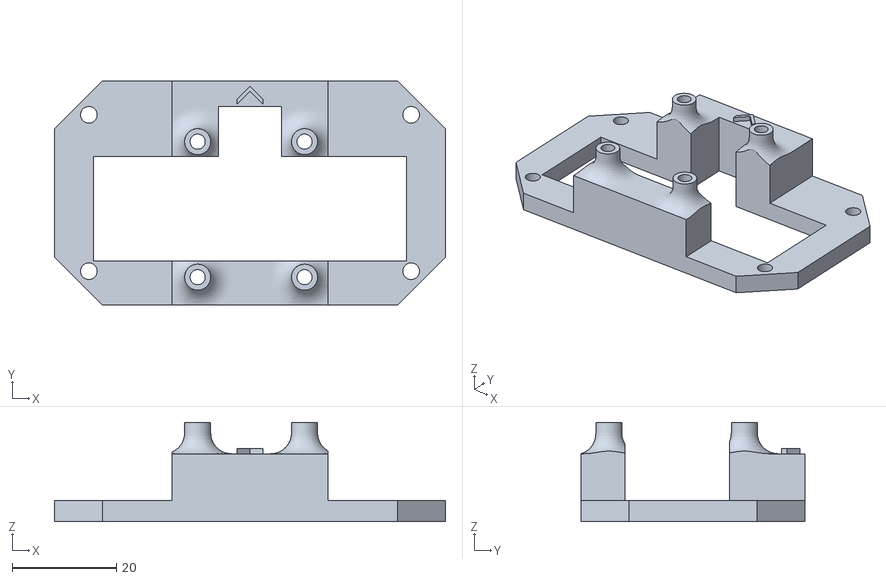
[picture p136: CAD file, 2018-08-11]
Components/Peripherals/Huey collective head/STL/huey_head_pot_frame_huey_head03.STL
75.0 x 43.0 x 19.0
