hc625ma/simchair_models/Components/Peripherals/Single collective/SLDPRT/single_collective_throttle_frame_p1_single_collective09.SLDPRT

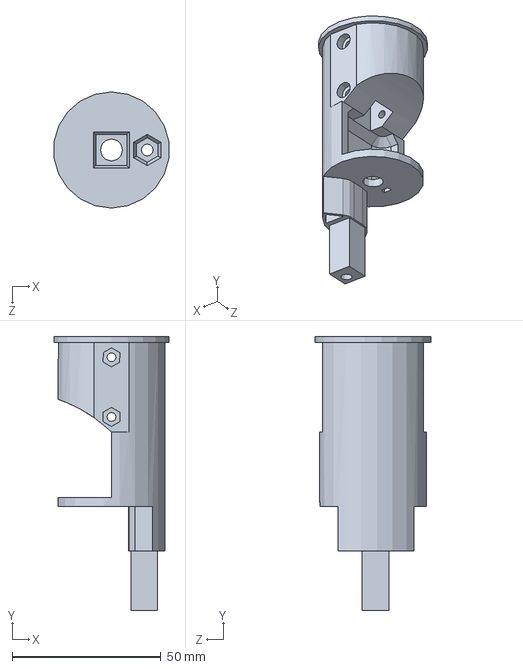
[picture p137: CAD file, 2019-05-10]
Components/Peripherals/Single collective/SLDPRT/single_collective_throttle_frame_p1_single_collective09.SLDPRT
38.6 x 92.0 x 39.0 mm
