hc625ma/simchair_models/Components/Peripherals/Twin collective/SLDPRT/twin_collective_throttle1_frame_p2_twin_collective13.SLDPRT

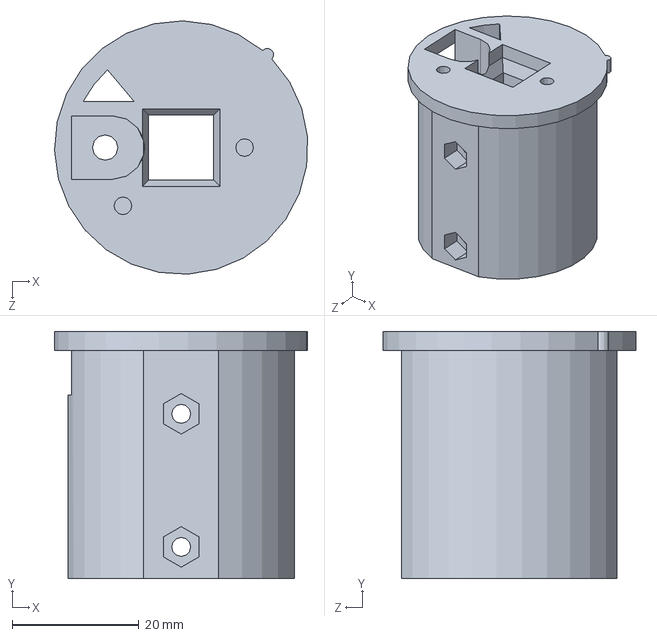
[picture p138: CAD file, 2018-08-24]
Components/Peripherals/Twin collective/SLDPRT/twin_collective_throttle1_frame_p2_twin_collective13.SLDPRT
39.9 x 39.0 x 40.0 mm
