hc625ma/simchair_models/Hardware Models/GE25 ES-2RS/outer_ring.SLDPRT

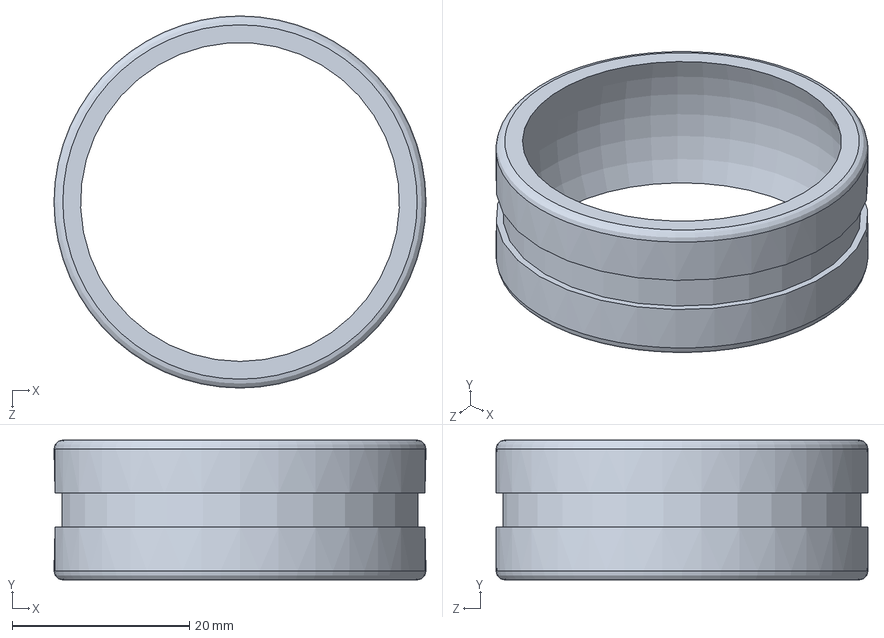
[picture p139: CAD file, 2018-10-19]
Hardware Models/GE25 ES-2RS/outer_ring.SLDPRT
42.0 x 15.8 x 42.0 mm
