hc625ma/simchair_models/Mods/Peripherals/Collective levers/All levers/Pneumatic actuator mod/SLDPRT/Assembly/aluminium_rectangular_pipe_10x20x300mm.SLDPRT

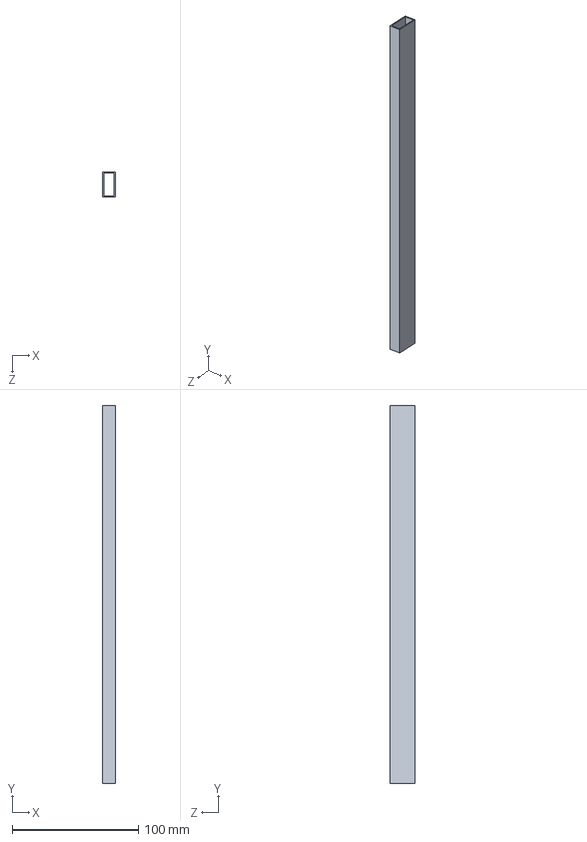
[picture p140: CAD file, 2018-10-23]
Mods/Peripherals/Collective levers/All levers/Pneumatic actuator mod/SLDPRT/Assembly/aluminium_rectangular_pipe_10x20x300mm.SLDPRT
10.0 x 300.0 x 20.0 mm
