hc625ma/simchair_models/Components/Peripherals/dev/Simple collective/MANUALS/collective1.png

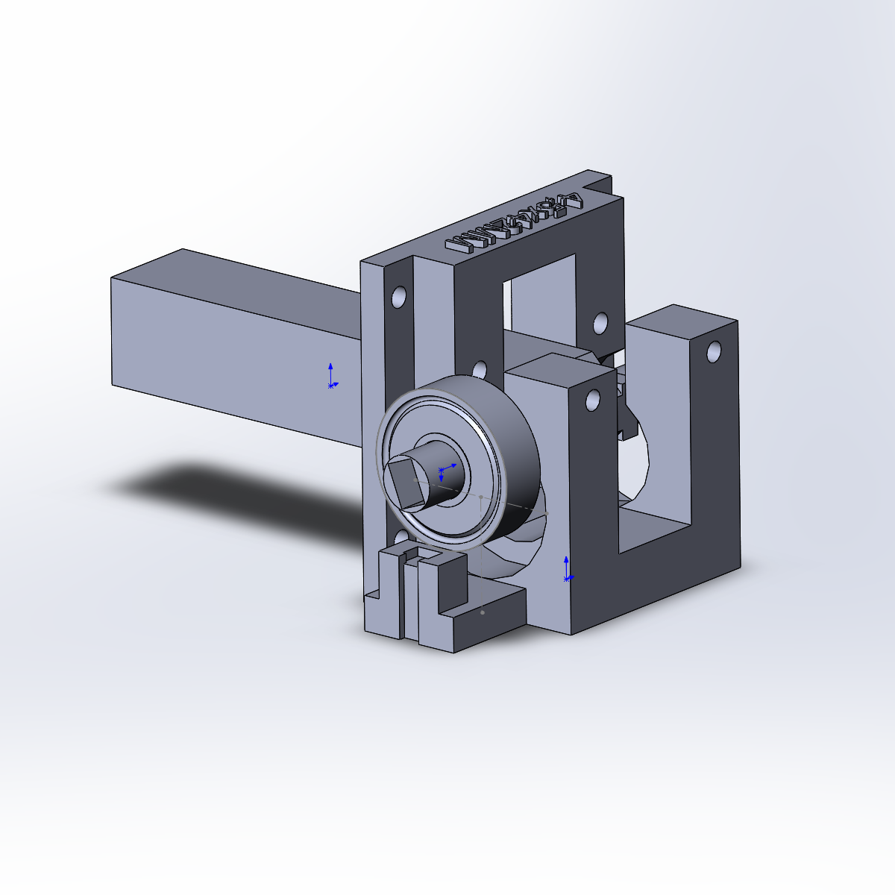
Components/Peripherals/dev/Simple collective/MANUALS/collective1.png
