hc625ma/simchair_models/Components/Peripherals/dev/Simple collective/MANUALS/collective3.png

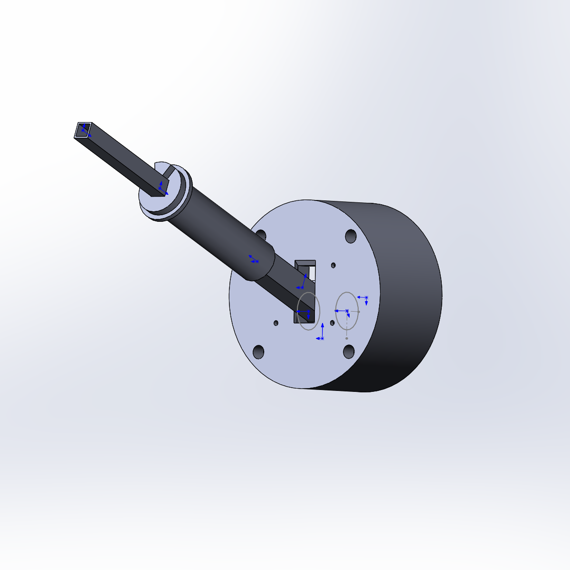
Components/Peripherals/dev/Simple collective/MANUALS/collective3.png
