hc625ma/simchair_models/Components/Peripherals/dev/Simple collective/MANUALS/collective4.png

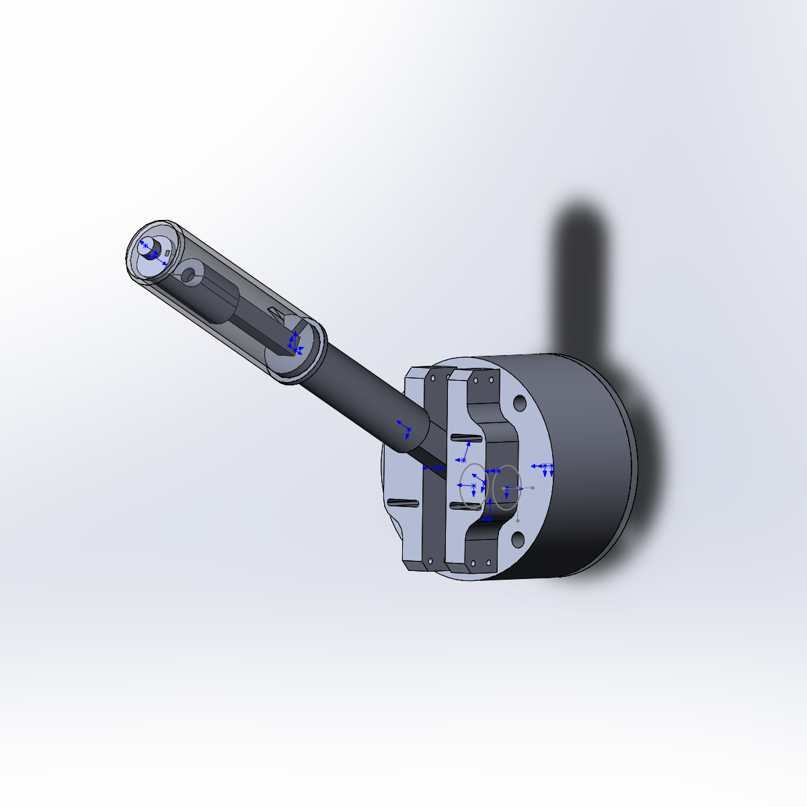
Components/Peripherals/dev/Simple collective/MANUALS/collective4.png
