hc625ma/simchair_models/Components/Peripherals/Flight stick gimbal 608zz light/MANUALS/cyclic1.png

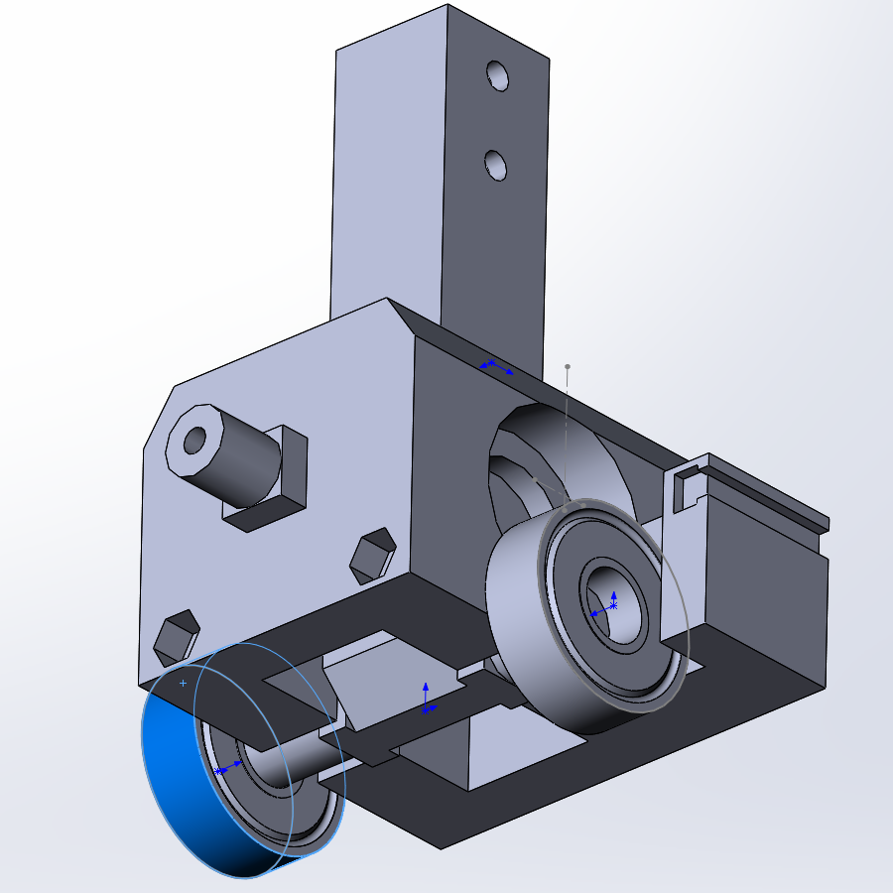
Components/Peripherals/Flight stick gimbal 608zz light/MANUALS/cyclic1.png
