hc625ma/simchair_models/Components/Peripherals/Helicopter pedals/MANUALS/pedals1.jpg

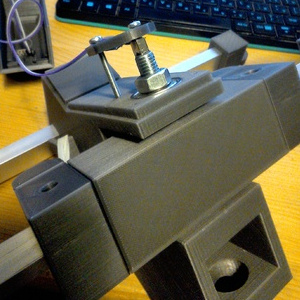
Components/Peripherals/Helicopter pedals/MANUALS/pedals1.jpg
